Syntaxer04/RC1Computer/Version 0.2/Bridge V2/Bridge V2.kicad_pcb

## KiCad design Version 0.2/Bridge V2/Bridge V2.kicad_pcb (2026-01-20)

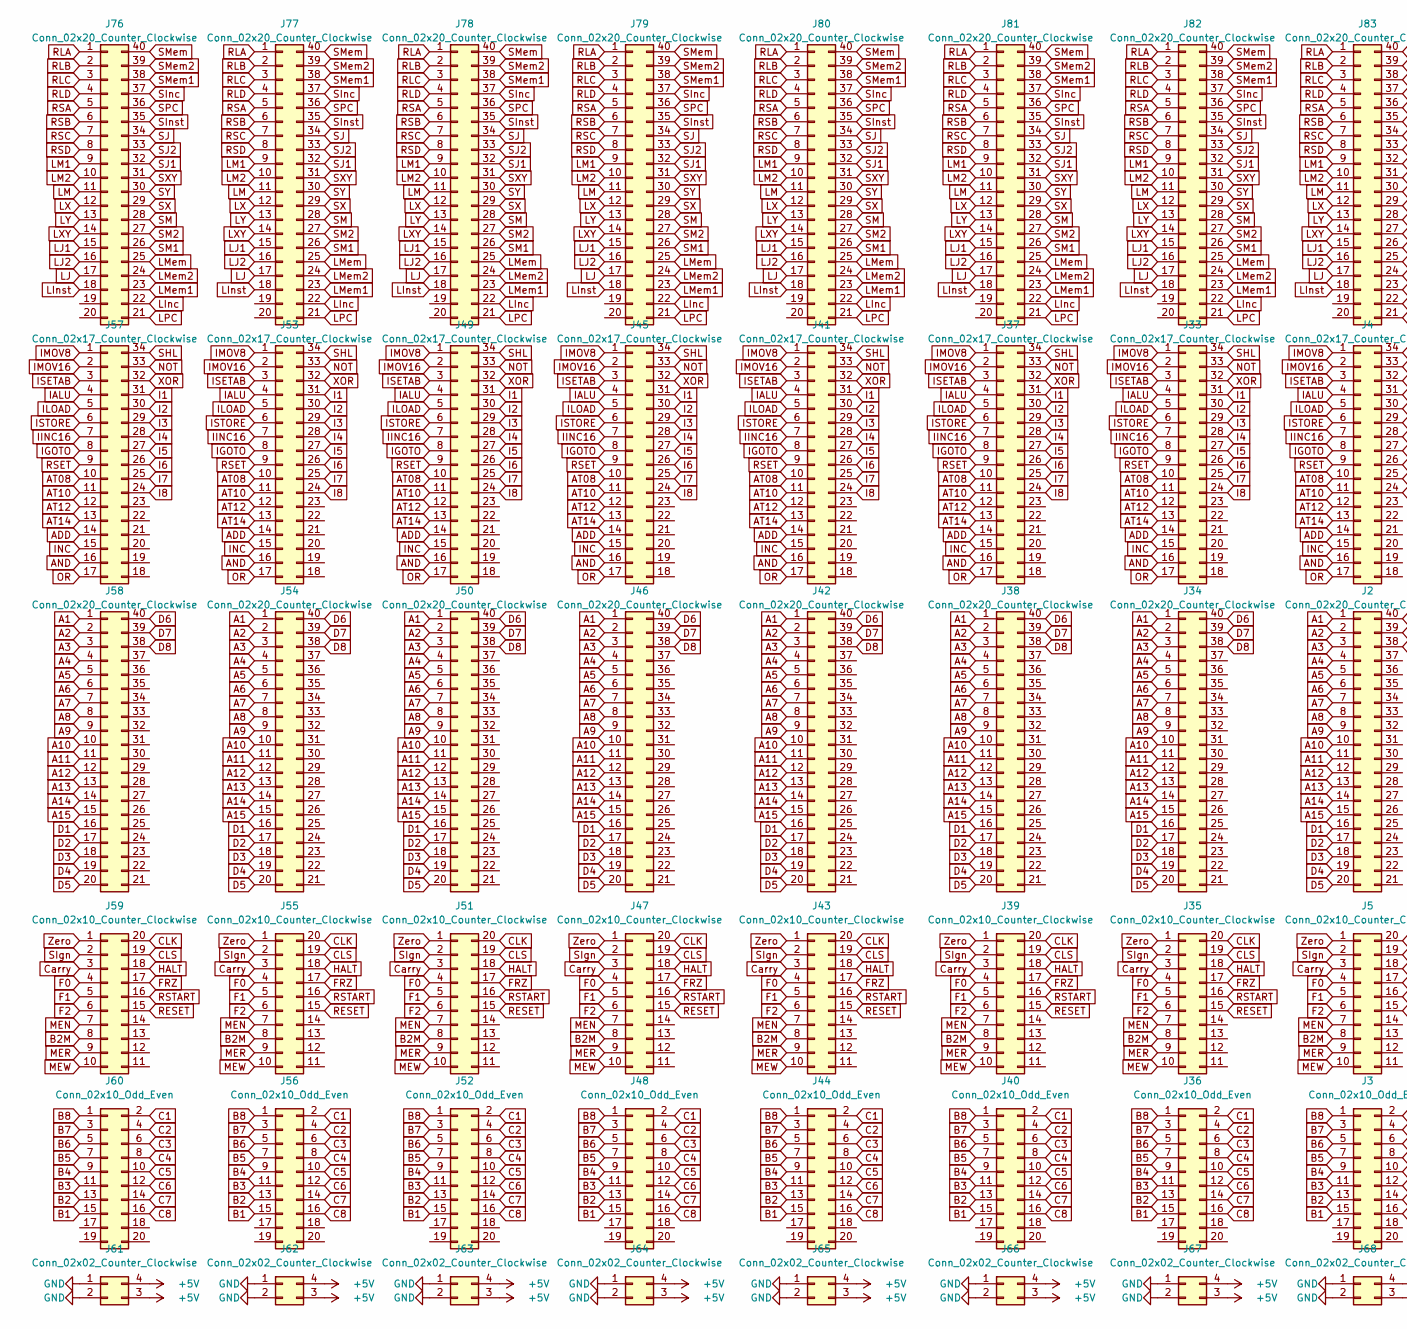
[picture p41: schematic Bridge V2.kicad_sch, part in row 1, column 1]

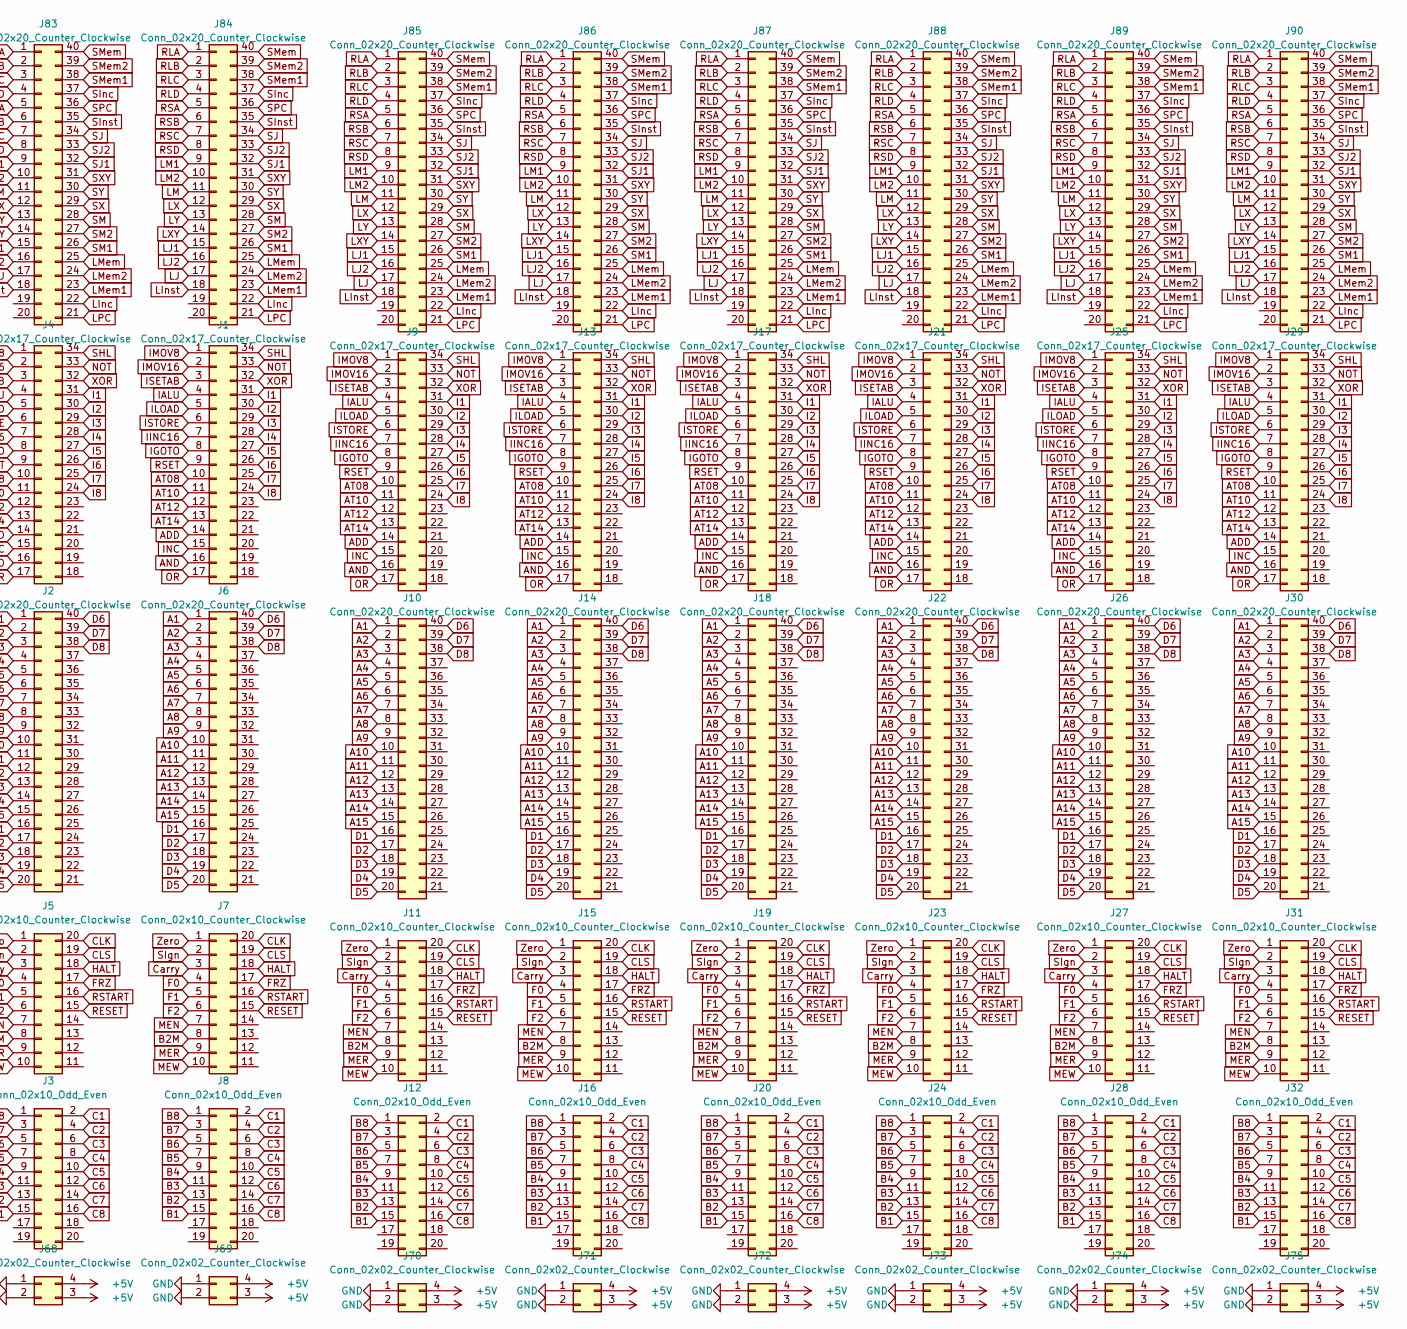
[picture p42: schematic Bridge V2.kicad_sch, part in row 1, column 2]

Parts:
J1, J4, J9, J13, J17, J21, J25, J29, J33, J37, J41, J45, J49, J53, J57: Conn_02x17_Counter_Clockwise; PinSocket_2x17_P2.54mm_Vertical
J2, J6, J10, J14, J18, J22, J26, J30, J34, J38, J42, J46, J50, J54, J58, J76, J77, J78, J79, J80, J81, J82, J83, J84, J85, J86, J87, J88, J89, J90: Conn_02x20_Counter_Clockwise; PinSocket_2x20_P2.54mm_Vertical
J3, J8, J12, J16, J20, J24, J28, J32, J36, J40, J44, J48, J52, J56, J60: Conn_02x10_Odd_Even; PinSocket_2x10_P2.54mm_Vertical
J5, J7, J11, J15, J19, J23, J27, J31, J35, J39, J43, J47, J51, J55, J59: Conn_02x10_Counter_Clockwise; PinSocket_2x10_P2.54mm_Vertical
J61, J62, J63, J64, J65, J66, J67, J68, J69, J70, J71, J72, J73, J74, J75: Conn_02x02_Counter_Clockwise; PinSocket_2x02_P2.54mm_Vertical

Connections:
+5V: J61.3, J61.4, J62.3, J62.4, J63.3, J63.4, J64.3, J64.4, J65.3, J65.4, J66.3, J66.4, J67.3, J67.4, J68.3, J68.4, J69.3, J69.4, J70.3, J70.4, J71.3, J71.4, J72.3, J72.4, J73.3, J73.4, J74.3, J74.4, J75.3, J75.4
A1: J2.1, J6.1, J10.1, J14.1, J18.1, J22.1, J26.1, J30.1, J34.1, J38.1, J42.1, J46.1, J50.1, J54.1, J58.1
A2: J2.2, J6.2, J10.2, J14.2, J18.2, J22.2, J26.2, J30.2, J34.2, J38.2, J42.2, J46.2, J50.2, J54.2, J58.2
A3: J2.3, J6.3, J10.3, J14.3, J18.3, J22.3, J26.3, J30.3, J34.3, J38.3, J42.3, J46.3, J50.3, J54.3, J58.3
A4: J2.4, J6.4, J10.4, J14.4, J18.4, J22.4, J26.4, J30.4, J34.4, J38.4, J42.4, J46.4, J50.4, J54.4, J58.4
A5: J2.5, J6.5, J10.5, J14.5, J18.5, J22.5, J26.5, J30.5, J34.5, J38.5, J42.5, J46.5, J50.5, J54.5, J58.5
A6: J2.6, J6.6, J10.6, J14.6, J18.6, J22.6, J26.6, J30.6, J34.6, J38.6, J42.6, J46.6, J50.6, J54.6, J58.6
A7: J2.7, J6.7, J10.7, J14.7, J18.7, J22.7, J26.7, J30.7, J34.7, J38.7, J42.7, J46.7, J50.7, J54.7, J58.7
A8: J2.8, J6.8, J10.8, J14.8, J18.8, J22.8, J26.8, J30.8, J34.8, J38.8, J42.8, J46.8, J50.8, J54.8, J58.8
A9: J2.9, J6.9, J10.9, J14.9, J18.9, J22.9, J26.9, J30.9, J34.9, J38.9, J42.9, J46.9, J50.9, J54.9, J58.9
A10: J2.10, J6.10, J10.10, J14.10, J18.10, J22.10, J26.10, J30.10, J34.10, J38.10, J42.10, J46.10, J50.10, J54.10, J58.10
A11: J2.11, J6.11, J10.11, J14.11, J18.11, J22.11, J26.11, J30.11, J34.11, J38.11, J42.11, J46.11, J50.11, J54.11, J58.11
A12: J2.12, J6.12, J10.12, J14.12, J18.12, J22.12, J26.12, J30.12, J34.12, J38.12, J42.12, J46.12, J50.12, J54.12, J58.12
A13: J2.13, J6.13, J10.13, J14.13, J18.13, J22.13, J26.13, J30.13, J34.13, J38.13, J42.13, J46.13, J50.13, J54.13, J58.13
A14: J2.14, J6.14, J10.14, J14.14, J18.14, J22.14, J26.14, J30.14, J34.14, J38.14, J42.14, J46.14, J50.14, J54.14, J58.14
A15: J2.15, J6.15, J10.15, J14.15, J18.15, J22.15, J26.15, J30.15, J34.15, J38.15, J42.15, J46.15, J50.15, J54.15, J58.15
ADD: J1.14, J4.14, J9.14, J13.14, J17.14, J21.14, J25.14, J29.14, J33.14, J37.14, J41.14, J45.14, J49.14, J53.14, J57.14
AND: J1.16, J4.16, J9.16, J13.16, J17.16, J21.16, J25.16, J29.16, J33.16, J37.16, J41.16, J45.16, J49.16, J53.16, J57.16
AT08: J1.10, J4.10, J9.10, J13.10, J17.10, J21.10, J25.10, J29.10, J33.10, J37.10, J41.10, J45.10, J49.10, J53.10, J57.10
AT10: J1.11, J4.11, J9.11, J13.11, J17.11, J21.11, J25.11, J29.11, J33.11, J37.11, J41.11, J45.11, J49.11, J53.11, J57.11
AT12: J1.12, J4.12, J9.12, J13.12, J17.12, J21.12, J25.12, J29.12, J33.12, J37.12, J41.12, J45.12, J49.12, J53.12, J57.12
AT14: J1.13, J4.13, J9.13, J13.13, J17.13, J21.13, J25.13, J29.13, J33.13, J37.13, J41.13, J45.13, J49.13, J53.13, J57.13
B1: J3.15, J8.15, J12.15, J16.15, J20.15, J24.15, J28.15, J32.15, J36.15, J40.15, J44.15, J48.15, J52.15, J56.15, J60.15
B2: J3.13, J8.13, J12.13, J16.13, J20.13, J24.13, J28.13, J32.13, J36.13, J40.13, J44.13, J48.13, J52.13, J56.13, J60.13
B2M: J5.8, J7.8, J11.8, J15.8, J19.8, J23.8, J27.8, J31.8, J35.8, J39.8, J43.8, J47.8, J51.8, J55.8, J59.8
B3: J3.11, J8.11, J12.11, J16.11, J20.11, J24.11, J28.11, J32.11, J36.11, J40.11, J44.11, J48.11, J52.11, J56.11, J60.11
B4: J3.9, J8.9, J12.9, J16.9, J20.9, J24.9, J28.9, J32.9, J36.9, J40.9, J44.9, J48.9, J52.9, J56.9, J60.9
B5: J3.7, J8.7, J12.7, J16.7, J20.7, J24.7, J28.7, J32.7, J36.7, J40.7, J44.7, J48.7, J52.7, J56.7, J60.7
B6: J3.5, J8.5, J12.5, J16.5, J20.5, J24.5, J28.5, J32.5, J36.5, J40.5, J44.5, J48.5, J52.5, J56.5, J60.5
B7: J3.3, J8.3, J12.3, J16.3, J20.3, J24.3, J28.3, J32.3, J36.3, J40.3, J44.3, J48.3, J52.3, J56.3, J60.3
B8: J3.1, J8.1, J12.1, J16.1, J20.1, J24.1, J28.1, J32.1, J36.1, J40.1, J44.1, J48.1, J52.1, J56.1, J60.1
C1: J3.2, J8.2, J12.2, J16.2, J20.2, J24.2, J28.2, J32.2, J36.2, J40.2, J44.2, J48.2, J52.2, J56.2, J60.2
C2: J3.4, J8.4, J12.4, J16.4, J20.4, J24.4, J28.4, J32.4, J36.4, J40.4, J44.4, J48.4, J52.4, J56.4, J60.4
C3: J3.6, J8.6, J12.6, J16.6, J20.6, J24.6, J28.6, J32.6, J36.6, J40.6, J44.6, J48.6, J52.6, J56.6, J60.6
C4: J3.8, J8.8, J12.8, J16.8, J20.8, J24.8, J28.8, J32.8, J36.8, J40.8, J44.8, J48.8, J52.8, J56.8, J60.8
C5: J3.10, J8.10, J12.10, J16.10, J20.10, J24.10, J28.10, J32.10, J36.10, J40.10, J44.10, J48.10, J52.10, J56.10, J60.10
C6: J3.12, J8.12, J12.12, J16.12, J20.12, J24.12, J28.12, J32.12, J36.12, J40.12, J44.12, J48.12, J52.12, J56.12, J60.12
C7: J3.14, J8.14, J12.14, J16.14, J20.14, J24.14, J28.14, J32.14, J36.14, J40.14, J44.14, J48.14, J52.14, J56.14, J60.14
C8: J3.16, J8.16, J12.16, J16.16, J20.16, J24.16, J28.16, J32.16, J36.16, J40.16, J44.16, J48.16, J52.16, J56.16, J60.16
CLK: J5.20, J7.20, J11.20, J15.20, J19.20, J23.20, J27.20, J31.20, J35.20, J39.20, J43.20, J47.20, J51.20, J55.20, J59.20
CLS: J5.19, J7.19, J11.19, J15.19, J19.19, J23.19, J27.19, J31.19, J35.19, J39.19, J43.19, J47.19, J51.19, J55.19, J59.19
Carry: J5.3, J7.3, J11.3, J15.3, J19.3, J23.3, J27.3, J31.3, J35.3, J39.3, J43.3, J47.3, J51.3, J55.3, J59.3
D1: J2.16, J6.16, J10.16, J14.16, J18.16, J22.16, J26.16, J30.16, J34.16, J38.16, J42.16, J46.16, J50.16, J54.16, J58.16
D2: J2.17, J6.17, J10.17, J14.17, J18.17, J22.17, J26.17, J30.17, J34.17, J38.17, J42.17, J46.17, J50.17, J54.17, J58.17
D3: J2.18, J6.18, J10.18, J14.18, J18.18, J22.18, J26.18, J30.18, J34.18, J38.18, J42.18, J46.18, J50.18, J54.18, J58.18
D4: J2.19, J6.19, J10.19, J14.19, J18.19, J22.19, J26.19, J30.19, J34.19, J38.19, J42.19, J46.19, J50.19, J54.19, J58.19
D5: J2.20, J6.20, J10.20, J14.20, J18.20, J22.20, J26.20, J30.20, J34.20, J38.20, J42.20, J46.20, J50.20, J54.20, J58.20
D6: J2.40, J6.40, J10.40, J14.40, J18.40, J22.40, J26.40, J30.40, J34.40, J38.40, J42.40, J46.40, J50.40, J54.40, J58.40
D7: J2.39, J6.39, J10.39, J14.39, J18.39, J22.39, J26.39, J30.39, J34.39, J38.39, J42.39, J46.39, J50.39, J54.39, J58.39
D8: J2.38, J6.38, J10.38, J14.38, J18.38, J22.38, J26.38, J30.38, J34.38, J38.38, J42.38, J46.38, J50.38, J54.38, J58.38
F0: J5.4, J7.4, J11.4, J15.4, J19.4, J23.4, J27.4, J31.4, J35.4, J39.4, J43.4, J47.4, J51.4, J55.4, J59.4
F1: J5.5, J7.5, J11.5, J15.5, J19.5, J23.5, J27.5, J31.5, J35.5, J39.5, J43.5, J47.5, J51.5, J55.5, J59.5
F2: J5.6, J7.6, J11.6, J15.6, J19.6, J23.6, J27.6, J31.6, J35.6, J39.6, J43.6, J47.6, J51.6, J55.6, J59.6
FRZ: J5.17, J7.17, J11.17, J15.17, J19.17, J23.17, J27.17, J31.17, J35.17, J39.17, J43.17, J47.17, J51.17, J55.17, J59.17
GND: J61.1, J61.2, J62.1, J62.2, J63.1, J63.2, J64.1, J64.2, J65.1, J65.2, J66.1, J66.2, J67.1, J67.2, J68.1, J68.2, J69.1, J69.2, J70.1, J70.2, J71.1, J71.2, J72.1, J72.2, J73.1, J73.2, J74.1, J74.2, J75.1, J75.2
HALT: J5.18, J7.18, J11.18, J15.18, J19.18, J23.18, J27.18, J31.18, J35.18, J39.18, J43.18, J47.18, J51.18, J55.18, J59.18
I1: J1.31, J4.31, J9.31, J13.31, J17.31, J21.31, J25.31, J29.31, J33.31, J37.31, J41.31, J45.31, J49.31, J53.31, J57.31
I2: J1.30, J4.30, J9.30, J13.30, J17.30, J21.30, J25.30, J29.30, J33.30, J37.30, J41.30, J45.30, J49.30, J53.30, J57.30
I3: J1.29, J4.29, J9.29, J13.29, J17.29, J21.29, J25.29, J29.29, J33.29, J37.29, J41.29, J45.29, J49.29, J53.29, J57.29
I4: J1.28, J4.28, J9.28, J13.28, J17.28, J21.28, J25.28, J29.28, J33.28, J37.28, J41.28, J45.28, J49.28, J53.28, J57.28
I5: J1.27, J4.27, J9.27, J13.27, J17.27, J21.27, J25.27, J29.27, J33.27, J37.27, J41.27, J45.27, J49.27, J53.27, J57.27
I6: J1.26, J4.26, J9.26, J13.26, J17.26, J21.26, J25.26, J29.26, J33.26, J37.26, J41.26, J45.26, J49.26, J53.26, J57.26
I7: J1.25, J4.25, J9.25, J13.25, J17.25, J21.25, J25.25, J29.25, J33.25, J37.25, J41.25, J45.25, J49.25, J53.25, J57.25
I8: J1.24, J4.24, J9.24, J13.24, J17.24, J21.24, J25.24, J29.24, J33.24, J37.24, J41.24, J45.24, J49.24, J53.24, J57.24
IALU: J1.4, J4.4, J9.4, J13.4, J17.4, J21.4, J25.4, J29.4, J33.4, J37.4, J41.4, J45.4, J49.4, J53.4, J57.4
IGOTO: J1.8, J4.8, J9.8, J13.8, J17.8, J21.8, J25.8, J29.8, J33.8, J37.8, J41.8, J45.8, J49.8, J53.8, J57.8
IINC16: J1.7, J4.7, J9.7, J13.7, J17.7, J21.7, J25.7, J29.7, J33.7, J37.7, J41.7, J45.7, J49.7, J53.7, J57.7
ILOAD: J1.5, J4.5, J9.5, J13.5, J17.5, J21.5, J25.5, J29.5, J33.5, J37.5, J41.5, J45.5, J49.5, J53.5, J57.5
IMOV8: J1.1, J4.1, J9.1, J13.1, J17.1, J21.1, J25.1, J29.1, J33.1, J37.1, J41.1, J45.1, J49.1, J53.1, J57.1
IMOV16: J1.2, J4.2, J9.2, J13.2, J17.2, J21.2, J25.2, J29.2, J33.2, J37.2, J41.2, J45.2, J49.2, J53.2, J57.2
INC: J1.15, J4.15, J9.15, J13.15, J17.15, J21.15, J25.15, J29.15, J33.15, J37.15, J41.15, J45.15, J49.15, J53.15, J57.15
ISETAB: J1.3, J4.3, J9.3, J13.3, J17.3, J21.3, J25.3, J29.3, J33.3, J37.3, J41.3, J45.3, J49.3, J53.3, J57.3
ISTORE: J1.6, J4.6, J9.6, J13.6, J17.6, J21.6, J25.6, J29.6, J33.6, J37.6, J41.6, J45.6, J49.6, J53.6, J57.6
LInc: J76.22, J77.22, J78.22, J79.22, J80.22, J81.22, J82.22, J83.22, J84.22, J85.22, J86.22, J87.22, J88.22, J89.22, J90.22
LInst: J76.18, J77.18, J78.18, J79.18, J80.18, J81.18, J82.18, J83.18, J84.18, J85.18, J86.18, J87.18, J88.18, J89.18, J90.18
LJ1: J76.15, J77.15, J78.15, J79.15, J80.15, J81.15, J82.15, J83.15, J84.15, J85.15, J86.15, J87.15, J88.15, J89.15, J90.15
LJ2: J76.16, J77.16, J78.16, J79.16, J80.16, J81.16, J82.16, J83.16, J84.16, J85.16, J86.16, J87.16, J88.16, J89.16, J90.16
LJ: J76.17, J77.17, J78.17, J79.17, J80.17, J81.17, J82.17, J83.17, J84.17, J85.17, J86.17, J87.17, J88.17, J89.17, J90.17
LM: J76.11, J77.11, J78.11, J79.11, J80.11, J81.11, J82.11, J83.11, J84.11, J85.11, J86.11, J87.11, J88.11, J89.11, J90.11
LM1: J76.9, J77.9, J78.9, J79.9, J80.9, J81.9, J82.9, J83.9, J84.9, J85.9, J86.9, J87.9, J88.9, J89.9, J90.9
LM2: J76.10, J77.10, J78.10, J79.10, J80.10, J81.10, J82.10, J83.10, J84.10, J85.10, J86.10, J87.10, J88.10, J89.10, J90.10
LMem: J76.25, J77.25, J78.25, J79.25, J80.25, J81.25, J82.25, J83.25, J84.25, J85.25, J86.25, J87.25, J88.25, J89.25, J90.25
LMem1: J76.23, J77.23, J78.23, J79.23, J80.23, J81.23, J82.23, J83.23, J84.23, J85.23, J86.23, J87.23, J88.23, J89.23, J90.23
LMem2: J76.24, J77.24, J78.24, J79.24, J80.24, J81.24, J82.24, J83.24, J84.24, J85.24, J86.24, J87.24, J88.24, J89.24, J90.24
LPC: J76.21, J77.21, J78.21, J79.21, J80.21, J81.21, J82.21, J83.21, J84.21, J85.21, J86.21, J87.21, J88.21, J89.21, J90.21
LX: J76.12, J77.12, J78.12, J79.12, J80.12, J81.12, J82.12, J83.12, J84.12, J85.12, J86.12, J87.12, J88.12, J89.12, J90.12
LXY: J76.14, J77.14, J78.14, J79.14, J80.14, J81.14, J82.14, J83.14, J84.14, J85.14, J86.14, J87.14, J88.14, J89.14, J90.14
LY: J76.13, J77.13, J78.13, J79.13, J80.13, J81.13, J82.13, J83.13, J84.13, J85.13, J86.13, J87.13, J88.13, J89.13, J90.13
MEN: J5.7, J7.7, J11.7, J15.7, J19.7, J23.7, J27.7, J31.7, J35.7, J39.7, J43.7, J47.7, J51.7, J55.7, J59.7
MER: J5.9, J7.9, J11.9, J15.9, J19.9, J23.9, J27.9, J31.9, J35.9, J39.9, J43.9, J47.9, J51.9, J55.9, J59.9
MEW: J5.10, J7.10, J11.10, J15.10, J19.10, J23.10, J27.10, J31.10, J35.10, J39.10, J43.10, J47.10, J51.10, J55.10, J59.10
NOT: J1.33, J4.33, J9.33, J13.33, J17.33, J21.33, J25.33, J29.33, J33.33, J37.33, J41.33, J45.33, J49.33, J53.33, J57.33
OR: J1.17, J4.17, J9.17, J13.17, J17.17, J21.17, J25.17, J29.17, J33.17, J37.17, J41.17, J45.17, J49.17, J53.17, J57.17
RESET: J5.15, J7.15, J11.15, J15.15, J19.15, J23.15, J27.15, J31.15, J35.15, J39.15, J43.15, J47.15, J51.15, J55.15, J59.15
RLA: J76.1, J77.1, J78.1, J79.1, J80.1, J81.1, J82.1, J83.1, J84.1, J85.1, J86.1, J87.1, J88.1, J89.1, J90.1
RLB: J76.2, J77.2, J78.2, J79.2, J80.2, J81.2, J82.2, J83.2, J84.2, J85.2, J86.2, J87.2, J88.2, J89.2, J90.2
RLC: J76.3, J77.3, J78.3, J79.3, J80.3, J81.3, J82.3, J83.3, J84.3, J85.3, J86.3, J87.3, J88.3, J89.3, J90.3
RLD: J76.4, J77.4, J78.4, J79.4, J80.4, J81.4, J82.4, J83.4, J84.4, J85.4, J86.4, J87.4, J88.4, J89.4, J90.4
RSA: J76.5, J77.5, J78.5, J79.5, J80.5, J81.5, J82.5, J83.5, J84.5, J85.5, J86.5, J87.5, J88.5, J89.5, J90.5
RSB: J76.6, J77.6, J78.6, J79.6, J80.6, J81.6, J82.6, J83.6, J84.6, J85.6, J86.6, J87.6, J88.6, J89.6, J90.6
RSC: J76.7, J77.7, J78.7, J79.7, J80.7, J81.7, J82.7, J83.7, J84.7, J85.7, J86.7, J87.7, J88.7, J89.7, J90.7
RSD: J76.8, J77.8, J78.8, J79.8, J80.8, J81.8, J82.8, J83.8, J84.8, J85.8, J86.8, J87.8, J88.8, J89.8, J90.8
RSET: J1.9, J4.9, J9.9, J13.9, J17.9, J21.9, J25.9, J29.9, J33.9, J37.9, J41.9, J45.9, J49.9, J53.9, J57.9
RSTART: J5.16, J7.16, J11.16, J15.16, J19.16, J23.16, J27.16, J31.16, J35.16, J39.16, J43.16, J47.16, J51.16, J55.16, J59.16
SHL: J1.34, J4.34, J9.34, J13.34, J17.34, J21.34, J25.34, J29.34, J33.34, J37.34, J41.34, J45.34, J49.34, J53.34, J57.34
SIgn: J5.2, J7.2, J11.2, J15.2, J19.2, J23.2, J27.2, J31.2, J35.2, J39.2, J43.2, J47.2, J51.2, J55.2, J59.2
SInc: J76.37, J77.37, J78.37, J79.37, J80.37, J81.37, J82.37, J83.37, J84.37, J85.37, J86.37, J87.37, J88.37, J89.37, J90.37
SInst: J76.35, J77.35, J78.35, J79.35, J80.35, J81.35, J82.35, J83.35, J84.35, J85.35, J86.35, J87.35, J88.35, J89.35, J90.35
SJ1: J76.32, J77.32, J78.32, J79.32, J80.32, J81.32, J82.32, J83.32, J84.32, J85.32, J86.32, J87.32, J88.32, J89.32, J90.32
SJ2: J76.33, J77.33, J78.33, J79.33, J80.33, J81.33, J82.33, J83.33, J84.33, J85.33, J86.33, J87.33, J88.33, J89.33, J90.33
SJ: J76.34, J77.34, J78.34, J79.34, J80.34, J81.34, J82.34, J83.34, J84.34, J85.34, J86.34, J87.34, J88.34, J89.34, J90.34
SM: J76.28, J77.28, J78.28, J79.28, J80.28, J81.28, J82.28, J83.28, J84.28, J85.28, J86.28, J87.28, J88.28, J89.28, J90.28
SM1: J76.26, J77.26, J78.26, J79.26, J80.26, J81.26, J82.26, J83.26, J84.26, J85.26, J86.26, J87.26, J88.26, J89.26, J90.26
SM2: J76.27, J77.27, J78.27, J79.27, J80.27, J81.27, J82.27, J83.27, J84.27, J85.27, J86.27, J87.27, J88.27, J89.27, J90.27
SMem: J76.40, J77.40, J78.40, J79.40, J80.40, J81.40, J82.40, J83.40, J84.40, J85.40, J86.40, J87.40, J88.40, J89.40, J90.40
SMem1: J76.38, J77.38, J78.38, J79.38, J80.38, J81.38, J82.38, J83.38, J84.38, J85.38, J86.38, J87.38, J88.38, J89.38, J90.38
SMem2: J76.39, J77.39, J78.39, J79.39, J80.39, J81.39, J82.39, J83.39, J84.39, J85.39, J86.39, J87.39, J88.39, J89.39, J90.39
SPC: J76.36, J77.36, J78.36, J79.36, J80.36, J81.36, J82.36, J83.36, J84.36, J85.36, J86.36, J87.36, J88.36, J89.36, J90.36
SX: J76.29, J77.29, J78.29, J79.29, J80.29, J81.29, J82.29, J83.29, J84.29, J85.29, J86.29, J87.29, J88.29, J89.29, J90.29
SXY: J76.31, J77.31, J78.31, J79.31, J80.31, J81.31, J82.31, J83.31, J84.31, J85.31, J86.31, J87.31, J88.31, J89.31, J90.31
SY: J76.30, J77.30, J78.30, J79.30, J80.30, J81.30, J82.30, J83.30, J84.30, J85.30, J86.30, J87.30, J88.30, J89.30, J90.30
XOR: J1.32, J4.32, J9.32, J13.32, J17.32, J21.32, J25.32, J29.32, J33.32, J37.32, J41.32, J45.32, J49.32, J53.32, J57.32
Zero: J5.1, J7.1, J11.1, J15.1, J19.1, J23.1, J27.1, J31.1, J35.1, J39.1, J43.1, J47.1, J51.1, J55.1, J59.1

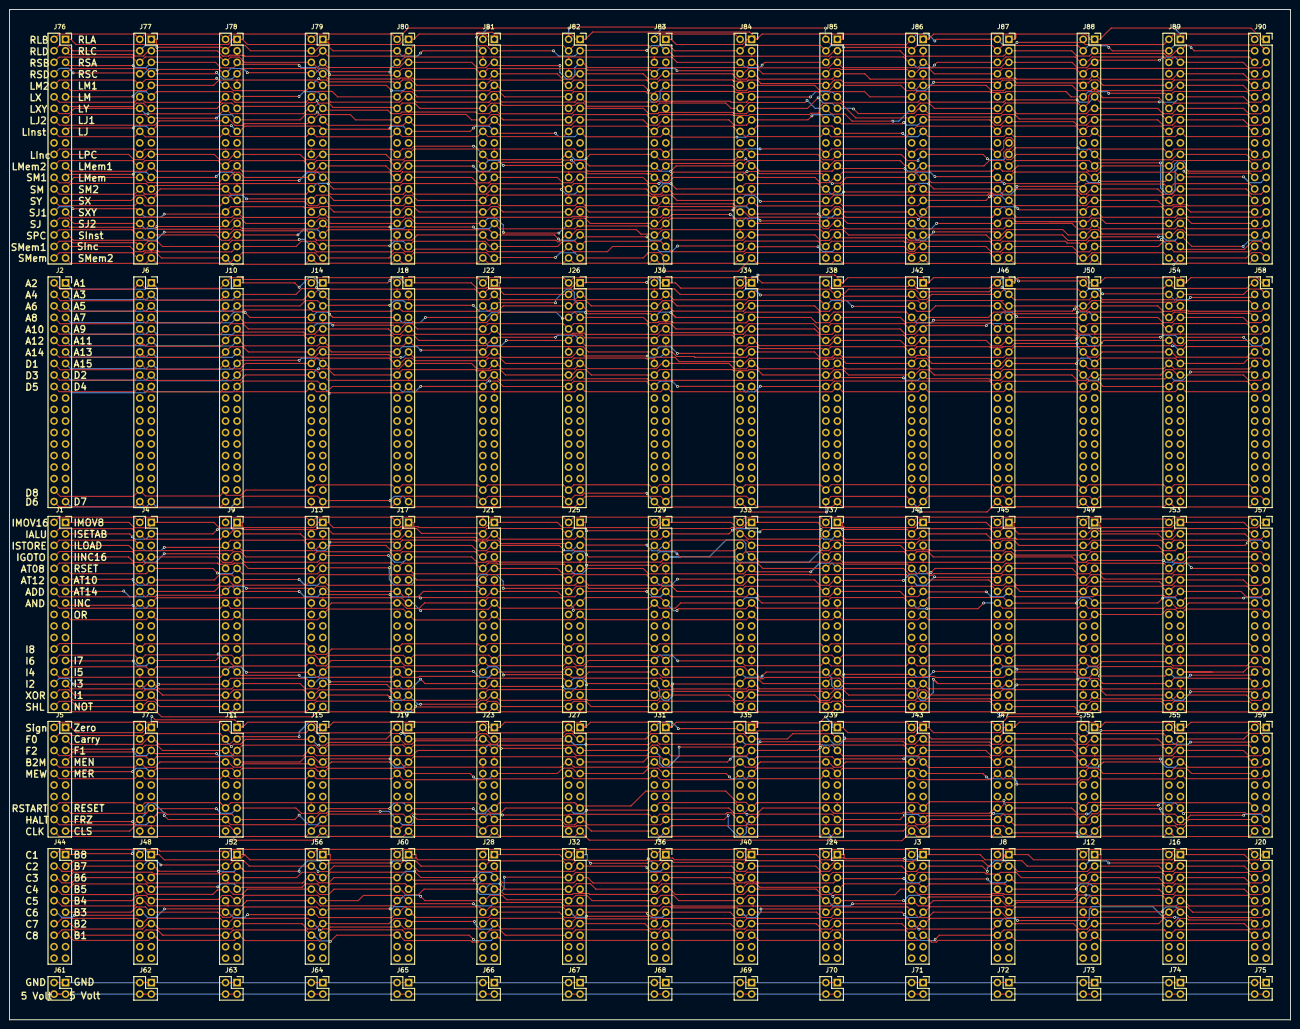
[picture p43: board Bridge V2.kicad_pcb from above]

Board: 2 copper layers, 282.7 x 222.9 mm, 90 parts (0 on the bottom side), 123 nets.
