Syntaxer04/RC1Computer/Version 0.1/Memory/Memory.kicad_pcb

## KiCad design Version 0.1/Memory/Memory.kicad_pcb (2025-06-25, an earlier design)

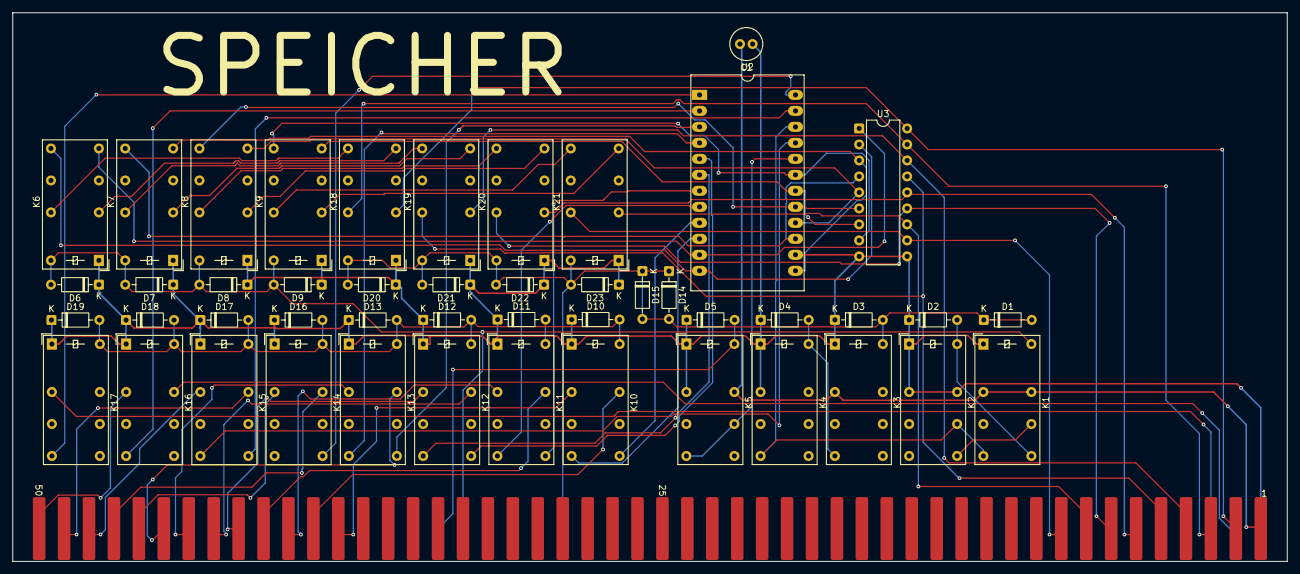
[picture p44: board Memory.kicad_pcb from above]

Board: 2 copper layers, 202.4 x 87.1 mm, 48 parts (0 on the bottom side), 63 nets.

Parts:
C1: C; C_Radial_D5.0mm_H11.0mm_P2.00mm
D1, D2, D3, D4, D5, D6, D7, D8, D9, D10, D11, D12, D13, D14, D15, D16, D17, D18, D19, D20, D21, D22, D23: 1N914; D_DO-35_SOD27_P7.62mm_Horizontal
K1, K2, K3, K4, K5, K6, K7, K8, K9, K10, K11, K12, K13, K14, K15, K16, K17, K18, K19, K20, K21: HK19F-DCxxV-SHC; Relay_DPDT_Finder_30.22
U1: Conn_RC_Male_100
U2: CY62256-70PC; DIP-24_18.0mmx34.29mm_W15.24mm_LongPads
U3: ULN2803A; DIP-18_W7.62mm

Connections:
+5V: C1.2, K1.11, K1.21, K3.11, K5.21, U1.1 (5_Volt)
A0: K10.11, U1.38 (A0)
A1: K10.21, U1.39 (A1)
A2: K11.11, U1.40 (A2)
A3: K11.21, U1.41 (A3)
A4: K12.11, U1.42 (A4)
A5: K12.21, U1.43 (A5)
A6: K13.11, U1.44 (A6)
A7: K13.21, U1.45 (A7)
A8: K14.11, U1.46 (A8)
A9: K14.21, U1.47 (A9)
A10: K15.11, U1.48 (A10)
A11: K15.21, U1.49 (A11)
A12: K16.11, U1.50 (A12)
A13: K16.21, U1.52 (A13)
A14: K17.11, U1.53 (A14)
AI0: K10.14, U2.10 (A0)
AI1: K10.24, U2.9 (A1)
AI2: K11.14, U2.8 (A2)
AI3: K11.24, U2.7 (A3)
AI4: K12.14, U2.6 (A4)
AI5: K12.24, U2.5 (A5)
AI6: K13.14, U2.4 (A6)
AI7: K13.24, U2.3 (A7)
AI9: K14.24, U2.24 (A9)
AI10: K15.14, U2.21 (A10)
AI11: K15.24, U2.23 (A11)
AI12: K16.14, U2.2 (A12)
AI14: K17.14, U2.1 (A14)
CS: K5.14, K5.22, U2.20 (~CS)
D0: K6.11, K18.14
D1: K6.21, K18.24
D2: K7.11, K19.14
D3: K7.21, K19.24
D4: K8.11, K20.14
D5: K8.21, K20.24
D6: K9.11, K21.14
D7: K9.21, K21.24
DO0: K18.11, U1.2 (D0), U3.18 (O1)
DO1: K18.21, U1.3 (D1), U3.17 (O2)
DO2: K19.11, U1.4 (D2), U3.16 (O3)
DO3: K19.21, U1.5 (D3), U3.15 (O4)
DO4: K20.11, U1.6 (D4), U3.14 (O5)
DO5: K20.21, U1.7 (D5), U3.13 (O6)
DO6: K21.11, U1.8 (D6), U3.12 (O7)
DO7: K21.21, U1.9 (D7), U3.11 (O8)
GND: C1.1, D2.1 (K), D3.1 (K), D4.1 (K), D5.1 (K), D6.1 (K), D7.1 (K), D8.1 (K), D9.1 (K), D10.1 (K), D11.1 (K), D12.1 (K), D13.1 (K), D16.1 (K), D17.1 (K), D18.1 (K), D19.1 (K), D20.1 (K), D21.1 (K), D22.1 (K), D23.1 (K), K1.A1, K2.11, K2.21, K2.A1, K3.A1, K4.11, K4.A1, K5.11, K5.A1, K6.A1, K7.A1, K8.A1, K9.A1, K10.A1, K11.A1, K12.A1, K13.A1, K14.A1, K15.A1, K16.A1, K17.A1, K18.A1, K19.A1, K20.A1, K21.A1, U1.51 (GND), U2.14 (GND), U3.9 (GND), U3.10 (COM)
MEMREAD: D1.1 (K), D1.2 (A), D3.2 (A), D14.1 (K), D14.2 (A), D15.1 (K), D15.2 (A), D20.2 (A), D21.2 (A), D22.2 (A), D23.2 (A), K3.A2, K18.A2, K19.A2, K20.A2, K21.A2, U1.79 (MEMREAD)
MEMSel: D5.2 (A), K5.A2, U1.84 (MEMSL)
MEMWRITE: D6.2 (A), D7.2 (A), D8.2 (A), D9.2 (A), K1.A2, K6.A2, K7.A2, K8.A2, K9.A2, U1.83 (MEMWRITE)
unnamed: D2.2 (A), K1.24, K2.A2
unnamed: D4.2 (A), K3.14, K4.A2
unnamed: D10.2 (A), D11.2 (A), D12.2 (A), D13.2 (A), D16.2 (A), D17.2 (A), D18.2 (A), D19.2 (A), K10.A2, K11.A2, K12.A2, K13.A2, K14.A2, K15.A2, K16.A2, K17.A2
unnamed: K6.14, U2.11 (Q0), U3.1 (I1)
unnamed: K6.24, U2.12 (Q1), U3.2 (I2)
unnamed: K7.14, U2.13 (Q2), U3.3 (I3)
unnamed: K7.24, U2.15 (Q3), U3.4 (I4)
unnamed: K8.14, U2.16 (Q4), U3.5 (I5)
unnamed: K8.24, U2.17 (Q5), U3.6 (I6)
unnamed: K9.14, U2.18 (Q6), U3.7 (I7)
unnamed: K9.24, U2.19 (Q7), U3.8 (I8)
OE: K1.14, K2.22, K4.14, U2.22 (~OE)
WE: K1.22, K2.24
