Syntaxer04/RC1Computer/Version 0.1/Decoder/Decoder.kicad_pcb

## KiCad design Version 0.1/Decoder/Decoder.kicad_pcb (2025-06-25, an earlier design)

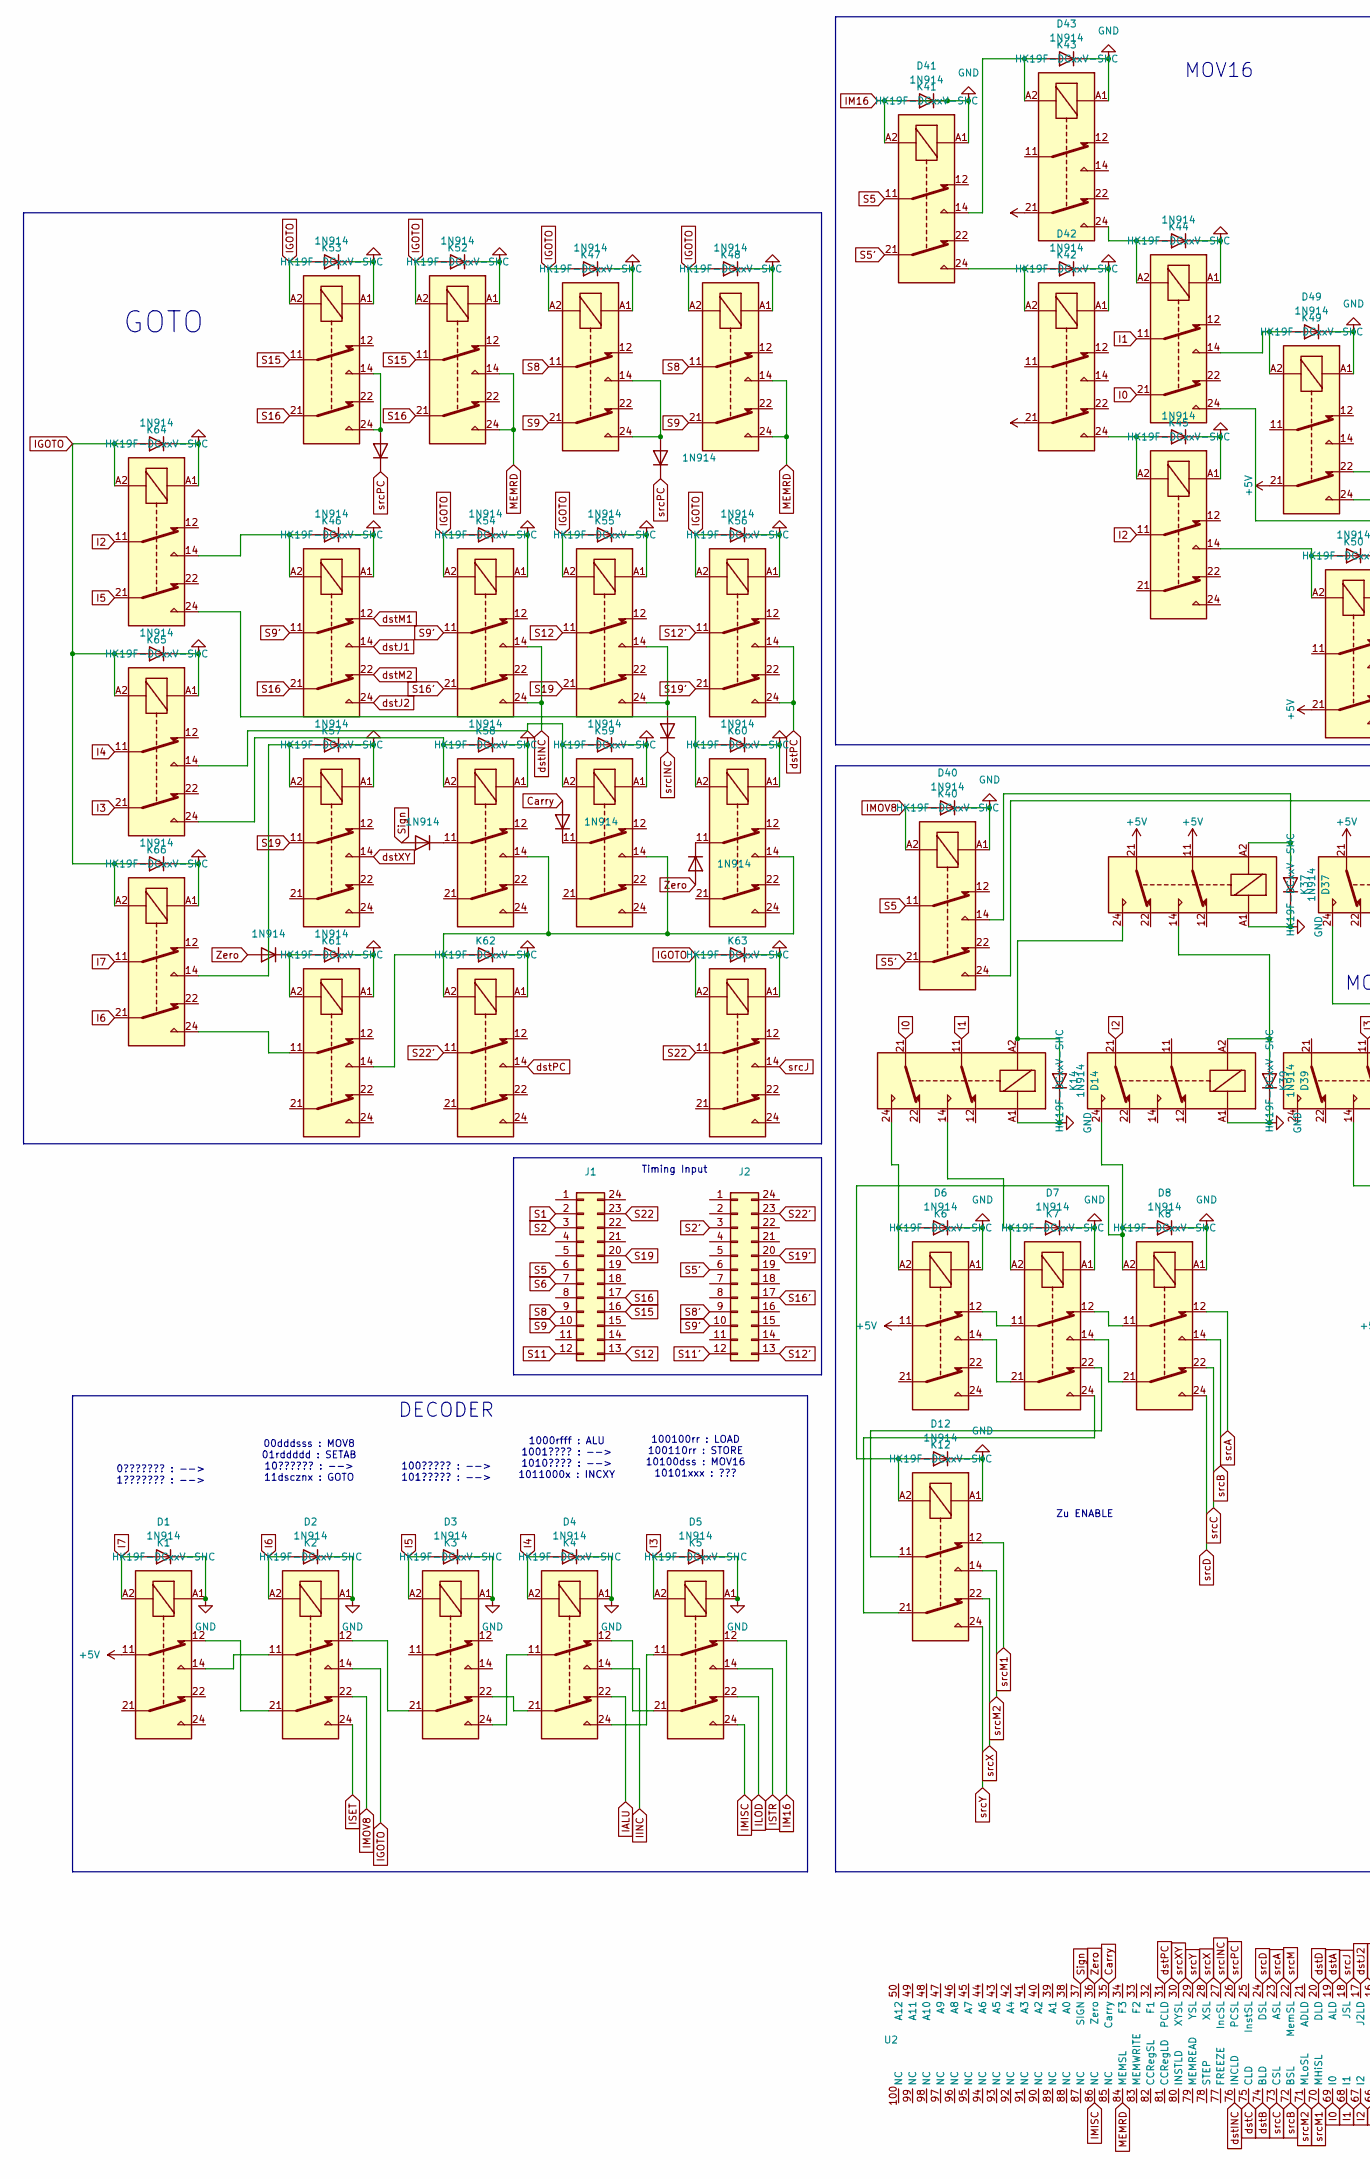
[picture p45: schematic Decoder.kicad_sch, part in row 1, column 1]

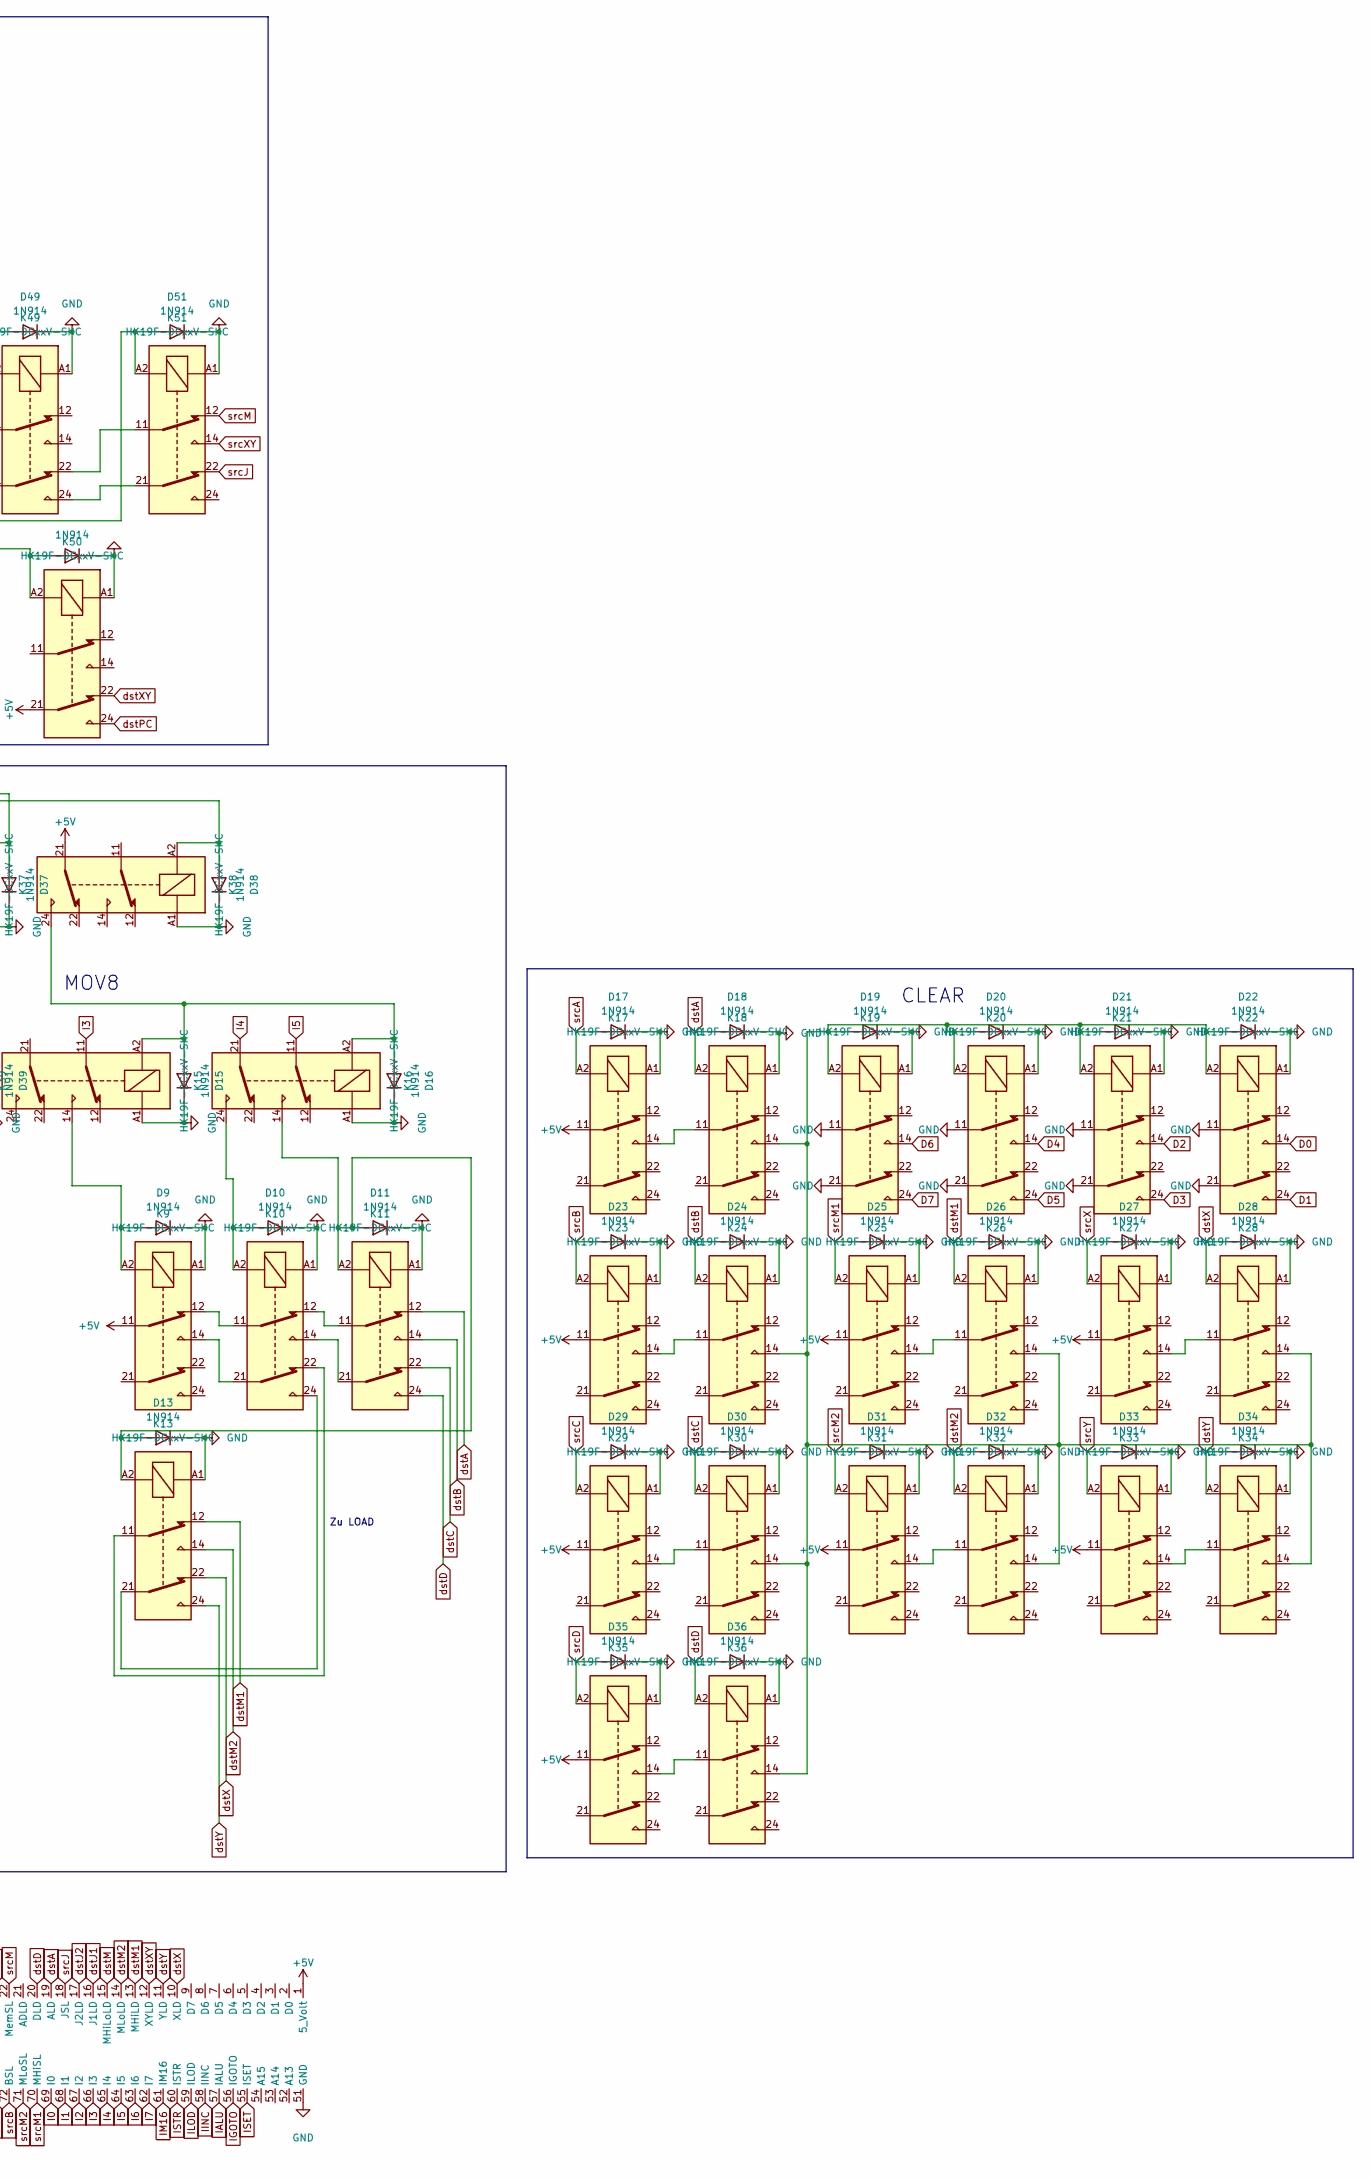
[picture p46: schematic Decoder.kicad_sch, part in row 1, column 2]

Parts:
D1, D2, D3, D4, D5, D6, D7, D8, D9, D10, D11, D12, D13, D14, D15, D16, D17, D18, D19, D20, D21, D22, D23, D24, D25, D26, D27, D28, D29, D30, D31, D32, D33, D34, D35, D36, D37, D38, D39, D40, D41, D42, D43, D44, D45, D46, D47, D48, D49, D50, D51, D52, D53, D54, D55, D56, D57, D58, D59, D60, D61, D62, D63, D64, D65, D66, D67, D68, D69, D70, D71, D72, D73: 1N914; D_DO-35_SOD27_P7.62mm_Horizontal
J1, J2: Conn_02x12_Counter_Clockwise; PinHeader_2x12_P2.00mm_Vertical
K1, K2, K3, K4, K5, K6, K7, K8, K9, K10, K11, K12, K13, K14, K15, K16, K17, K18, K19, K20, K21, K22, K23, K24, K25, K26, K27, K28, K29, K30, K31, K32, K33, K34, K35, K36, K37, K38, K39, K40, K41, K42, K43, K44, K45, K46, K47, K48, K49, K50, K51, K52, K53, K54, K55, K56, K57, K58, K59, K60, K61, K62, K63, K64, K65, K66: HK19F-DCxxV-SHC; Relay_DPDT_Finder_30.22
U2: Conn_RC_Male_100

Connections:
+5V: K1.11, K6.11, K9.11, K17.11, K23.11, K25.11, K27.11, K29.11, K31.11, K33.11, K35.11, K37.11, K37.21, K38.21, K42.21, K43.21, K49.21, K50.21, U2.1 (5_Volt)
Carry: D68.2 (A), U2.35 (Carry)
D0: K22.14
D1: K22.24
D2: K21.14
D3: K21.24
D4: K20.14
D5: K20.24
D6: K19.14
D7: K19.24
GND: D1.1 (K), D2.1 (K), D3.1 (K), D4.1 (K), D5.1 (K), D6.1 (K), D7.1 (K), D8.1 (K), D9.1 (K), D10.1 (K), D11.1 (K), D12.1 (K), D13.1 (K), D14.1 (K), D15.1 (K), D16.1 (K), D17.1 (K), D18.1 (K), D19.1 (K), D20.1 (K), D21.1 (K), D22.1 (K), D23.1 (K), D24.1 (K), D25.1 (K), D26.1 (K), D27.1 (K), D28.1 (K), D29.1 (K), D30.1 (K), D31.1 (K), D32.1 (K), D33.1 (K), D34.1 (K), D35.1 (K), D36.1 (K), D37.1 (K), D38.1 (K), D39.1 (K), D40.1 (K), D41.1 (K), D42.1 (K), D43.1 (K), D44.1 (K), D45.1 (K), D46.1 (K), D47.1 (K), D48.1 (K), D49.1 (K), D50.1 (K), D51.1 (K), D53.1 (K), D54.1 (K), D56.1 (K), D57.1 (K), D58.1 (K), D60.1 (K), D61.1 (K), D62.1 (K), D63.1 (K), D64.1 (K), D65.1 (K), D70.1 (K), D71.1 (K), D72.1 (K), D73.1 (K), K1.A1, K2.A1, K3.A1, K4.A1, K5.A1, K6.A1, K7.A1, K8.A1, K9.A1, K10.A1, K11.A1, K12.A1, K13.A1, K14.A1, K15.A1, K16.A1, K17.A1, K18.A1, K19.11, K19.21, K19.A1, K20.11, K20.21, K20.A1, K21.11, K21.21, K21.A1, K22.11, K22.21, K22.A1, K23.A1, K24.A1, K25.A1, K26.A1, K27.A1, K28.A1, K29.A1, K30.A1, K31.A1, K32.A1, K33.A1, K34.A1, K35.A1, K36.A1, K37.A1, K38.A1, K39.A1, K40.A1, K41.A1, K42.A1, K43.A1, K44.A1, K45.A1, K46.A1, K47.A1, K48.A1, K49.A1, K50.A1, K51.A1, K52.A1, K53.A1, K54.A1, K55.A1, K56.A1, K57.A1, K58.A1, K59.A1, K60.A1, K61.A1, K62.A1, K63.A1, K64.A1, K65.A1, K66.A1, U2.51 (GND)
I0: K14.21, K44.21, U2.69 (I0)
I1: K14.11, K44.11, U2.68 (I1)
I2: K39.21, K45.11, K64.11, U2.67 (I2)
I3: D5.2 (A), K5.A2, K15.11, K65.21, U2.66 (I3)
I4: D4.2 (A), K4.A2, K16.21, K65.11, U2.65 (I4)
I5: D3.2 (A), K3.A2, K16.11, K64.21, U2.64 (I5)
I6: D2.2 (A), K2.A2, K66.21, U2.63 (I6)
I7: D1.2 (A), K1.A2, K66.11, U2.62 (I7)
IALU: K4.22, U2.57 (IALU)
IGOTO: D47.2 (A), D48.2 (A), D53.2 (A), D54.2 (A), D56.2 (A), D57.2 (A), D58.2 (A), D70.2 (A), D71.2 (A), D72.2 (A), D73.2 (A), K2.14, K47.A2, K48.A2, K52.A2, K53.A2, K54.A2, K55.A2, K56.A2, K63.A2, K64.A2, K65.A2, K66.A2, U2.56 (IGOTO)
IINC: K4.14, U2.58 (IINC)
ILOD: K5.22, U2.59 (ILOD)
IM16: D41.2 (A), K5.12, K41.A2, U2.61 (IM16)
IMISC: K5.24, U2.86 (NC)
IMOV8: D40.2 (A), K2.22, K40.A2
ISET: K2.24, U2.55 (ISET)
ISTR: K5.14, U2.60 (ISTR)
MEMRD: K48.14, K48.24, K52.14, K52.24, U2.84 (MEMSL)
unnamed: D6.2 (A), K6.A2, K14.24
unnamed: D7.2 (A), K7.A2, K14.14
unnamed: D9.2 (A), K9.A2, K15.14
unnamed: D10.2 (A), K10.A2, K16.24
unnamed: D11.2 (A), D13.2 (A), K11.A2, K13.A2, K16.14
unnamed: D8.2 (A), D12.2 (A), K8.A2, K12.A2, K39.24
unnamed: D14.2 (A), K14.A2, K37.24
unnamed: D15.2 (A), D16.2 (A), K15.A2, K16.A2, K38.24
unnamed: D19.2 (A), D20.2 (A), D21.2 (A), D22.2 (A), K18.14, K19.A2, K20.A2, K21.A2, K22.A2, K24.14, K26.14, K28.14, K30.14, K32.14, K34.14, K36.14
unnamed: D37.2 (A), K37.A2, K40.14
unnamed: D38.2 (A), K38.A2, K40.24
unnamed: D39.2 (A), K37.14, K39.A2
unnamed: D42.2 (A), K41.24, K42.A2
unnamed: D43.2 (A), K41.14, K43.A2
unnamed: D44.2 (A), K43.24, K44.A2
unnamed: D45.2 (A), K42.24, K45.A2
unnamed: D46.2 (A), K46.A2, K64.14
unnamed: D49.2 (A), K44.14, K49.A2
unnamed: D50.2 (A), K45.14, K50.A2
unnamed: D51.2 (A), K44.24, K51.A2
unnamed: D52.2 (A), K47.14, K47.24
unnamed: D55.2 (A), K53.14, K53.24
unnamed: D59.2 (A), K55.14, K55.24
unnamed: D60.2 (A), K57.A2, K66.14
unnamed: D61.2 (A), K58.A2, K65.24
unnamed: D62.2 (A), K59.A2, K65.14
unnamed: D63.2 (A), K60.A2, K64.24
unnamed: D64.2 (A), D66.1 (K), K61.A2
unnamed: D65.2 (A), K58.14, K59.14, K60.14, K61.14, K62.A2
unnamed: D67.1 (K), K58.11
unnamed: D68.1 (K), K59.11
unnamed: D69.1 (K), K60.11
unnamed: K1.12, K2.21
unnamed: K1.14, K2.11
unnamed: K2.12, K3.21
unnamed: K3.22, K4.21
unnamed: K3.24, K4.11
unnamed: K4.12, K5.21
unnamed: K4.24, K5.11
unnamed: K6.12, K7.11
unnamed: K6.14, K7.21
unnamed: K7.12, K8.11
unnamed: K7.14, K8.21
unnamed: K9.12, K10.11
unnamed: K10.12, K11.11
unnamed: K10.14, K11.21
unnamed: K9.14, K10.21
unnamed: K10.22, K13.11
unnamed: K10.24, K13.21
unnamed: K7.22, K12.11
unnamed: K7.24, K12.21
unnamed: K17.14, K18.11
unnamed: K23.14, K24.11
unnamed: K25.14, K26.11
unnamed: K27.14, K28.11
unnamed: K29.14, K30.11
unnamed: K31.14, K32.11
unnamed: K33.14, K34.11
unnamed: K35.14, K36.11
unnamed: K49.22, K51.11
unnamed: K49.24, K51.21
unnamed: K61.11, K66.24
S1: J1.2
S2: J1.3
S2': J2.3
S5: J1.6, K40.11, K41.11
S5': J2.6, K40.21, K41.21
S6: J1.7
S8: J1.9, K47.11, K48.11
S8': J2.9
S9: J1.10, K47.21, K48.21
S9': J2.10, K46.11, K54.11
S11: J1.12
S11': J2.12
S12: J1.13, K55.11
S12': J2.13, K56.11
S15: J1.16, K52.11, K53.11
S16: J1.17, K46.21, K52.21, K53.21
S16': J2.17, K54.21
S19: J1.20, K55.21, K57.11
S19': J2.20, K56.21
S22: J1.23, K63.11
S22': J2.23, K62.11
Sign: D67.2 (A), U2.37 (SIGN)
Zero: D66.2 (A), D69.2 (A), U2.36 (Zero)
dstA: D18.2 (A), K11.12, K18.A2, U2.19 (ALD)
dstB: D24.2 (A), K11.14, K24.A2, U2.74 (BLD)
dstC: D30.2 (A), K11.22, K30.A2, U2.75 (CLD)
dstD: D36.2 (A), K11.24, K36.A2, U2.20 (DLD)
dstINC: K54.14, K54.24, U2.76 (INCLD)
dstJ1: K46.14, U2.16 (J1LD)
dstJ2: K46.24, U2.17 (J2LD)
dstM: U2.15 (MHiLoLD)
dstM1: D26.2 (A), K13.12, K26.A2, K46.12, U2.13 (MHiLD)
dstM2: D32.2 (A), K13.14, K32.A2, K46.22, U2.14 (MLoLD)
dstPC: K50.24, K56.14, K56.24, K62.14, U2.31 (PCLD)
dstX: D28.2 (A), K13.22, K28.A2, U2.10 (XLD)
dstXY: K50.22, K57.14, U2.12 (XYLD)
dstY: D34.2 (A), K13.24, K34.A2, U2.11 (YLD)
srcA: D17.2 (A), K8.12, K17.A2, U2.23 (ASL)
srcB: D23.2 (A), K8.14, K23.A2, U2.72 (BSL)
srcC: D29.2 (A), K8.22, K29.A2, U2.73 (CSL)
srcD: D35.2 (A), K8.24, K35.A2, U2.24 (DSL)
srcINC: D59.1 (K), U2.27 (IncSL)
srcJ: K51.22, K63.14, U2.18 (JSL)
srcM: K51.12, U2.22 (MemSL)
srcM1: D25.2 (A), K12.12, K25.A2, U2.70 (MHiSL)
srcM2: D31.2 (A), K12.14, K31.A2, U2.71 (MLoSL)
srcPC: D52.1 (K), D55.1 (K), U2.26 (PCSL)
srcX: D27.2 (A), K12.22, K27.A2, U2.28 (XSL)
srcXY: K51.14, U2.30 (XYSL)
srcY: D33.2 (A), K12.24, K33.A2, U2.29 (YSL)

Notes on the sheet:
100????? : --> 101????? : -->
0??????? : --> 1??????? : -->
100100rr : LOAD 100110rr : STORE 10100dss : MOV16 10101xxx : ???
Zu ENABLE
00dddsss : MOV8 01rddddd : SETAB 10?????? : --> 11dscznx : GOTO
CLEAR
MOV8
Zu LOAD
MOV16
1000rfff : ALU 1001???? : --> 1010???? : --> 1011000x : INCXY
GOTO
DECODER
Timing Input

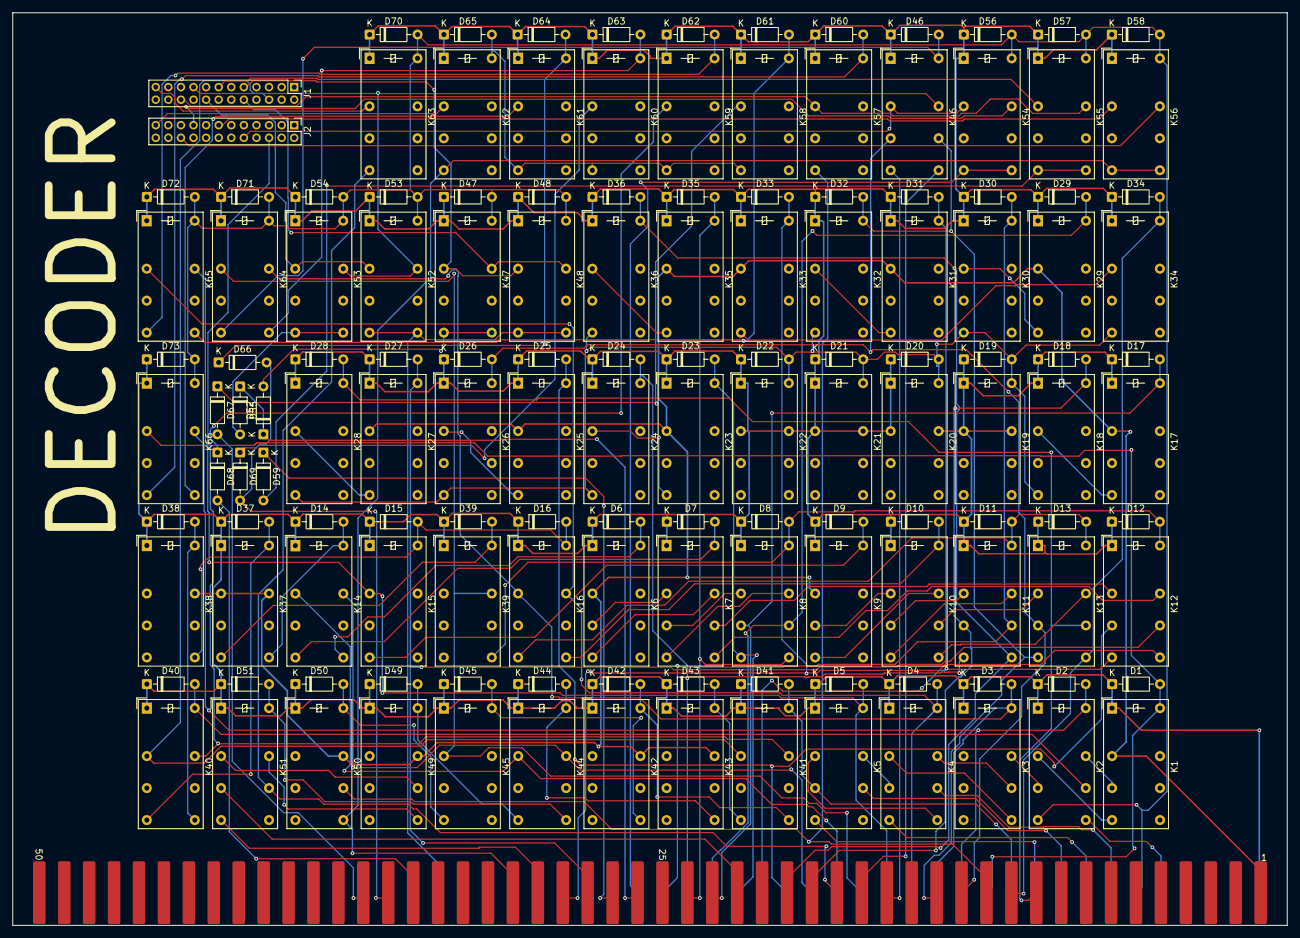
[picture p47: board Decoder.kicad_pcb from above]

Board: 2 copper layers, 202.5 x 145.0 mm, 142 parts (0 on the bottom side), 124 nets.
