Syntaxer04/RC1Computer/Version 0.1/Fulladder/Fulladder.kicad_pcb

## KiCad design Version 0.1/Fulladder/Fulladder.kicad_pcb (2025-06-25, an earlier design)

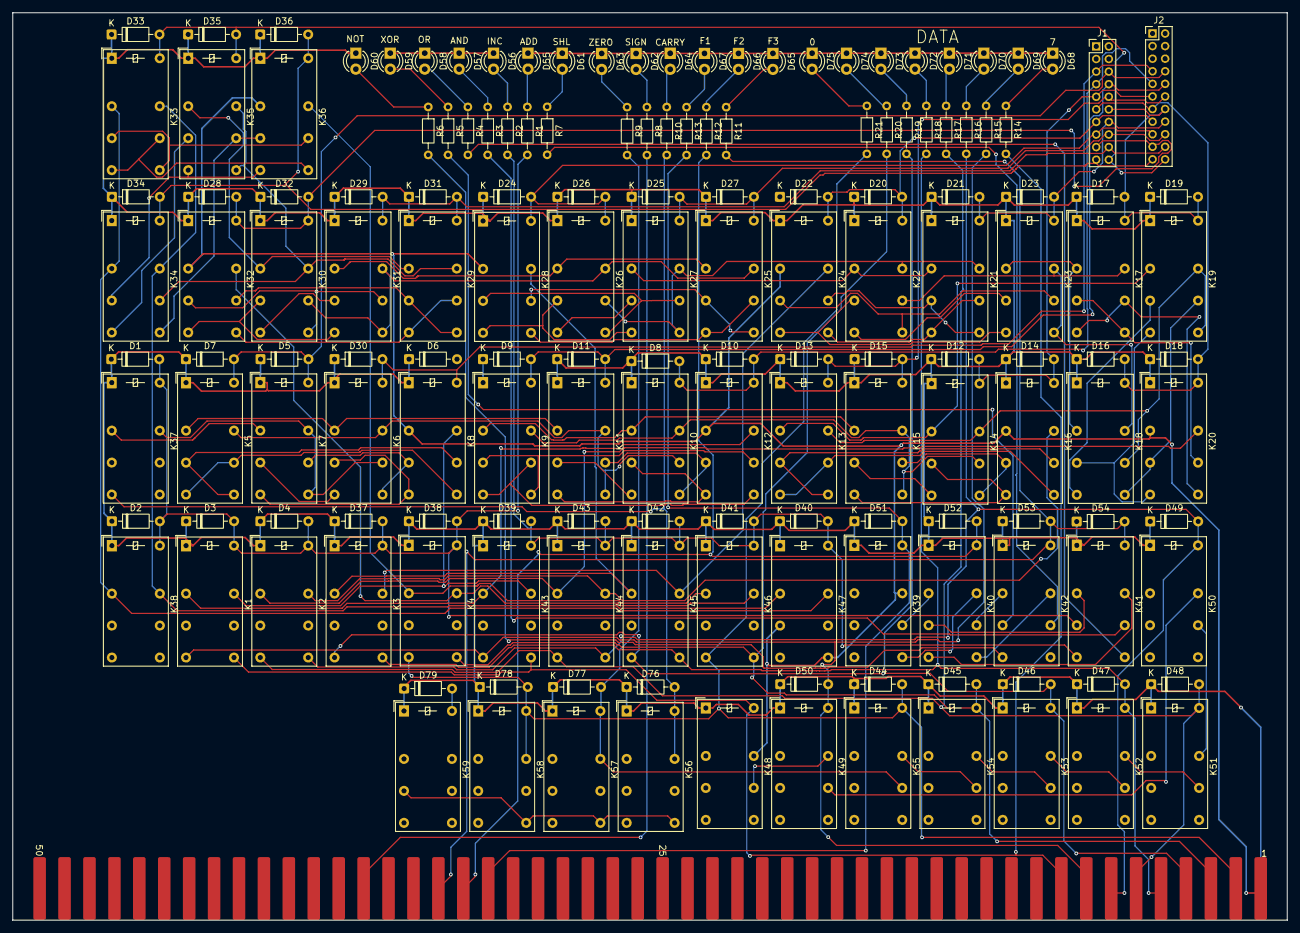
[picture p48: board Fulladder.kicad_pcb from above]

Board: 2 copper layers, 202.5 x 144.2 mm, 162 parts (0 on the bottom side), 142 nets.

Parts:
D1, D2, D3, D4, D5, D6, D7, D8, D9, D10, D11, D12, D13, D14, D15, D16, D17, D18, D19, D20, D21, D22, D23, D24, D25, D26, D27, D28, D29, D30, D31, D32, D33, D34, D35, D36, D37, D38, D39, D40, D41, D42, D43, D44, D45, D46, D47, D48, D49, D50, D51, D52, D53, D54, D76, D77, D78, D79: 1N914; D_DO-35_SOD27_P7.62mm_Horizontal
D55, D56, D57, D58, D59, D60, D61, D62, D63, D64, D65, D66, D67, D68, D69, D70, D71, D72, D73, D74, D75: LED; LED_D3.0mm
J1: Conn_02x10_Odd_Even; PinHeader_2x10_P2.00mm_Vertical
J2: Conn_02x11_Odd_Even; PinHeader_2x11_P2.00mm_Vertical
K1, K2, K3, K4, K5, K6, K7, K8, K9, K10, K11, K12, K13, K14, K15, K16, K17, K18, K19, K20, K21, K22, K23, K24, K25, K26, K27, K28, K29, K30, K31, K32, K33, K34, K35, K36, K37, K38, K39, K40, K41, K42, K43, K44, K45, K46, K47, K48, K49, K50, K51, K52, K53, K54, K55, K56, K57, K58, K59: HK19F-DCxxV-SHC; Relay_DPDT_Finder_30.22
R1, R2, R3, R4, R5, R6, R7, R8, R9, R10, R11, R12, R13, R14, R15, R16, R17, R18, R19, R20, R21: R; R_Axial_DIN0204_L3.6mm_D1.6mm_P7.62mm_Horizontal
U1: Conn_RC_Male_100

Connections:
CCLD: D79.2 (A), K59.A2
Carry: D76.2 (A), K37.14, K56.21, K56.A2, R10.2
GND: D1.1 (K), D2.1 (K), D3.1 (K), D4.1 (K), D5.1 (K), D6.1 (K), D7.1 (K), D8.1 (K), D10.1 (K), D11.1 (K), D12.1 (K), D13.1 (K), D14.1 (K), D15.1 (K), D16.1 (K), D17.1 (K), D18.1 (K), D19.1 (K), D20.1 (K), D21.1 (K), D23.1 (K), D24.1 (K), D25.1 (K), D26.1 (K), D27.1 (K), D28.1 (K), D29.1 (K), D30.1 (K), D31.1 (K), D32.1 (K), D33.1 (K), D34.1 (K), D35.1 (K), D36.1 (K), D37.1 (K), D38.1 (K), D39.1 (K), D40.1 (K), D41.1 (K), D42.1 (K), D43.1 (K), D44.1 (K), D45.1 (K), D46.1 (K), D47.1 (K), D48.1 (K), D49.1 (K), D50.1 (K), D51.1 (K), D52.1 (K), D53.1 (K), D54.1 (K), D55.1 (K), D56.1 (K), D57.1 (K), D58.1 (K), D59.1 (K), D60.1 (K), D61.1 (K), D62.1 (K), D63.1 (K), D64.1 (K), D65.1 (K), D66.1 (K), D67.1 (K), D68.1 (K), D69.1 (K), D70.1 (K), D71.1 (K), D72.1 (K), D73.1 (K), D74.1 (K), D75.1 (K), D76.1 (K), D77.1 (K), D78.1 (K), D79.1 (K), K1.A1, K2.A1, K3.A1, K4.A1, K5.A1, K6.A1, K7.A1, K8.A1, K10.A1, K11.A1, K12.A1, K13.A1, K14.A1, K15.A1, K16.A1, K17.A1, K18.A1, K19.A1, K20.A1, K21.A1, K22.A1, K23.A1, K24.A1, K25.A1, K26.A1, K27.A1, K28.A1, K29.A1, K30.A1, K31.A1, K32.A1, K33.A1, K34.A1, K35.A1, K36.A1, K37.A1, K38.A1, K39.A1, K40.A1, K41.A1, K42.A1, K43.A1, K44.A1, K45.A1, K46.A1, K47.A1, K48.A1, K49.A1, K50.A1, K51.A1, K52.A1, K53.A1, K54.A1, K55.A1, K56.A1, K57.A1, K58.A1, K59.A1, U1.51 (GND)
unnamed: D1.2 (A), D2.2 (A), D3.2 (A), D4.2 (A), D37.2 (A), D38.2 (A), K1.A2, K2.A2, K3.A2, K4.A2, K37.A2, K38.A2, K41.12, R1.2
unnamed: D5.2 (A), D7.2 (A), J1.6, J2.8, K5.A2, K7.A2
unnamed: D9.1 (K), K9.A1
unnamed: D8.2 (A), D10.2 (A), J1.7, J2.9, K10.A2, K12.A2
unnamed: D9.2 (A), D11.2 (A), J1.8, J2.10, K9.A2, K11.A2
unnamed: D12.2 (A), D14.2 (A), J1.9, J2.11, K14.A2, K16.A2
unnamed: D13.2 (A), D15.2 (A), J1.10, J2.12, K13.A2, K15.A2
unnamed: D16.2 (A), D18.2 (A), J1.11, J2.13, K18.A2, K20.A2
unnamed: D17.2 (A), D19.2 (A), J1.12, J2.14, K17.A2, K19.A2
unnamed: D20.2 (A), D22.2 (A), J1.13, J2.15, K22.A2, K24.A2
unnamed: D21.2 (A), D23.2 (A), J1.14, J2.16, K21.A2, K23.A2
unnamed: D24.2 (A), D26.2 (A), J1.15, J2.17, K26.A2, K28.A2
unnamed: D25.2 (A), D27.2 (A), J1.16, J2.18, K25.A2, K27.A2
unnamed: D28.2 (A), D32.2 (A), J1.17, J2.19, K30.A2, K32.A2
unnamed: D29.2 (A), D31.2 (A), J1.18, J2.20, K29.A2, K31.A2
unnamed: D30.2 (A), J1.5, J2.7, K6.A2, K8.A2
unnamed: D33.2 (A), D35.2 (A), J1.20, J2.22, K33.A2, K35.A2
unnamed: D34.2 (A), D36.2 (A), J1.19, J2.21, K34.A2, K36.A2
unnamed: D39.2 (A), D40.2 (A), D41.2 (A), D42.2 (A), D43.2 (A), K41.14, K43.A2, K44.A2, K45.A2, K46.A2, K47.A2, R2.2
unnamed: D45.2 (A), K4.24, K46.24, K54.A2, R20.2, U1.3 (D1)
unnamed: D46.2 (A), K3.14, K45.14, K53.A2, R19.2, U1.4 (D2)
unnamed: D47.2 (A), K3.24, K45.24, K52.A2, R18.2, U1.5 (D3)
unnamed: D48.2 (A), K2.14, K44.14, K51.A2, R17.2, U1.6 (D4)
unnamed: D49.2 (A), K2.24, K44.24, K50.A2, R16.2, U1.7 (D5)
unnamed: D50.2 (A), K1.14, K43.14, K49.A2, R15.2, U1.8 (D6)
unnamed: D51.2 (A), K39.A2, R13.2, U1.32 (F1)
unnamed: D52.2 (A), K40.A2, R12.2, U1.33 (F2)
unnamed: D53.2 (A), D54.2 (A), K41.A2, K42.A2, R11.2, U1.34 (F3)
unnamed: D55.2 (A), R1.1
unnamed: D56.2 (A), R2.1
unnamed: D57.2 (A), R3.1
unnamed: D58.2 (A), R4.1
unnamed: D59.2 (A), R5.1
unnamed: D60.2 (A), R6.1
unnamed: D61.2 (A), R7.1
unnamed: D62.2 (A), R8.1
unnamed: D63.2 (A), R9.1
unnamed: D64.2 (A), R10.1
unnamed: D65.2 (A), R11.1
unnamed: D66.2 (A), R12.1
unnamed: D67.2 (A), R13.1
unnamed: D68.2 (A), R14.1
unnamed: D69.2 (A), R15.1
unnamed: D70.2 (A), R16.1
unnamed: D71.2 (A), R17.1
unnamed: D72.2 (A), R18.1
unnamed: D73.2 (A), R19.1
unnamed: D74.2 (A), R20.1
unnamed: D75.2 (A), R21.1
unnamed: K42.14, R6.2
unnamed: K42.12, R5.2
unnamed: K42.22, R7.2
unnamed: K41.24, R4.2
unnamed: K41.22, R3.2
unnamed: K1.11, K12.21, K43.11
unnamed: K1.21, K8.21, K43.21
unnamed: K2.11, K20.21, K44.11
unnamed: K5.12, K5.24, K8.22
unnamed: K5.14, K5.22, K8.24
unnamed: K6.12, K7.14, K8.14
unnamed: K6.14, K7.12
unnamed: K6.24, K7.22, K8.12
unnamed: K9.11, K10.11, K15.11
unnamed: K10.12, K11.14, K12.14
unnamed: K10.14, K11.12
unnamed: K9.21, K10.21, K14.22, K15.21, K15.24
unnamed: K5.21, K6.21, K10.22, K11.21, K11.24
unnamed: K10.24, K11.22, K12.12
unnamed: K5.11, K6.11, K11.11
unnamed: K9.12, K9.24, K12.22
unnamed: K9.14, K9.22, K12.24
unnamed: K13.11, K14.11, K19.11
unnamed: K13.12, K13.24, K16.22
unnamed: K13.14, K13.22, K16.24
unnamed: K13.21, K14.21, K18.22, K19.21, K19.24
unnamed: K14.12, K15.14, K16.14
unnamed: K14.14, K15.12
unnamed: K14.24, K15.22, K16.12
unnamed: K2.21, K16.21, K44.21
unnamed: K17.11, K18.11, K23.11
unnamed: K17.12, K17.24, K20.22
unnamed: K17.14, K17.22, K20.24
unnamed: K17.21, K18.21, K22.22, K23.21, K23.24
unnamed: K18.12, K19.14, K20.14
unnamed: K18.14, K19.12
unnamed: K18.24, K19.22, K20.12
unnamed: K21.11, K22.11, K27.11
unnamed: K21.12, K21.24, K24.22
unnamed: K21.14, K21.22, K24.24
unnamed: K21.21, K22.21, K26.22, K27.21, K27.24
unnamed: K22.12, K23.14, K24.14
unnamed: K22.14, K23.12
unnamed: K22.24, K23.22, K24.12
unnamed: K3.21, K24.21, K45.21
unnamed: K25.11, K26.11, K31.11
unnamed: K25.12, K25.24, K28.22
unnamed: K25.14, K25.22, K28.24
unnamed: K25.21, K26.21, K30.22, K31.21, K31.24
unnamed: K26.12, K27.14, K28.14
unnamed: K26.14, K27.12
unnamed: K26.24, K27.22, K28.12
unnamed: K3.11, K28.21, K45.11
unnamed: K29.11, K30.11, K35.11
unnamed: K29.12, K29.24, K32.22
unnamed: K29.14, K29.22, K32.24
unnamed: K29.21, K30.21, K34.22, K35.21, K35.24
unnamed: K30.12, K31.14, K32.14
unnamed: K30.14, K31.12
unnamed: K30.24, K31.22, K32.12
unnamed: K4.21, K32.21, K46.21
unnamed: K33.11, K34.11, K38.11, K47.21
unnamed: K33.12, K33.24, K36.22
unnamed: K33.14, K33.22, K36.24
unnamed: K33.21, K34.21, K38.21, K47.11
unnamed: K34.12, K35.14, K36.14
unnamed: K34.14, K35.12
unnamed: K34.24, K35.22, K36.12
unnamed: K4.11, K36.21, K46.11
unnamed: K7.11, K37.11
unnamed: K6.22, K7.21, K7.24, K37.21
unnamed: K39.22, K40.11
unnamed: K39.24, K40.21
unnamed: K40.12, K41.11
unnamed: K40.14, K41.21
unnamed: K40.22, K42.11
unnamed: K40.24, K42.21
unnamed: K48.22, K49.21
unnamed: K49.22, K50.21
unnamed: K50.22, K51.21
unnamed: K51.22, K52.21
unnamed: K52.22, K53.21
unnamed: K53.22, K54.21
unnamed: K54.22, K55.21
unnamed: K56.24, K57.24, K58.24, K59.12
unnamed: K8.11, K12.11, K16.11, K20.11, K24.11, K28.11, K32.11, K36.11, K39.21, K47.12, K47.24, K48.21, U1.1 (5_Volt)
unnamed: K1.24, K43.24, K48.A2, R14.2, U1.9 (D7)
unnamed: R8.2, U1.37 (SIGN)
Sign: D44.2 (A), D78.2 (A), K4.14, K46.14, K55.A2, K58.21, K58.A2, R21.2, U1.2 (D0)
Zero: D77.2 (A), K55.22, K57.21, K57.A2, R9.2
