Syntaxer04/RC1Computer/Version 0.1/Front Panel/Front Panel.kicad_pcb

## KiCad design Version 0.1/Front Panel/Front Panel.kicad_pcb (2025-06-25, an earlier design)

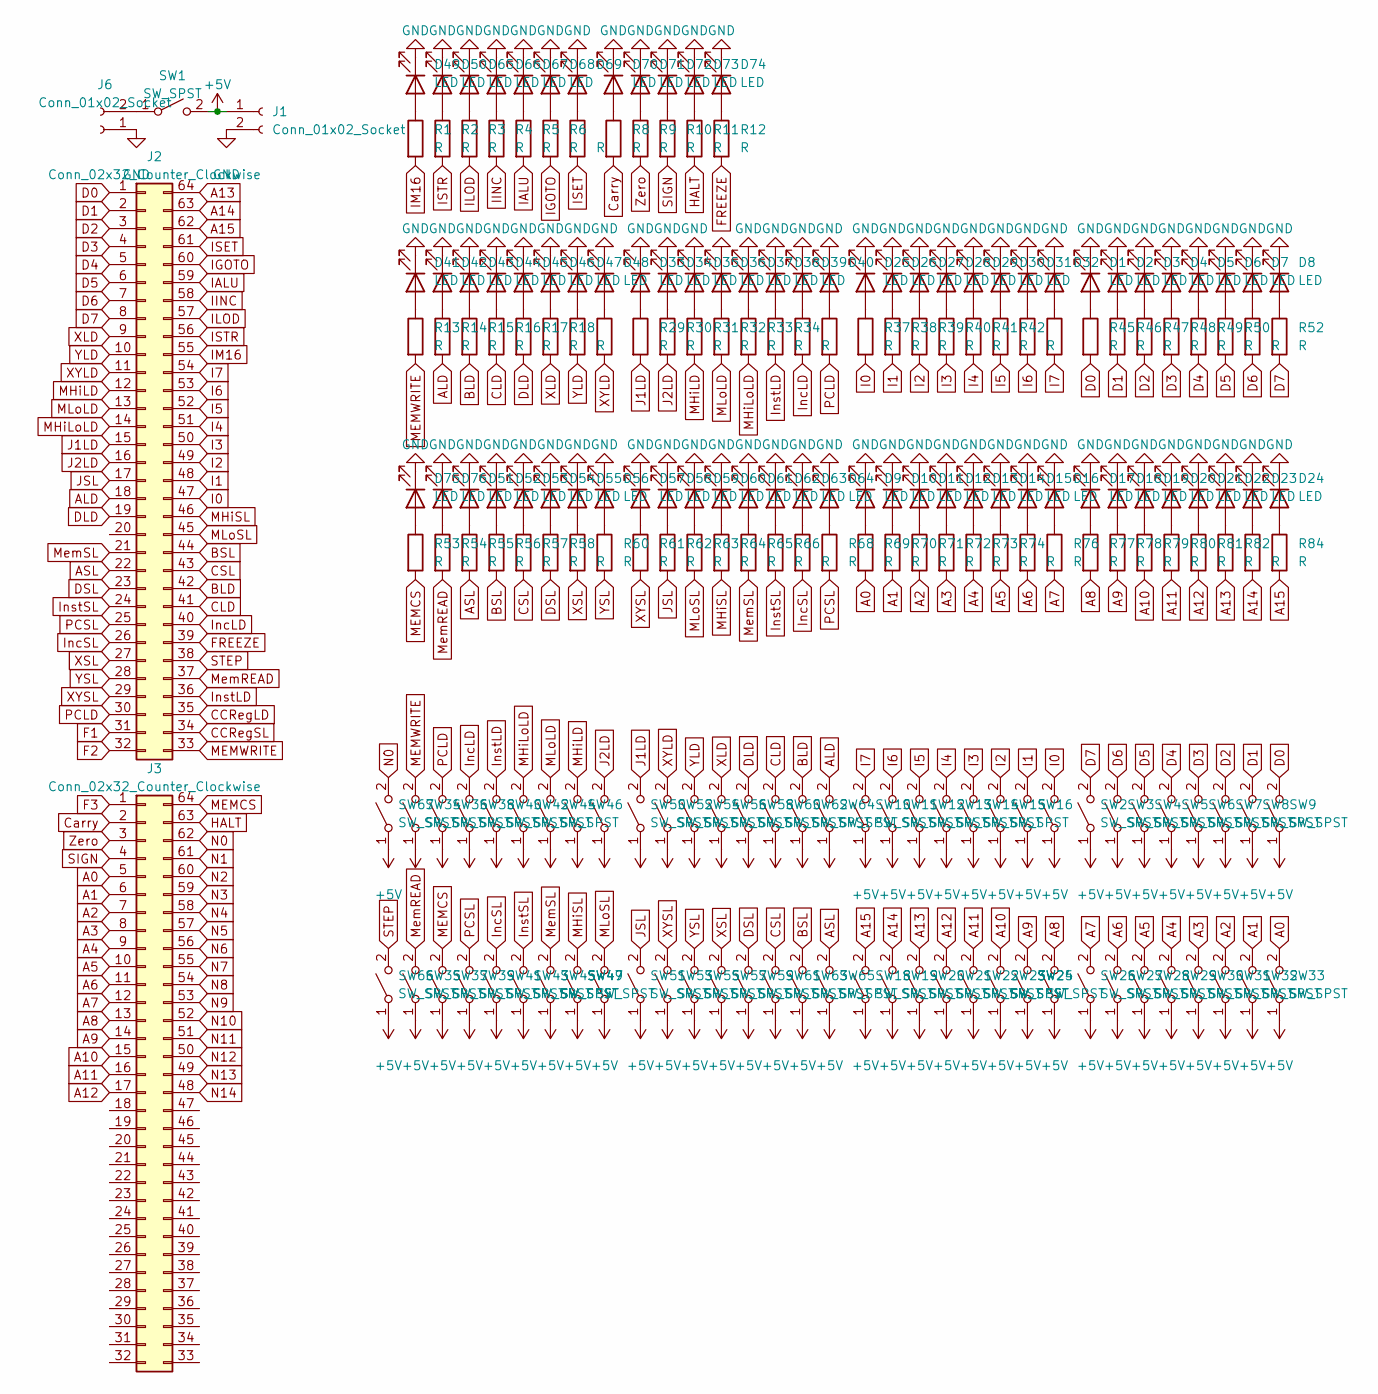
[picture p49: schematic Front Panel.kicad_sch]

Parts:
D1, D2, D3, D4, D5, D6, D7, D8, D9, D10, D11, D12, D13, D14, D15, D16, D17, D18, D19, D20, D21, D22, D23, D24, D25, D26, D27, D28, D29, D30, D31, D32, D33, D34, D35, D36, D37, D38, D39, D40, D41, D42, D43, D44, D45, D46, D47, D48, D49, D50, D51, D52, D53, D54, D55, D56, D57, D58, D59, D60, D61, D62, D63, D64, D65, D66, D67, D68, D69, D70, D71, D72, D73, D74, D75, D76: LED; LED_D8.0mm
J1, J6: Conn_01x02_Socket; JWT_A3963_1x02_P3.96mm_Vertical
J2, J3: Conn_02x32_Counter_Clockwise; IDC-Header_2x32_P2.54mm_Vertical
R1, R2, R3, R4, R5, R6, R7, R8, R9, R10, R11, R12, R13, R14, R15, R16, R17, R18, R19, R20, R29, R30, R31, R32, R33, R34, R35, R36, R37, R38, R39, R40, R41, R42, R43, R44, R45, R46, R47, R48, R49, R50, R51, R52, R53, R54, R55, R56, R57, R58, R59, R60, R61, R62, R63, R64, R65, R66, R67, R68, R69, R70, R71, R72, R73, R74, R75, R76, R77, R78, R79, R80, R81, R82, R83, R84: R; R_Axial_DIN0204_L3.6mm_D1.6mm_P2.54mm_Vertical
SW1, SW2, SW3, SW4, SW5, SW6, SW7, SW8, SW9, SW10, SW11, SW12, SW13, SW14, SW15, SW16, SW17, SW18, SW19, SW20, SW21, SW22, SW23, SW24, SW25, SW26, SW27, SW28, SW29, SW30, SW31, SW32, SW33, SW34, SW35, SW36, SW37, SW38, SW39, SW40, SW41, SW42, SW43, SW44, SW45, SW46, SW47, SW48, SW49, SW50, SW51, SW52, SW53, SW54, SW55, SW56, SW57, SW58, SW59, SW60, SW61, SW62, SW63, SW64, SW65, SW66, SW67: SW_SPST; Switches

Connections:
+5V: J1.1, SW1.2 (B), SW2.1 (A), SW3.1 (A), SW4.1 (A), SW5.1 (A), SW6.1 (A), SW7.1 (A), SW8.1 (A), SW9.1 (A), SW10.1 (A), SW11.1 (A), SW12.1 (A), SW13.1 (A), SW14.1 (A), SW15.1 (A), SW16.1 (A), SW17.1 (A), SW18.1 (A), SW19.1 (A), SW20.1 (A), SW21.1 (A), SW22.1 (A), SW23.1 (A), SW24.1 (A), SW25.1 (A), SW26.1 (A), SW27.1 (A), SW28.1 (A), SW29.1 (A), SW30.1 (A), SW31.1 (A), SW32.1 (A), SW33.1 (A), SW34.1 (A), SW35.1 (A), SW36.1 (A), SW37.1 (A), SW38.1 (A), SW39.1 (A), SW40.1 (A), SW41.1 (A), SW42.1 (A), SW43.1 (A), SW44.1 (A), SW45.1 (A), SW46.1 (A), SW47.1 (A), SW48.1 (A), SW49.1 (A), SW50.1 (A), SW51.1 (A), SW52.1 (A), SW53.1 (A), SW54.1 (A), SW55.1 (A), SW56.1 (A), SW57.1 (A), SW58.1 (A), SW59.1 (A), SW60.1 (A), SW61.1 (A), SW62.1 (A), SW63.1 (A), SW64.1 (A), SW65.1 (A), SW66.1 (A), SW67.1 (A)
A0: J3.5, R69.2, SW33.2 (B)
A1: J3.6, R70.2, SW32.2 (B)
A2: J3.7, R71.2, SW31.2 (B)
A3: J3.8, R72.2, SW30.2 (B)
A4: J3.9, R73.2, SW29.2 (B)
A5: J3.10, R74.2, SW28.2 (B)
A6: J3.11, R75.2, SW27.2 (B)
A7: J3.12, R76.2, SW26.2 (B)
A8: J3.13, R77.2, SW25.2 (B)
A9: J3.14, R78.2, SW24.2 (B)
A10: J3.15, R79.2, SW23.2 (B)
A11: J3.16, R80.2, SW22.2 (B)
A12: J3.17, R81.2, SW21.2 (B)
A13: J2.64, R82.2, SW20.2 (B)
A14: J2.63, R83.2, SW19.2 (B)
A15: J2.62, R84.2, SW18.2 (B)
ALD: J2.18, R14.2, SW64.2 (B)
ASL: J2.22, R55.2, SW65.2 (B)
BLD: J2.42, R15.2, SW62.2 (B)
BSL: J2.44, R56.2, SW63.2 (B)
CCRegLD: J2.35
CCRegSL: J2.34
CLD: J2.41, R16.2, SW60.2 (B)
CSL: J2.43, R57.2, SW61.2 (B)
Carry: J3.2, R8.2
D0: J2.1, R45.2, SW9.2 (B)
D1: J2.2, R46.2, SW8.2 (B)
D2: J2.3, R47.2, SW7.2 (B)
D3: J2.4, R48.2, SW6.2 (B)
D4: J2.5, R49.2, SW5.2 (B)
D5: J2.6, R50.2, SW4.2 (B)
D6: J2.7, R51.2, SW3.2 (B)
D7: J2.8, R52.2, SW2.2 (B)
DLD: J2.19, R17.2, SW58.2 (B)
DSL: J2.23, R58.2, SW59.2 (B)
F1: J2.31
F2: J2.32
F3: J3.1
FREEZE: J2.39, R12.2
GND: D1.1 (K), D2.1 (K), D3.1 (K), D4.1 (K), D5.1 (K), D6.1 (K), D7.1 (K), D8.1 (K), D9.1 (K), D10.1 (K), D11.1 (K), D12.1 (K), D13.1 (K), D14.1 (K), D15.1 (K), D16.1 (K), D17.1 (K), D18.1 (K), D19.1 (K), D20.1 (K), D21.1 (K), D22.1 (K), D23.1 (K), D24.1 (K), D25.1 (K), D26.1 (K), D27.1 (K), D28.1 (K), D29.1 (K), D30.1 (K), D31.1 (K), D32.1 (K), D33.1 (K), D34.1 (K), D35.1 (K), D36.1 (K), D37.1 (K), D38.1 (K), D39.1 (K), D40.1 (K), D41.1 (K), D42.1 (K), D43.1 (K), D44.1 (K), D45.1 (K), D46.1 (K), D47.1 (K), D48.1 (K), D49.1 (K), D50.1 (K), D51.1 (K), D52.1 (K), D53.1 (K), D54.1 (K), D55.1 (K), D56.1 (K), D57.1 (K), D58.1 (K), D59.1 (K), D60.1 (K), D61.1 (K), D62.1 (K), D63.1 (K), D64.1 (K), D65.1 (K), D66.1 (K), D67.1 (K), D68.1 (K), D69.1 (K), D70.1 (K), D71.1 (K), D72.1 (K), D73.1 (K), D74.1 (K), D75.1 (K), D76.1 (K), J1.2, J6.1
HALT: J3.63, R11.2
I0: J2.47, R37.2, SW17.2 (B)
I1: J2.48, R38.2, SW16.2 (B)
I2: J2.49, R39.2, SW15.2 (B)
I3: J2.50, R40.2, SW14.2 (B)
I4: J2.51, R41.2, SW13.2 (B)
I5: J2.52, R42.2, SW12.2 (B)
I6: J2.53, R43.2, SW11.2 (B)
I7: J2.54, R44.2, SW10.2 (B)
IALU: J2.59, R5.2
IGOTO: J2.60, R6.2
IINC: J2.58, R4.2
ILOD: J2.57, R3.2
IM16: J2.55, R1.2
ISET: J2.61, R7.2
ISTR: J2.56, R2.2
IncLD: J2.40, R35.2, SW38.2 (B)
IncSL: J2.26, R67.2, SW41.2 (B)
InstLD: J2.36, R34.2, SW40.2 (B)
InstSL: J2.24, R66.2, SW43.2 (B)
J1LD: J2.15, R29.2, SW50.2 (B)
J2LD: J2.16, R30.2, SW48.2 (B)
JSL: J2.17, R62.2, SW51.2 (B)
MEMCS: J3.64, R53.2, SW37.2 (B)
MEMWRITE: J2.33, R13.2, SW34.2 (B)
MHiLD: J2.12, R31.2, SW46.2 (B)
MHiLoLD: J2.14, R33.2, SW42.2 (B)
MHiSL: J2.46, R64.2, SW47.2 (B)
MLoLD: J2.13, R32.2, SW44.2 (B)
MLoSL: J2.45, R63.2, SW49.2 (B)
MemREAD: J2.37, R54.2, SW35.2 (B)
MemSL: J2.21, R65.2, SW45.2 (B)
N0: J3.62, SW67.2 (B)
N1: J3.61
N2: J3.60
N3: J3.59
N4: J3.58
N5: J3.57
N6: J3.56
N7: J3.55
N8: J3.54
N9: J3.53
N10: J3.52
N11: J3.51
N12: J3.50
N13: J3.49
N14: J3.48
unnamed: D1.2 (A), R45.1
unnamed: D2.2 (A), R46.1
unnamed: D3.2 (A), R47.1
unnamed: D4.2 (A), R48.1
unnamed: D5.2 (A), R49.1
unnamed: D6.2 (A), R50.1
unnamed: D7.2 (A), R51.1
unnamed: D8.2 (A), R52.1
unnamed: D9.2 (A), R69.1
unnamed: D10.2 (A), R70.1
unnamed: D11.2 (A), R71.1
unnamed: D12.2 (A), R72.1
unnamed: D13.2 (A), R73.1
unnamed: D14.2 (A), R74.1
unnamed: D15.2 (A), R75.1
unnamed: D16.2 (A), R76.1
unnamed: D17.2 (A), R77.1
unnamed: D18.2 (A), R78.1
unnamed: D19.2 (A), R79.1
unnamed: D20.2 (A), R80.1
unnamed: D21.2 (A), R81.1
unnamed: D22.2 (A), R82.1
unnamed: D23.2 (A), R83.1
unnamed: D24.2 (A), R84.1
unnamed: D25.2 (A), R37.1
unnamed: D26.2 (A), R38.1
unnamed: D27.2 (A), R39.1
unnamed: D28.2 (A), R40.1
unnamed: D29.2 (A), R41.1
unnamed: D30.2 (A), R42.1
unnamed: D31.2 (A), R43.1
unnamed: D32.2 (A), R44.1
unnamed: D33.2 (A), R29.1
unnamed: D34.2 (A), R30.1
unnamed: D35.2 (A), R31.1
unnamed: D36.2 (A), R32.1
unnamed: D37.2 (A), R33.1
unnamed: D38.2 (A), R34.1
unnamed: D39.2 (A), R35.1
unnamed: D40.2 (A), R36.1
unnamed: D41.2 (A), R13.1
unnamed: D42.2 (A), R14.1
unnamed: D43.2 (A), R15.1
unnamed: D44.2 (A), R16.1
unnamed: D45.2 (A), R17.1
unnamed: D46.2 (A), R18.1
unnamed: D47.2 (A), R19.1
unnamed: D48.2 (A), R20.1
unnamed: D49.2 (A), R1.1
unnamed: D50.2 (A), R2.1
unnamed: D51.2 (A), R55.1
unnamed: D52.2 (A), R56.1
unnamed: D53.2 (A), R57.1
unnamed: D54.2 (A), R58.1
unnamed: D55.2 (A), R59.1
unnamed: D56.2 (A), R60.1
unnamed: D57.2 (A), R61.1
unnamed: D58.2 (A), R62.1
unnamed: D59.2 (A), R63.1
unnamed: D60.2 (A), R64.1
unnamed: D61.2 (A), R65.1
unnamed: D62.2 (A), R66.1
unnamed: D63.2 (A), R67.1
unnamed: D64.2 (A), R68.1
unnamed: D65.2 (A), R3.1
unnamed: D66.2 (A), R4.1
unnamed: D67.2 (A), R5.1
unnamed: D68.2 (A), R6.1
unnamed: D69.2 (A), R7.1
unnamed: D70.2 (A), R8.1
unnamed: D71.2 (A), R9.1
unnamed: D72.2 (A), R10.1
unnamed: D73.2 (A), R11.1
unnamed: D74.2 (A), R12.1
unnamed: D75.2 (A), R53.1
unnamed: D76.2 (A), R54.1
unnamed: J6.2, SW1.1 (A)
PCLD: J2.30, R36.2, SW36.2 (B)
PCSL: J2.25, R68.2, SW39.2 (B)
SIGN: J3.4, R10.2
STEP: J2.38, SW66.2 (B)
XLD: J2.9, R18.2, SW56.2 (B)
XSL: J2.27, R59.2, SW57.2 (B)
XYLD: J2.11, R20.2, SW52.2 (B)
XYSL: J2.29, R61.2, SW53.2 (B)
YLD: J2.10, R19.2, SW54.2 (B)
YSL: J2.28, R60.2, SW55.2 (B)
Zero: J3.3, R9.2

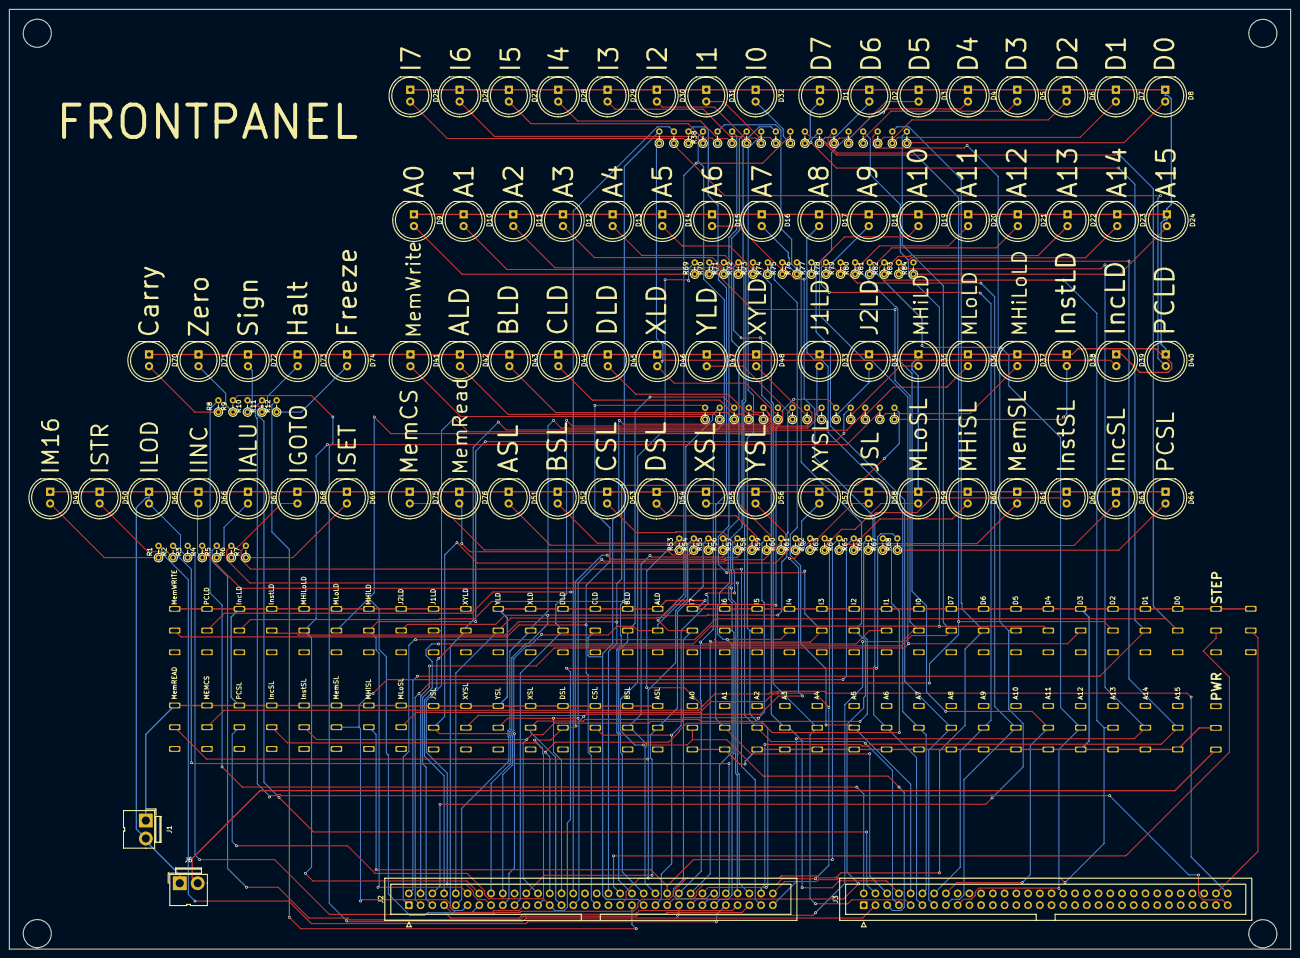
[picture p50: board Front Panel.kicad_pcb from above]

Board: 2 copper layers, 277.2 x 203.3 mm, 223 parts (0 on the bottom side), 157 nets.
