Syntaxer04/RC1Computer/Version 0.1/Incrementer/Incrementer.kicad_pcb

## KiCad design Version 0.1/Incrementer/Incrementer.kicad_pcb (2025-06-25, an earlier design)

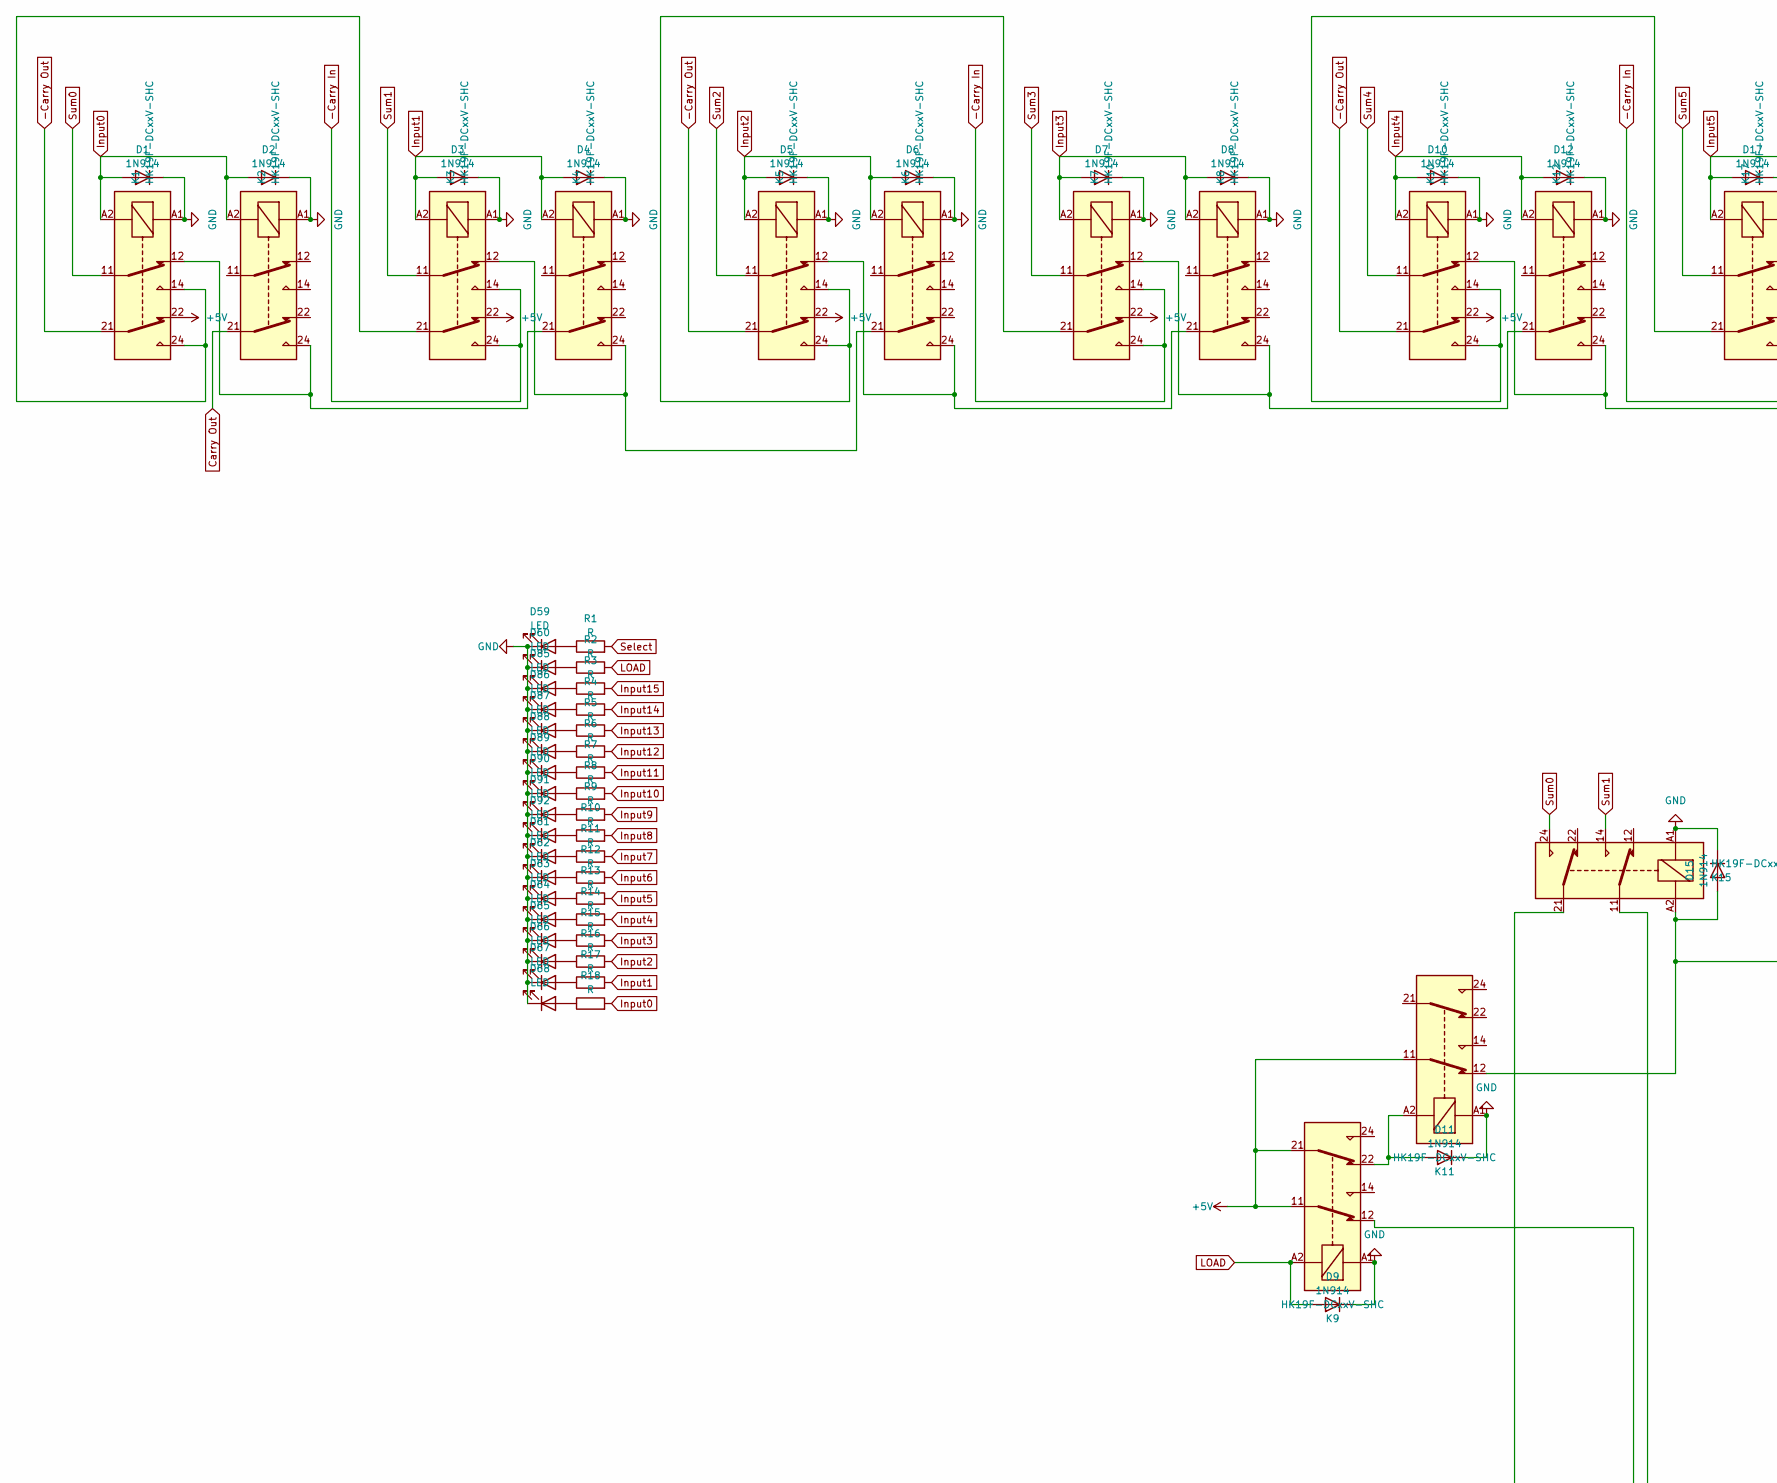
[picture p51: schematic Incrementer.kicad_sch, part in row 1, column 1]

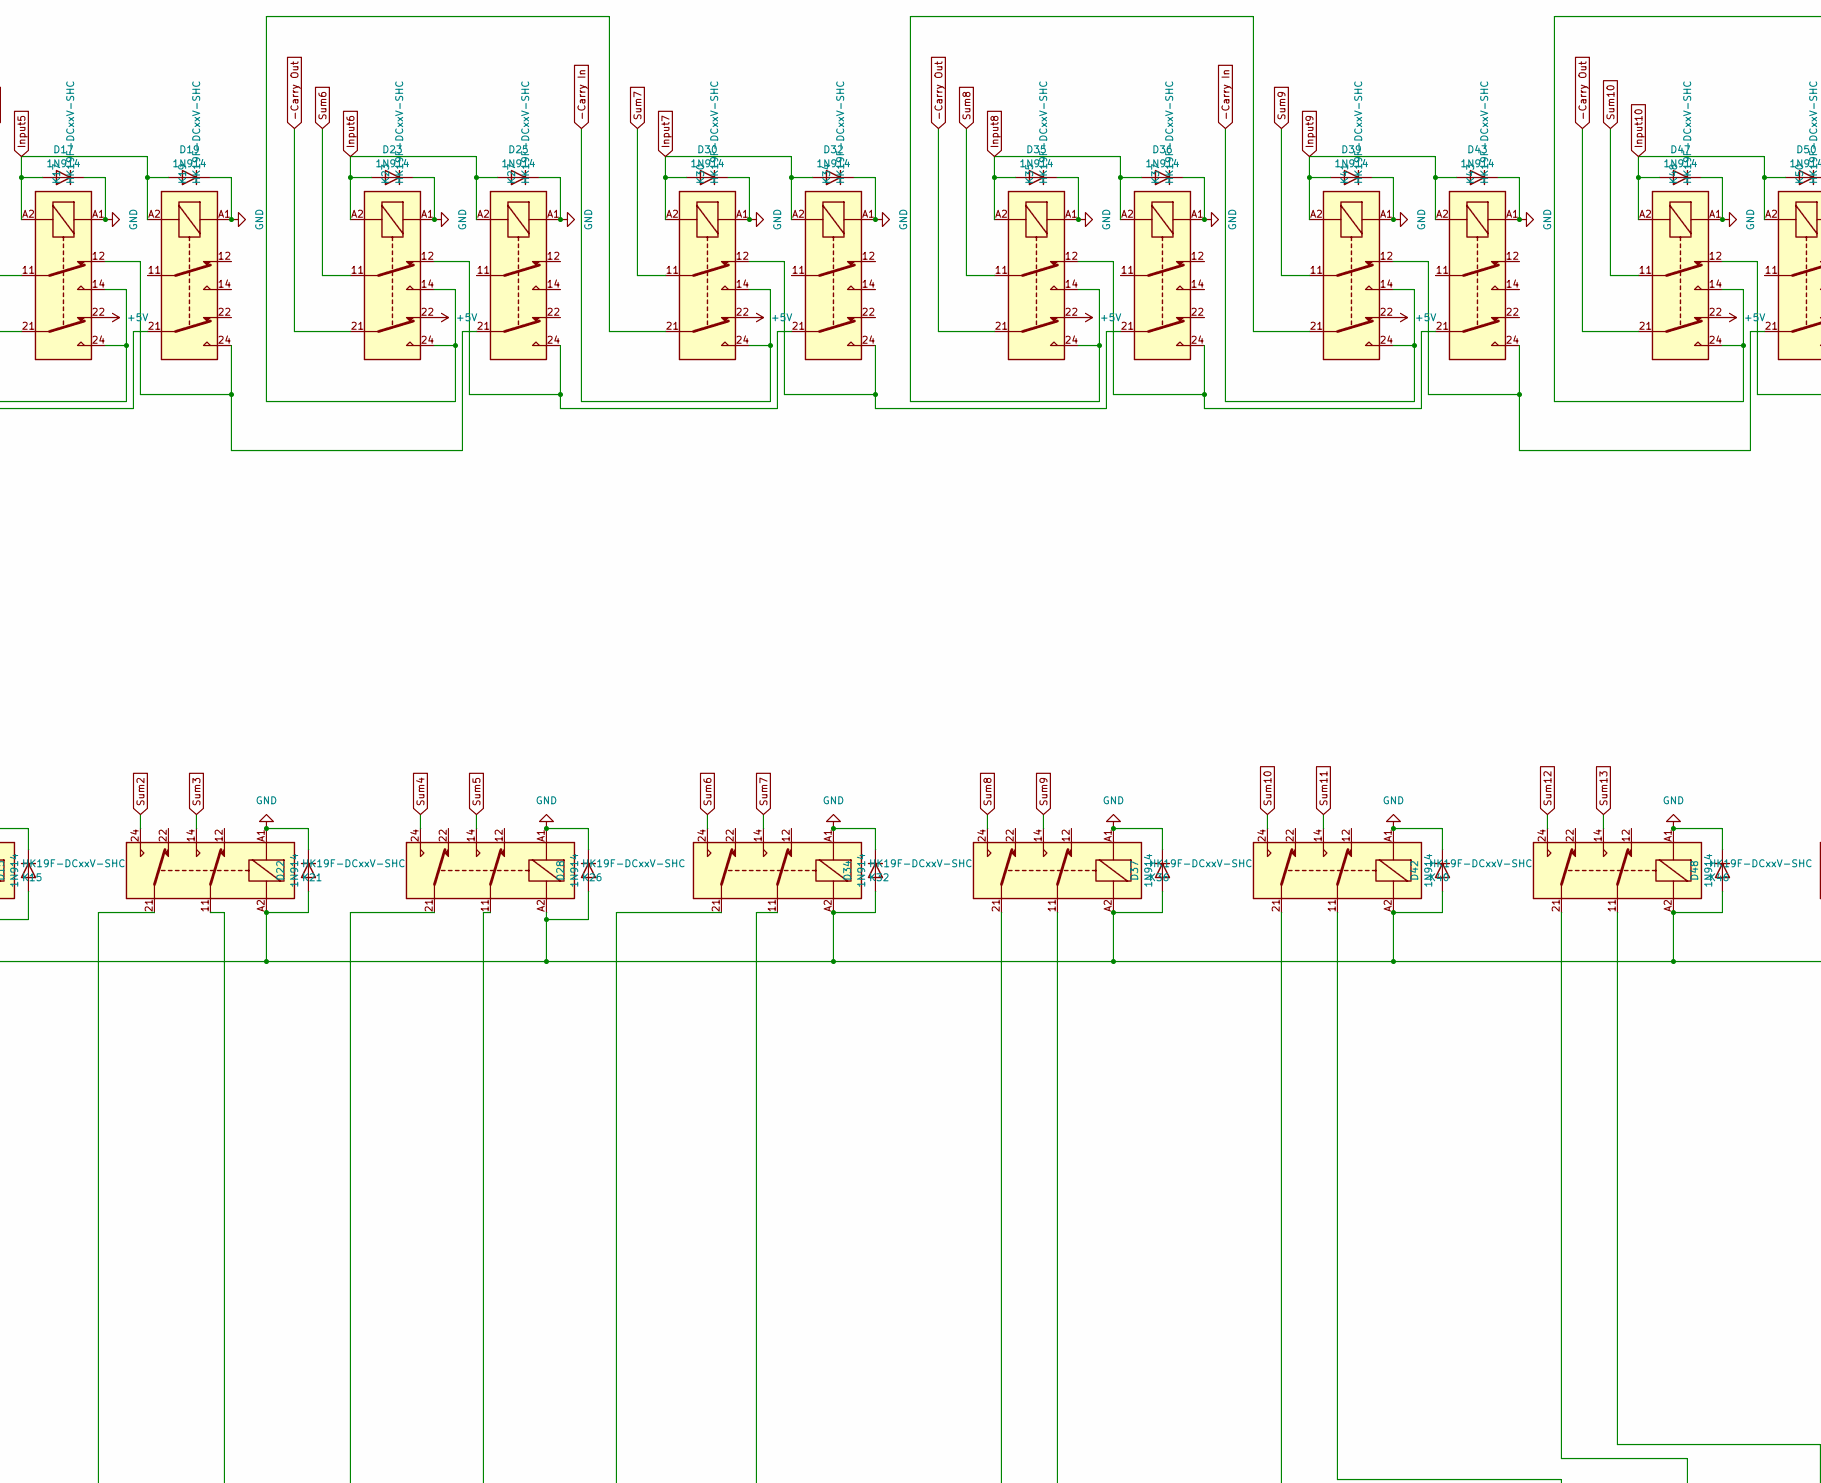
[picture p52: schematic Incrementer.kicad_sch, part in row 1, column 2]

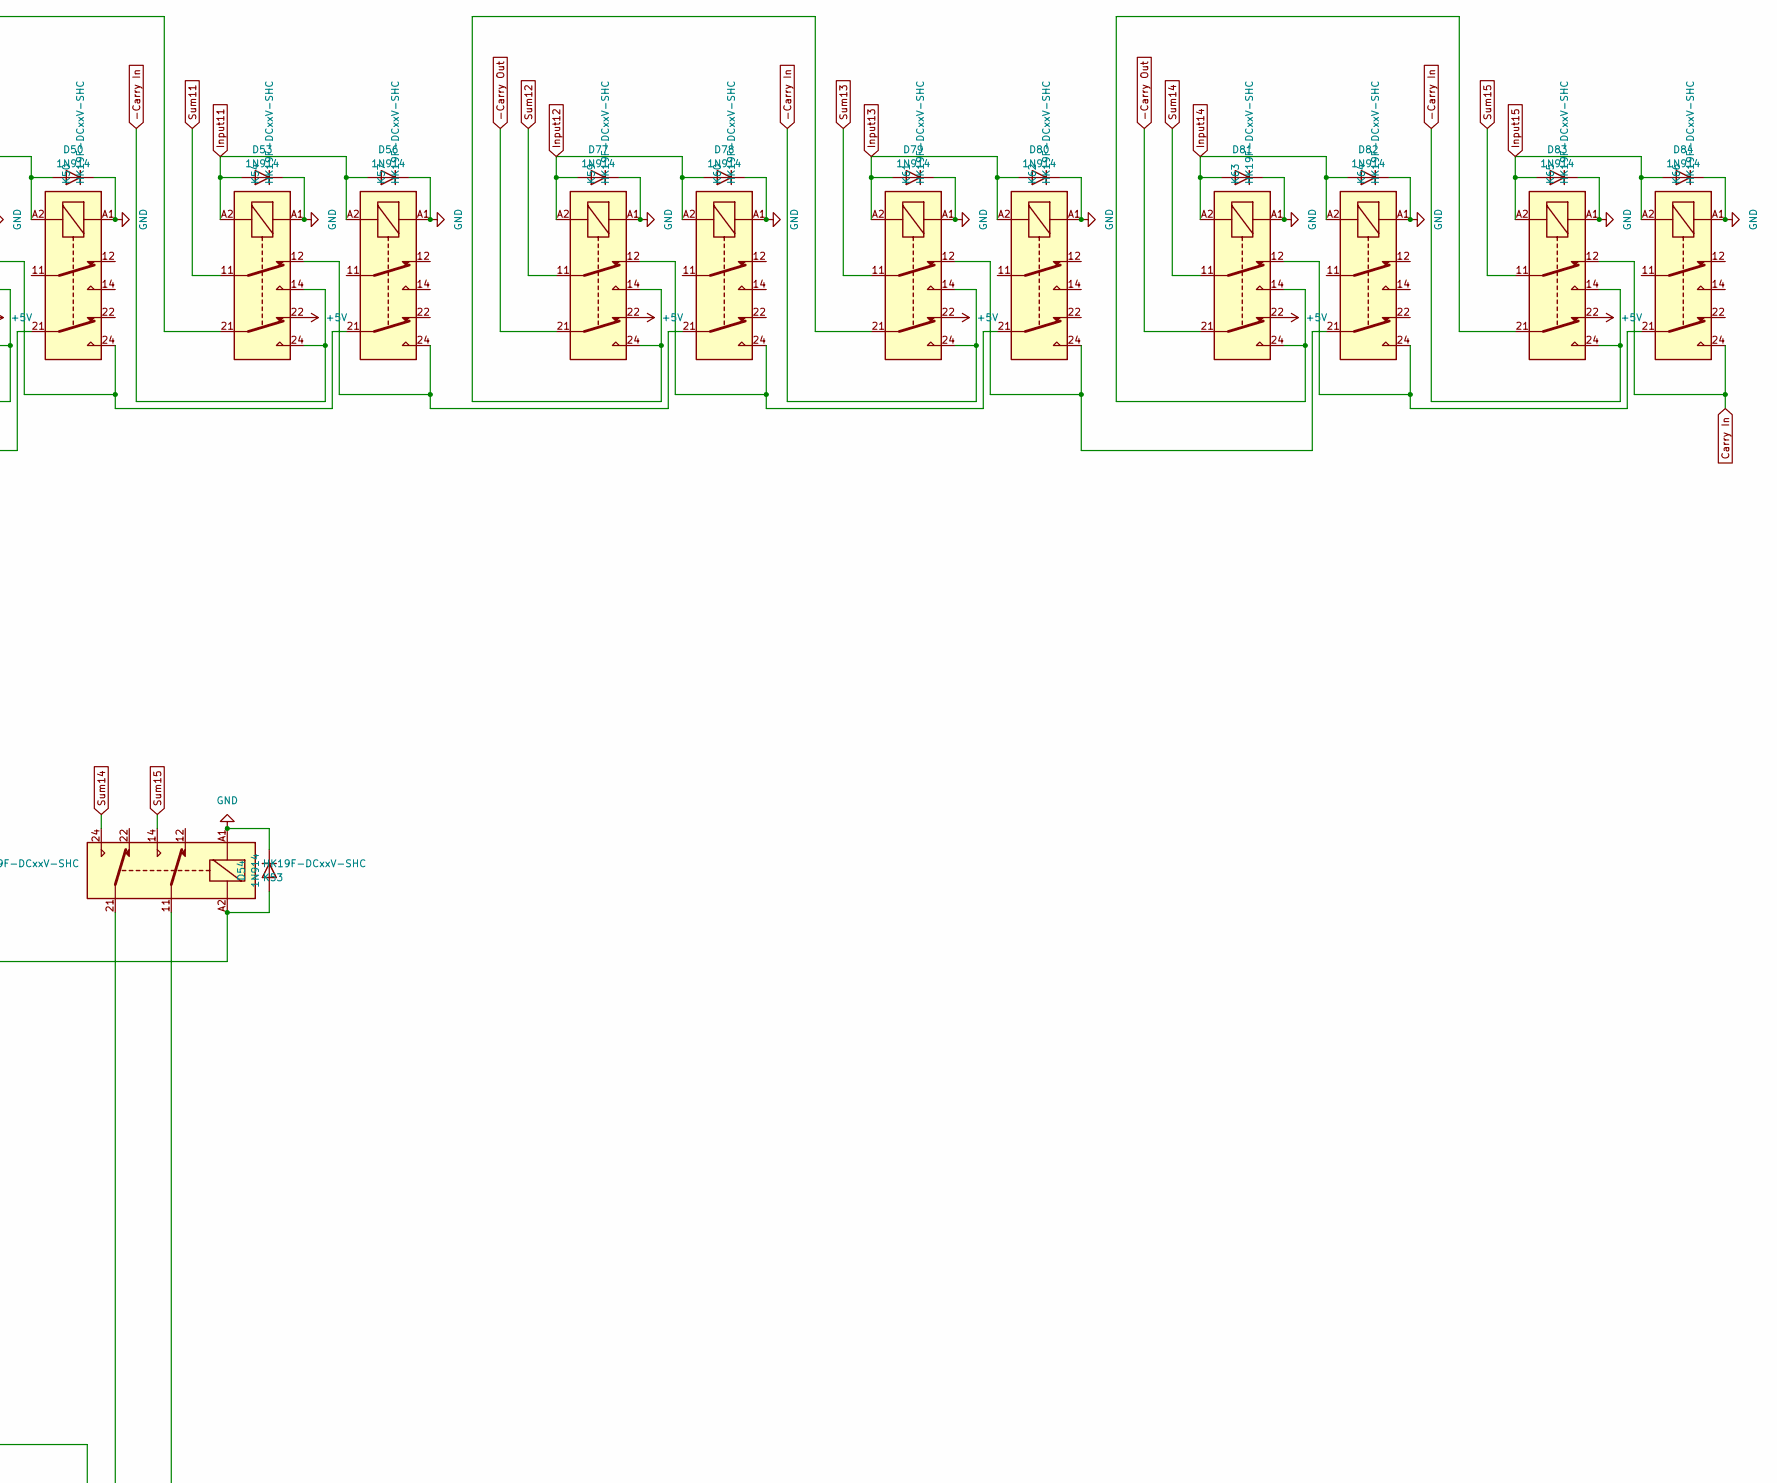
[picture p53: schematic Incrementer.kicad_sch, part in row 1, column 3]

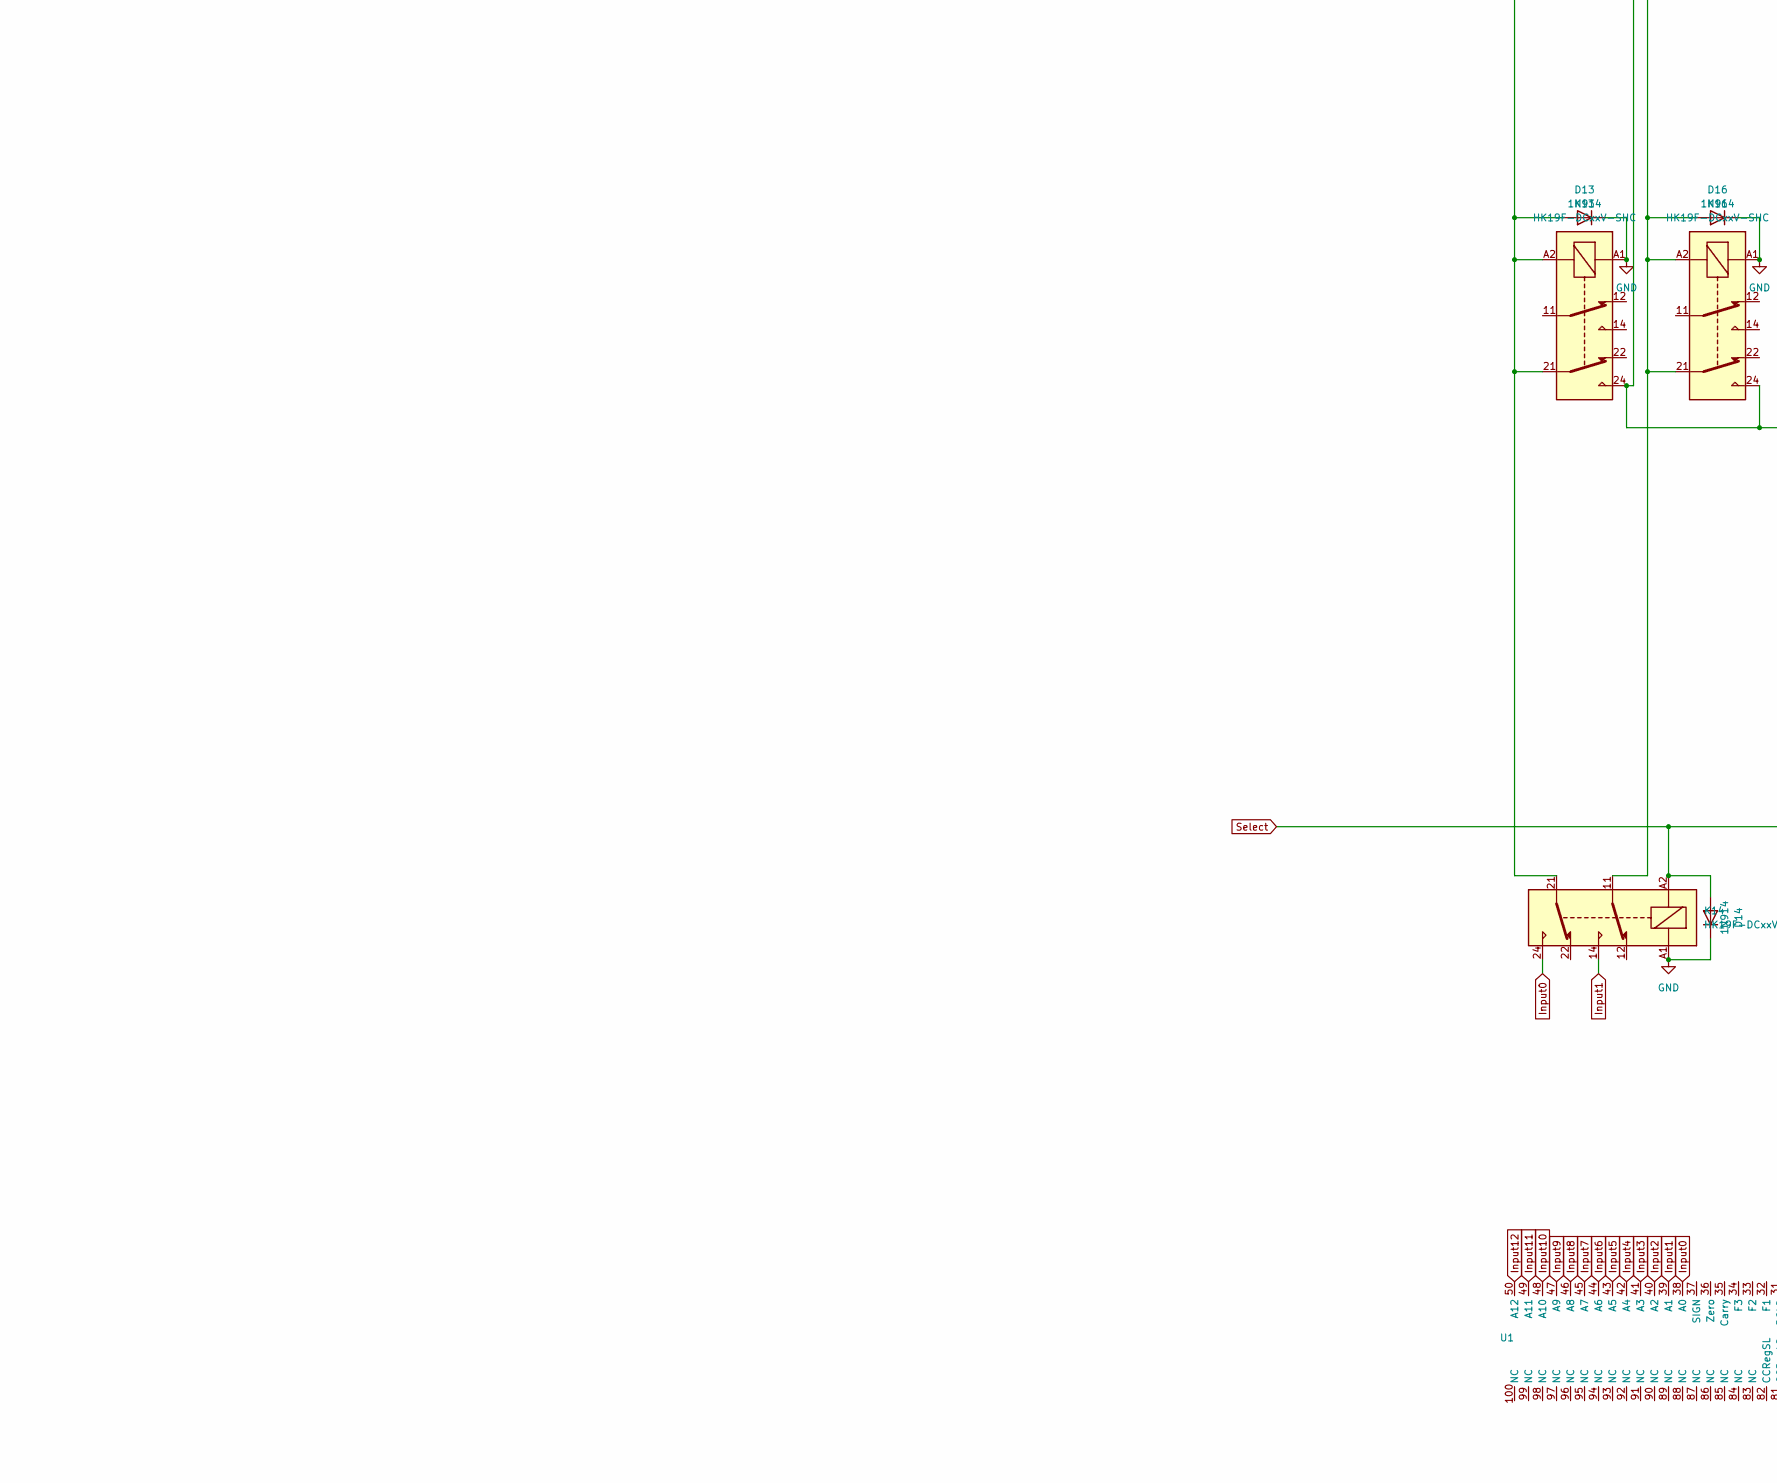
[picture p54: schematic Incrementer.kicad_sch, part in row 2, column 1]

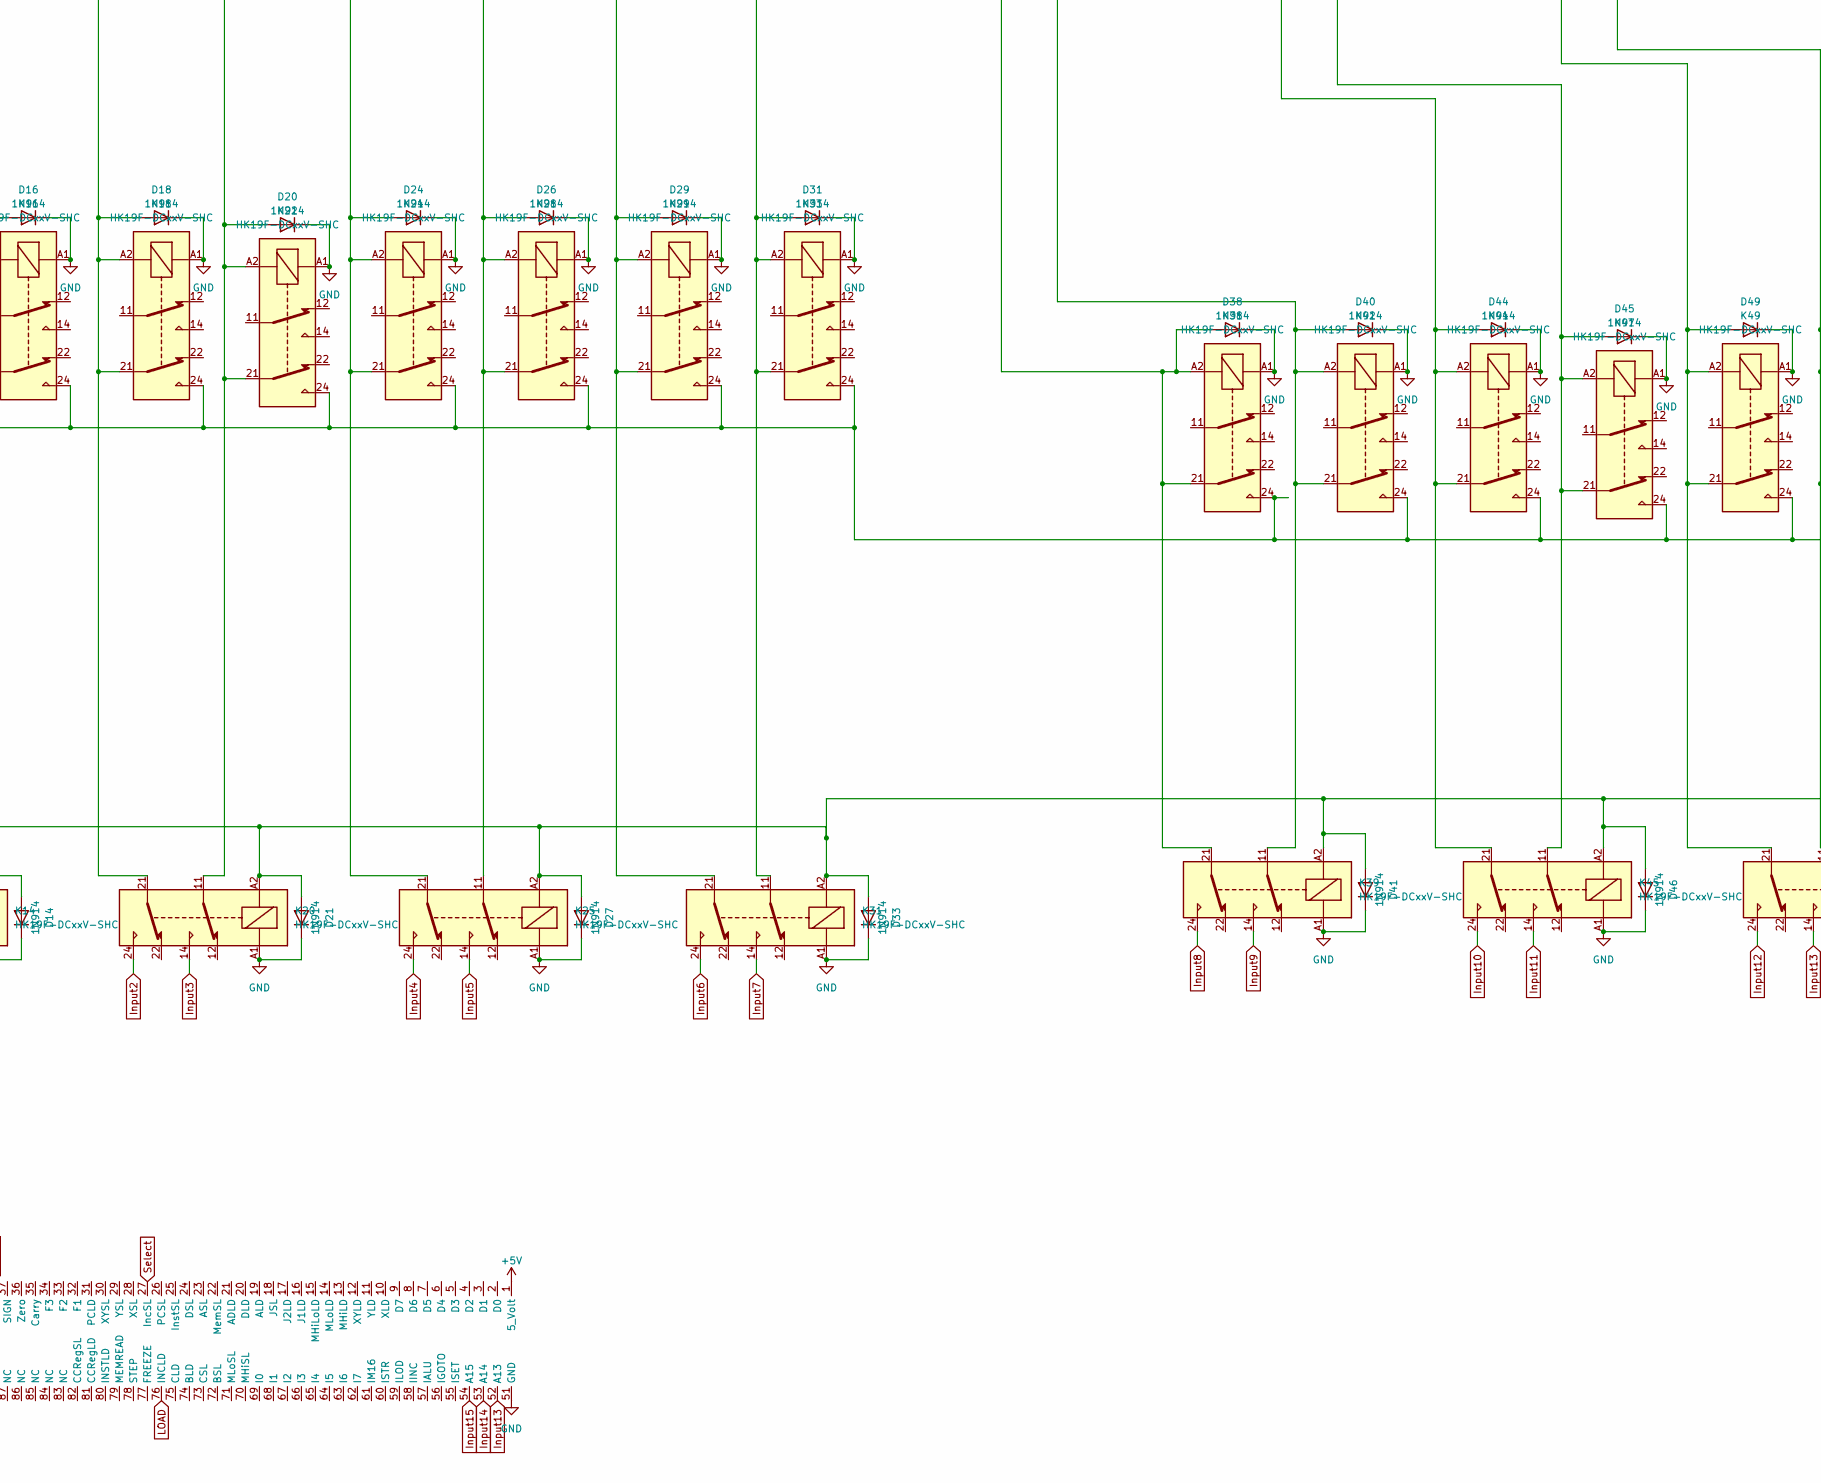
[picture p55: schematic Incrementer.kicad_sch, part in row 2, column 2]

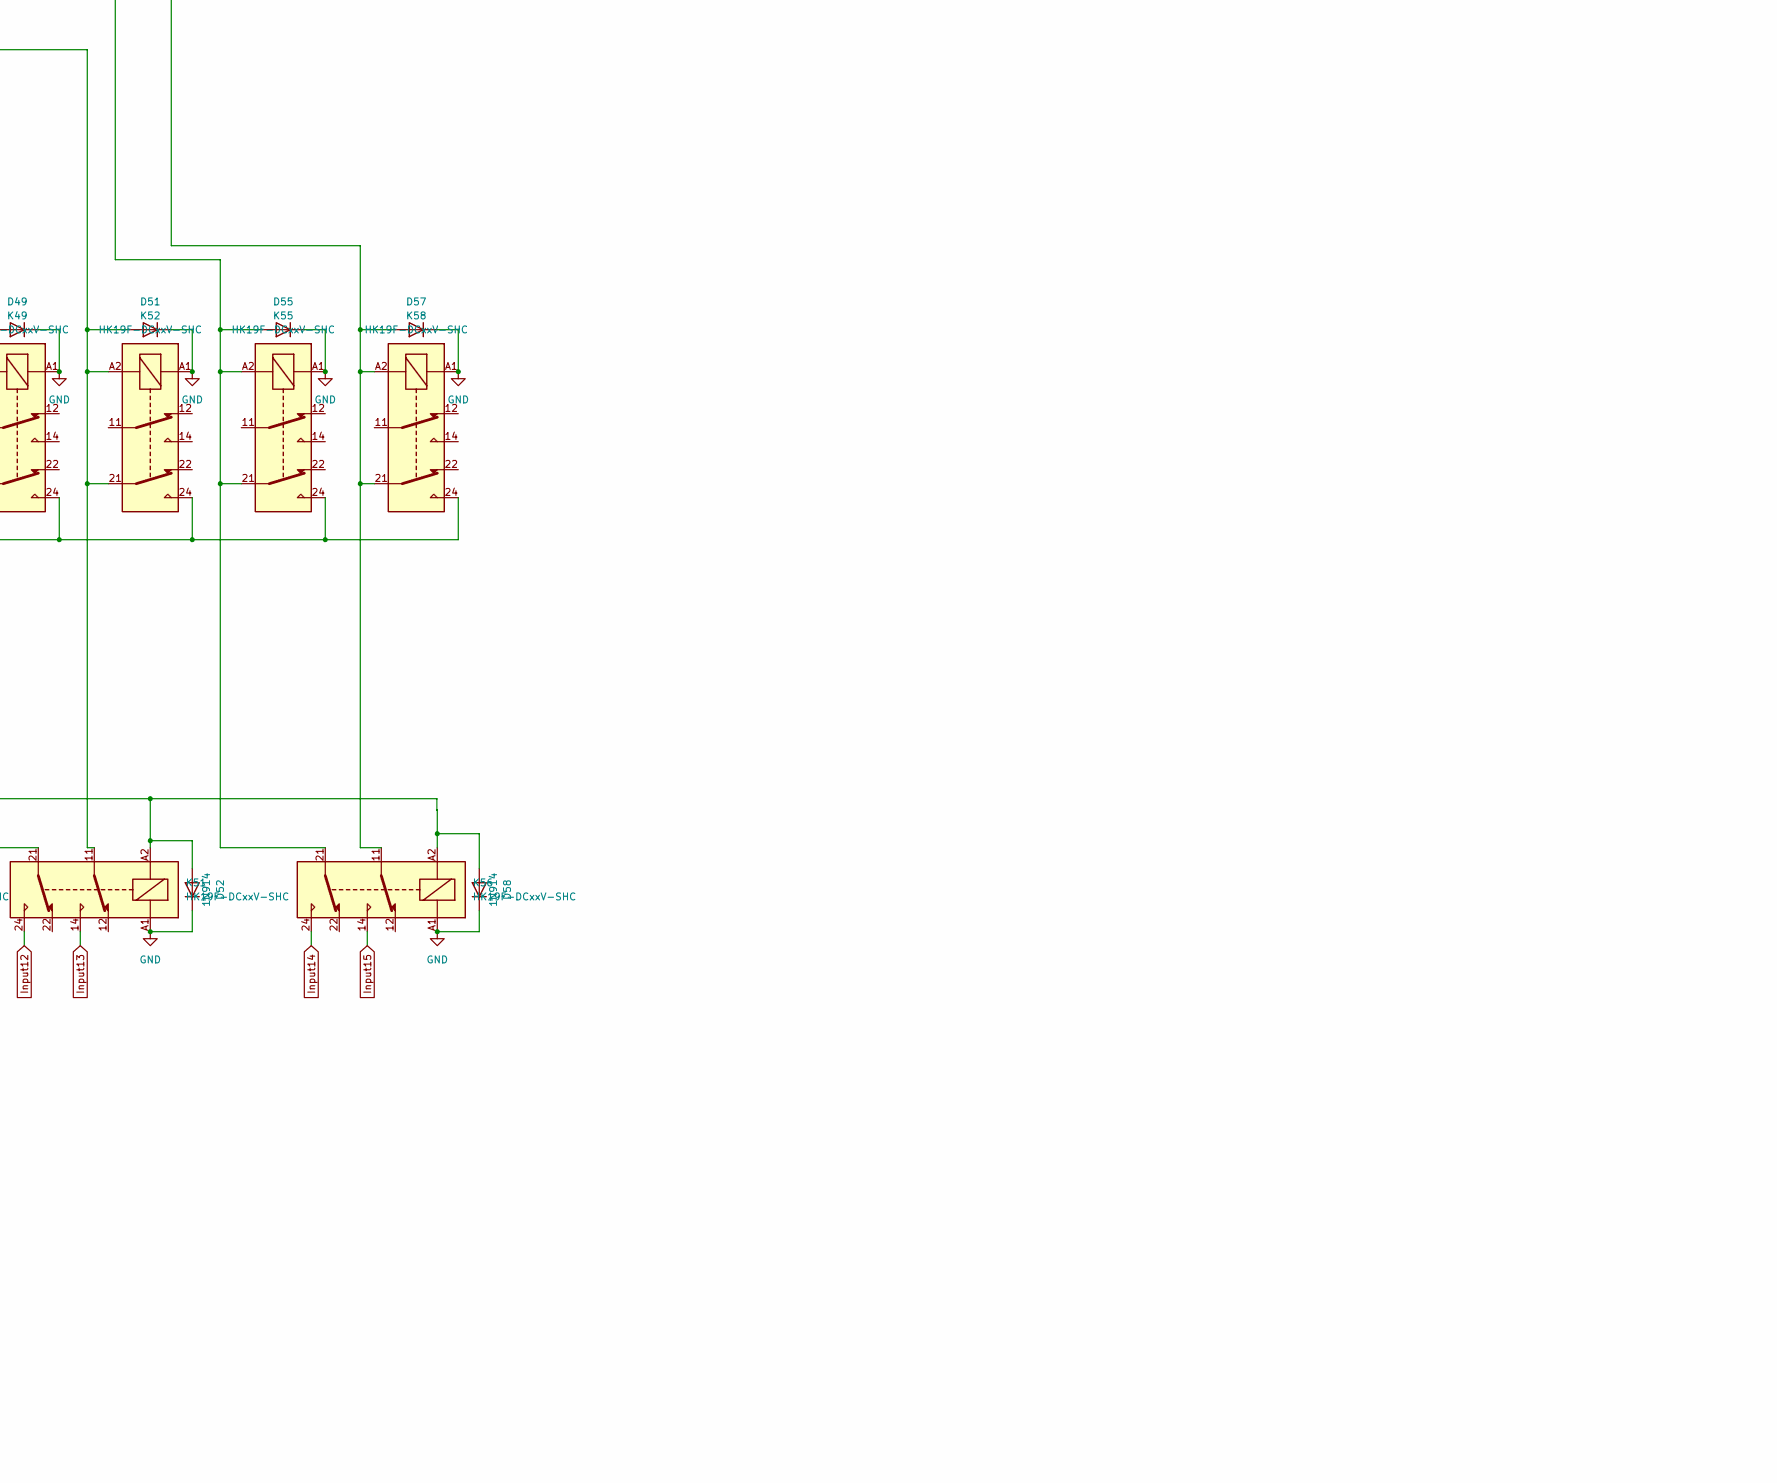
[picture p56: schematic Incrementer.kicad_sch, part in row 2, column 3]

Parts:
D1, D2, D3, D4, D5, D6, D7, D8, D9, D10, D11, D12, D13, D14, D15, D16, D17, D18, D19, D20, D21, D22, D23, D24, D25, D26, D27, D28, D29, D30, D31, D32, D33, D34, D35, D36, D37, D38, D39, D40, D41, D42, D43, D44, D45, D46, D47, D48, D49, D50, D51, D52, D53, D54, D55, D56, D57, D58, D77, D78, D79, D80, D81, D82, D83, D84: 1N914; D_DO-35_SOD27_P7.62mm_Horizontal
D59, D60, D61, D62, D63, D64, D65, D66, D67, D68, D85, D86, D87, D88, D89, D90, D91, D92: LED; LED_D3.0mm
K1, K2, K3, K4, K5, K6, K7, K8, K9, K10, K11, K12, K13, K14, K15, K16, K17, K18, K19, K20, K21, K22, K23, K24, K25, K26, K27, K28, K29, K30, K31, K32, K33, K34, K35, K36, K37, K38, K39, K40, K41, K42, K43, K44, K45, K46, K47, K48, K49, K50, K51, K52, K53, K54, K55, K56, K57, K58, K59, K60, K61, K62, K63, K64, K65, K66: HK19F-DCxxV-SHC; Relay_DPDT_Finder_30.22
R1, R2, R3, R4, R5, R6, R7, R8, R9, R10, R11, R12, R13, R14, R15, R16, R17, R18: R; R_Axial_DIN0207_L6.3mm_D2.5mm_P7.62mm_Horizontal
U1: Conn_RC_Male_100

Connections:
+5V: K1.22, K3.22, K5.22, K7.22, K9.11, K9.21, K10.22, K11.11, K17.22, K23.22, K30.22, K35.22, K41.22, K48.22, K54.22, K59.22, K61.22, K63.22, K65.22, U1.1 (5_Volt)
-Carry In: K3.14, K3.24, K7.14, K7.24, K17.14, K17.24, K30.14, K30.24, K41.14, K41.24, K54.14, K54.24, K61.14, K61.24, K65.14, K65.24
-Carry Out: K1.21, K5.21, K10.21, K23.21, K35.21, K48.21, K59.21, K63.21
Carry In: K65.12, K66.24
Carry Out: K2.21
GND: D1.1 (K), D2.1 (K), D3.1 (K), D4.1 (K), D5.1 (K), D6.1 (K), D7.1 (K), D8.1 (K), D9.1 (K), D10.1 (K), D11.1 (K), D12.1 (K), D13.1 (K), D14.1 (K), D15.1 (K), D16.1 (K), D17.1 (K), D18.1 (K), D19.1 (K), D20.1 (K), D21.1 (K), D22.1 (K), D23.1 (K), D24.1 (K), D25.1 (K), D26.1 (K), D27.1 (K), D28.1 (K), D29.1 (K), D30.1 (K), D31.1 (K), D32.1 (K), D33.1 (K), D34.1 (K), D35.1 (K), D36.1 (K), D37.1 (K), D38.1 (K), D39.1 (K), D40.1 (K), D41.1 (K), D42.1 (K), D43.1 (K), D44.1 (K), D45.1 (K), D46.1 (K), D47.1 (K), D48.1 (K), D49.1 (K), D50.1 (K), D51.1 (K), D52.1 (K), D53.1 (K), D54.1 (K), D55.1 (K), D56.1 (K), D57.1 (K), D58.1 (K), D59.1 (K), D60.1 (K), D61.1 (K), D62.1 (K), D63.1 (K), D64.1 (K), D65.1 (K), D66.1 (K), D67.1 (K), D68.1 (K), D77.1 (K), D78.1 (K), D79.1 (K), D80.1 (K), D81.1 (K), D82.1 (K), D83.1 (K), D84.1 (K), D85.1 (K), D86.1 (K), D87.1 (K), D88.1 (K), D89.1 (K), D90.1 (K), D91.1 (K), D92.1 (K), K1.A1, K2.A1, K3.A1, K4.A1, K5.A1, K6.A1, K7.A1, K8.A1, K9.A1, K10.A1, K11.A1, K12.A1, K13.A1, K14.A1, K15.A1, K16.A1, K17.A1, K18.A1, K19.A1, K20.A1, K21.A1, K22.A1, K23.A1, K24.A1, K25.A1, K26.A1, K27.A1, K28.A1, K29.A1, K30.A1, K31.A1, K32.A1, K33.A1, K34.A1, K35.A1, K36.A1, K37.A1, K38.A1, K39.A1, K40.A1, K41.A1, K42.A1, K43.A1, K44.A1, K45.A1, K46.A1, K47.A1, K48.A1, K49.A1, K50.A1, K51.A1, K52.A1, K53.A1, K54.A1, K55.A1, K56.A1, K57.A1, K58.A1, K59.A1, K60.A1, K61.A1, K62.A1, K63.A1, K64.A1, K65.A1, K66.A1, U1.51 (GND)
Input0: D1.2 (A), D2.2 (A), K1.A2, K2.A2, K14.24, R18.2, U1.38 (A0)
Input1: D3.2 (A), D4.2 (A), K3.A2, K4.A2, K14.14, R17.2, U1.39 (A1)
Input2: D5.2 (A), D6.2 (A), K5.A2, K6.A2, K20.24, R16.2, U1.40 (A2)
Input3: D7.2 (A), D8.2 (A), K7.A2, K8.A2, K20.14, R15.2, U1.41 (A3)
Input4: D10.2 (A), D12.2 (A), K10.A2, K12.A2, K25.24, R14.2, U1.42 (A4)
Input5: D17.2 (A), D19.2 (A), K17.A2, K19.A2, K25.14, R13.2, U1.43 (A5)
Input6: D23.2 (A), D25.2 (A), K23.A2, K27.A2, K31.24, R12.2, U1.44 (A6)
Input7: D30.2 (A), D32.2 (A), K30.A2, K31.14, K34.A2, R11.2, U1.45 (A7)
Input8: D35.2 (A), D36.2 (A), K35.A2, K37.A2, K39.24, R10.2, U1.46 (A8)
Input9: D39.2 (A), D43.2 (A), K39.14, K41.A2, K43.A2, R9.2, U1.47 (A9)
Input10: D47.2 (A), D50.2 (A), K45.24, K48.A2, K50.A2, R8.2, U1.48 (A10)
Input11: D53.2 (A), D56.2 (A), K45.14, K54.A2, K57.A2, R7.2, U1.49 (A11)
Input12: D77.2 (A), D78.2 (A), K51.24, K59.A2, K60.A2, R6.2, U1.50 (A12)
Input13: D79.2 (A), D80.2 (A), K51.14, K61.A2, K62.A2, R5.2, U1.52 (A13)
Input14: D81.2 (A), D82.2 (A), K56.24, K63.A2, K64.A2, R4.2, U1.53 (A14)
Input15: D83.2 (A), D84.2 (A), K56.14, K65.A2, K66.A2, R3.2, U1.54 (A15)
LOAD: D9.2 (A), K9.A2, R2.2, U1.76 (INCLD)
unnamed: D11.2 (A), K9.22, K11.A2
unnamed: D13.2 (A), K13.21, K13.A2, K14.21, K15.21
unnamed: D15.2 (A), D22.2 (A), D28.2 (A), D34.2 (A), D37.2 (A), D42.2 (A), D48.2 (A), D54.2 (A), K11.12, K15.A2, K21.A2, K26.A2, K32.A2, K36.A2, K40.A2, K46.A2, K53.A2
unnamed: D16.2 (A), K14.11, K15.11, K16.21, K16.A2
unnamed: D18.2 (A), K18.21, K18.A2, K20.21, K21.21
unnamed: D20.2 (A), K20.11, K21.11, K22.21, K22.A2
unnamed: D24.2 (A), K24.21, K24.A2, K25.21, K26.21
unnamed: D26.2 (A), K25.11, K26.11, K28.21, K28.A2
unnamed: D29.2 (A), K29.21, K29.A2, K31.21, K32.21
unnamed: D31.2 (A), K31.11, K32.11, K33.21, K33.A2
unnamed: D38.2 (A), K36.21, K38.21, K38.A2, K39.21
unnamed: D40.2 (A), K36.11, K39.11, K42.21, K42.A2
unnamed: D44.2 (A), K40.21, K44.21, K44.A2, K45.21
unnamed: D45.2 (A), K40.11, K45.11, K47.21, K47.A2
unnamed: D49.2 (A), K46.21, K49.21, K49.A2, K51.21
unnamed: D51.2 (A), K46.11, K51.11, K52.21, K52.A2
unnamed: D55.2 (A), K53.21, K55.21, K55.A2, K56.21
unnamed: D57.2 (A), K53.11, K56.11, K58.21, K58.A2
unnamed: D59.2 (A), R1.1
unnamed: D60.2 (A), R2.1
unnamed: D61.2 (A), R11.1
unnamed: D62.2 (A), R12.1
unnamed: D63.2 (A), R13.1
unnamed: D64.2 (A), R14.1
unnamed: D65.2 (A), R15.1
unnamed: D66.2 (A), R16.1
unnamed: D67.2 (A), R17.1
unnamed: D68.2 (A), R18.1
unnamed: D85.2 (A), R3.1
unnamed: D86.2 (A), R4.1
unnamed: D87.2 (A), R5.1
unnamed: D88.2 (A), R6.1
unnamed: D89.2 (A), R7.1
unnamed: D90.2 (A), R8.1
unnamed: D91.2 (A), R9.1
unnamed: D92.2 (A), R10.1
unnamed: K1.12, K2.24, K4.21
unnamed: K1.14, K1.24, K3.21
unnamed: K3.12, K4.24, K6.21
unnamed: K5.12, K6.24, K8.21
unnamed: K5.14, K5.24, K7.21
unnamed: K10.12, K12.24, K19.21
unnamed: K10.14, K10.24, K17.21
unnamed: K7.12, K8.24, K12.21
unnamed: K9.12, K13.24, K16.24, K18.24, K22.24, K24.24, K28.24, K29.24, K33.24, K38.24, K42.24, K44.24, K47.24, K49.24, K52.24, K55.24, K58.24
unnamed: K17.12, K19.24, K27.21
unnamed: K23.12, K27.24, K34.21
unnamed: K23.14, K23.24, K30.21
unnamed: K30.12, K34.24, K37.21
unnamed: K35.12, K37.24, K43.21
unnamed: K35.14, K35.24, K41.21
unnamed: K41.12, K43.24, K50.21
unnamed: K48.12, K50.24, K57.21
unnamed: K48.14, K48.24, K54.21
unnamed: K54.12, K57.24, K60.21
unnamed: K59.12, K60.24, K62.21
unnamed: K59.14, K59.24, K61.21
unnamed: K61.12, K62.24, K64.21
unnamed: K63.12, K64.24, K66.21
unnamed: K63.14, K63.24, K65.21
Select: D14.2 (A), D21.2 (A), D27.2 (A), D33.2 (A), D41.2 (A), D46.2 (A), D52.2 (A), D58.2 (A), K14.A2, K20.A2, K25.A2, K31.A2, K39.A2, K45.A2, K51.A2, K56.A2, R1.2, U1.27 (IncSL)
Sum0: K1.11, K15.24
Sum1: K3.11, K15.14
Sum2: K5.11, K21.24
Sum3: K7.11, K21.14
Sum4: K10.11, K26.24
Sum5: K17.11, K26.14
Sum6: K23.11, K32.24
Sum7: K30.11, K32.14
Sum8: K35.11, K36.24
Sum9: K36.14, K41.11
Sum10: K40.24, K48.11
Sum11: K40.14, K54.11
Sum12: K46.24, K59.11
Sum13: K46.14, K61.11
Sum14: K53.24, K63.11
Sum15: K53.14, K65.11

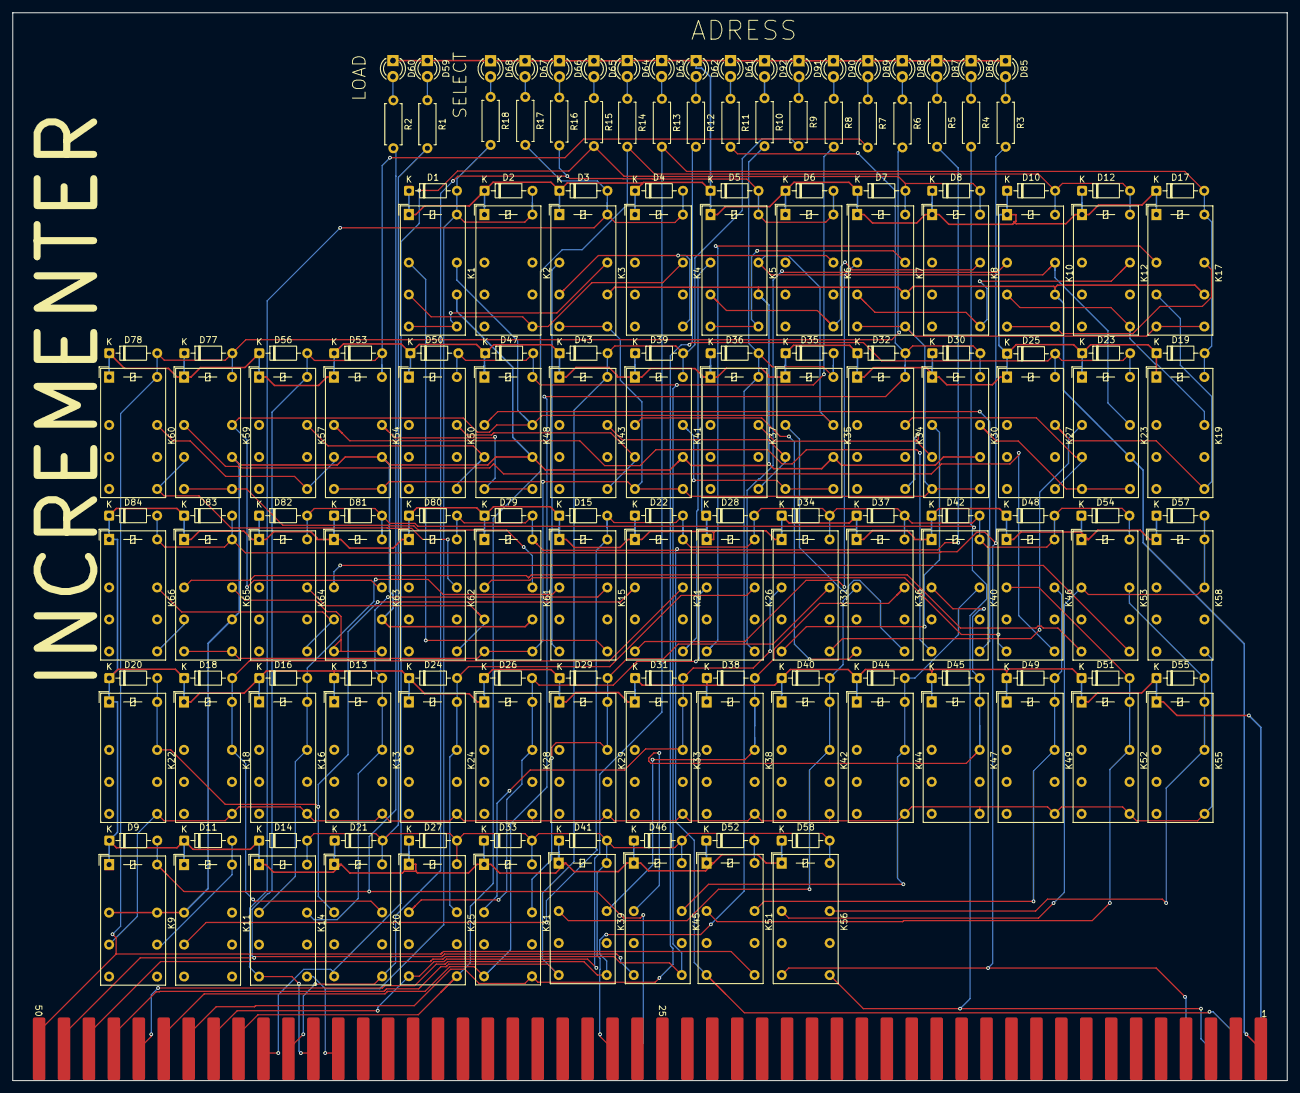
[picture p57: board Incrementer.kicad_pcb from above]

Board: 2 copper layers, 202.4 x 169.6 mm, 169 parts (0 on the bottom side), 99 nets.
