Syntaxer04/RC1Computer/Version 0.1/Bridge/Bridge.kicad_pcb

## KiCad design Version 0.1/Bridge/Bridge.kicad_pcb (2025-06-25, an earlier design)

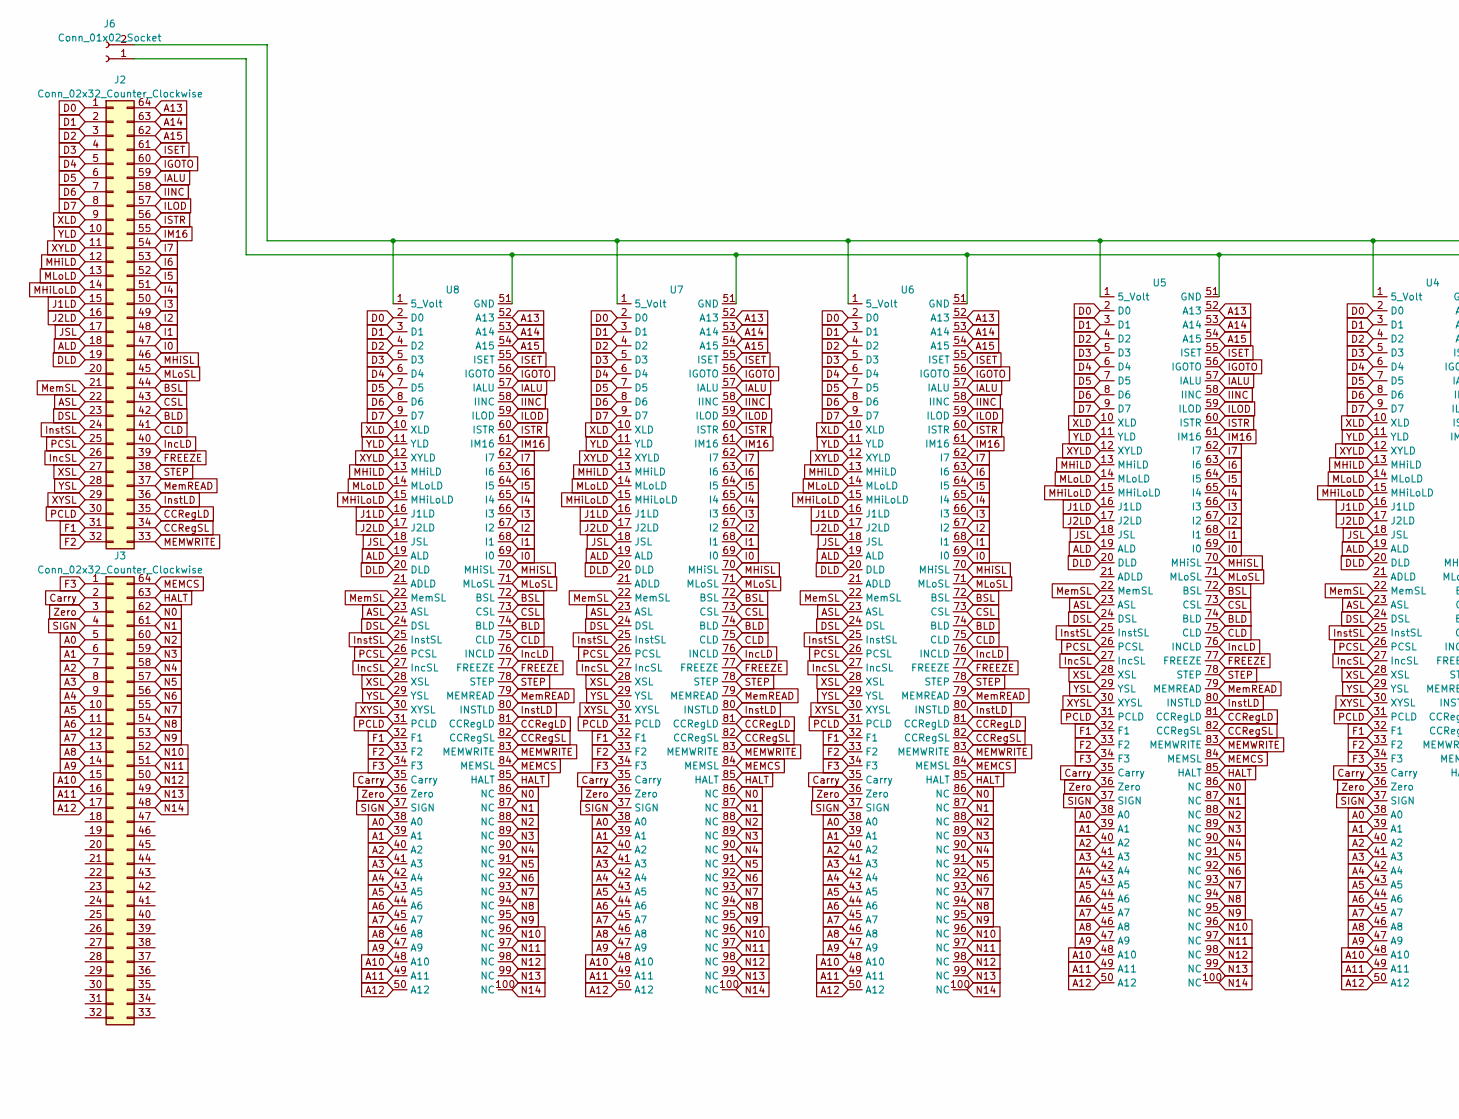
[picture p58: schematic Bridge.kicad_sch, part in row 1, column 1]

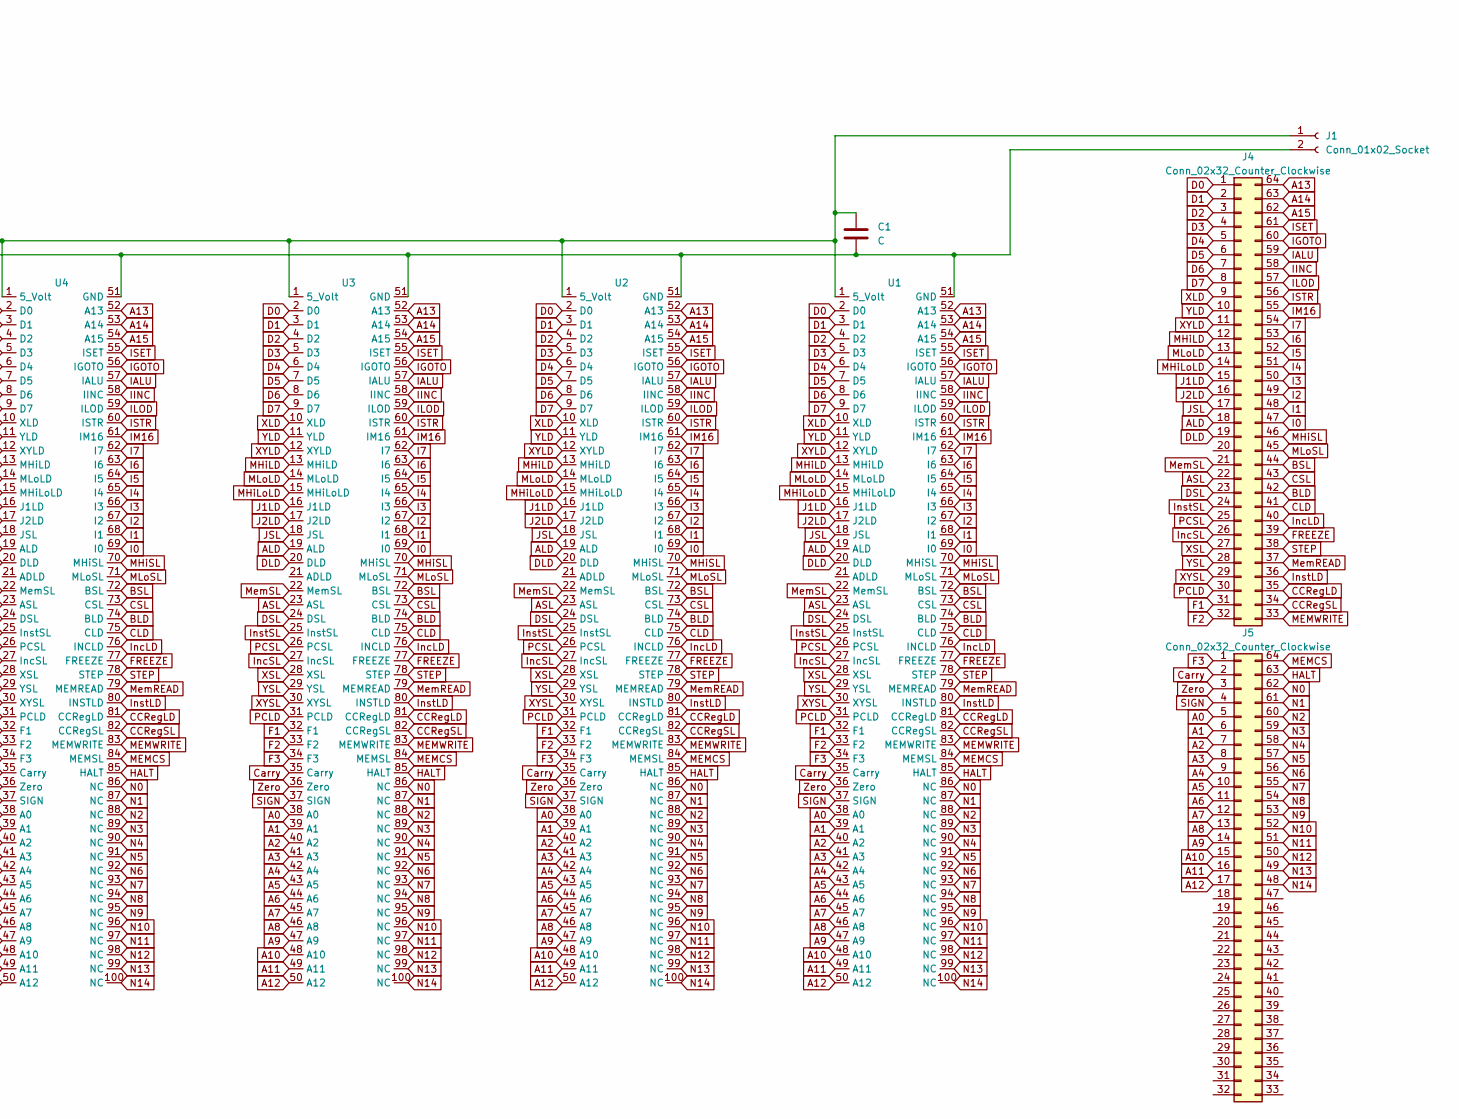
[picture p59: schematic Bridge.kicad_sch, part in row 1, column 2]

Parts:
C1: C; C_Radial_D10.0mm_H12.5mm_P5.00mm
J1, J6: Conn_01x02_Socket; JWT_A3963_1x02_P3.96mm_Vertical
J2, J3, J4, J5: Conn_02x32_Counter_Clockwise; IDC-Header_2x32_P2.54mm_Vertical
U1, U2, U3, U4, U5, U6, U7, U8: Conn_RC_Female_100

Connections:
A0: J3.5, J5.5, U1.38 (A0), U2.38 (A0), U3.38 (A0), U4.38 (A0), U5.38 (A0), U6.38 (A0), U7.38 (A0), U8.38 (A0)
A1: J3.6, J5.6, U1.39 (A1), U2.39 (A1), U3.39 (A1), U4.39 (A1), U5.39 (A1), U6.39 (A1), U7.39 (A1), U8.39 (A1)
A2: J3.7, J5.7, U1.40 (A2), U2.40 (A2), U3.40 (A2), U4.40 (A2), U5.40 (A2), U6.40 (A2), U7.40 (A2), U8.40 (A2)
A3: J3.8, J5.8, U1.41 (A3), U2.41 (A3), U3.41 (A3), U4.41 (A3), U5.41 (A3), U6.41 (A3), U7.41 (A3), U8.41 (A3)
A4: J3.9, J5.9, U1.42 (A4), U2.42 (A4), U3.42 (A4), U4.42 (A4), U5.42 (A4), U6.42 (A4), U7.42 (A4), U8.42 (A4)
A5: J3.10, J5.10, U1.43 (A5), U2.43 (A5), U3.43 (A5), U4.43 (A5), U5.43 (A5), U6.43 (A5), U7.43 (A5), U8.43 (A5)
A6: J3.11, J5.11, U1.44 (A6), U2.44 (A6), U3.44 (A6), U4.44 (A6), U5.44 (A6), U6.44 (A6), U7.44 (A6), U8.44 (A6)
A7: J3.12, J5.12, U1.45 (A7), U2.45 (A7), U3.45 (A7), U4.45 (A7), U5.45 (A7), U6.45 (A7), U7.45 (A7), U8.45 (A7)
A8: J3.13, J5.13, U1.46 (A8), U2.46 (A8), U3.46 (A8), U4.46 (A8), U5.46 (A8), U6.46 (A8), U7.46 (A8), U8.46 (A8)
A9: J3.14, J5.14, U1.47 (A9), U2.47 (A9), U3.47 (A9), U4.47 (A9), U5.47 (A9), U6.47 (A9), U7.47 (A9), U8.47 (A9)
A10: J3.15, J5.15, U1.48 (A10), U2.48 (A10), U3.48 (A10), U4.48 (A10), U5.48 (A10), U6.48 (A10), U7.48 (A10), U8.48 (A10)
A11: J3.16, J5.16, U1.49 (A11), U2.49 (A11), U3.49 (A11), U4.49 (A11), U5.49 (A11), U6.49 (A11), U7.49 (A11), U8.49 (A11)
A12: J3.17, J5.17, U1.50 (A12), U2.50 (A12), U3.50 (A12), U4.50 (A12), U5.50 (A12), U6.50 (A12), U7.50 (A12), U8.50 (A12)
A13: J2.64, J4.64, U1.52 (A13), U2.52 (A13), U3.52 (A13), U4.52 (A13), U5.52 (A13), U6.52 (A13), U7.52 (A13), U8.52 (A13)
A14: J2.63, J4.63, U1.53 (A14), U2.53 (A14), U3.53 (A14), U4.53 (A14), U5.53 (A14), U6.53 (A14), U7.53 (A14), U8.53 (A14)
A15: J2.62, J4.62, U1.54 (A15), U2.54 (A15), U3.54 (A15), U4.54 (A15), U5.54 (A15), U6.54 (A15), U7.54 (A15), U8.54 (A15)
ALD: J2.18, J4.18, U1.19 (ALD), U2.19 (ALD), U3.19 (ALD), U4.19 (ALD), U5.19 (ALD), U6.19 (ALD), U7.19 (ALD), U8.19 (ALD)
ASL: J2.22, J4.22, U1.23 (ASL), U2.23 (ASL), U3.23 (ASL), U4.23 (ASL), U5.23 (ASL), U6.23 (ASL), U7.23 (ASL), U8.23 (ASL)
BLD: J2.42, J4.42, U1.74 (BLD), U2.74 (BLD), U3.74 (BLD), U4.74 (BLD), U5.74 (BLD), U6.74 (BLD), U7.74 (BLD), U8.74 (BLD)
BSL: J2.44, J4.44, U1.72 (BSL), U2.72 (BSL), U3.72 (BSL), U4.72 (BSL), U5.72 (BSL), U6.72 (BSL), U7.72 (BSL), U8.72 (BSL)
CCRegLD: J2.35, J4.35, U1.81 (CCRegLD), U2.81 (CCRegLD), U3.81 (CCRegLD), U4.81 (CCRegLD), U5.81 (CCRegLD), U6.81 (CCRegLD), U7.81 (CCRegLD), U8.81 (CCRegLD)
CCRegSL: J2.34, J4.34, U1.82 (CCRegSL), U2.82 (CCRegSL), U3.82 (CCRegSL), U4.82 (CCRegSL), U5.82 (CCRegSL), U6.82 (CCRegSL), U7.82 (CCRegSL), U8.82 (CCRegSL)
CLD: J2.41, J4.41, U1.75 (CLD), U2.75 (CLD), U3.75 (CLD), U4.75 (CLD), U5.75 (CLD), U6.75 (CLD), U7.75 (CLD), U8.75 (CLD)
CSL: J2.43, J4.43, U1.73 (CSL), U2.73 (CSL), U3.73 (CSL), U4.73 (CSL), U5.73 (CSL), U6.73 (CSL), U7.73 (CSL), U8.73 (CSL)
Carry: J3.2, J5.2, U1.35 (Carry), U2.35 (Carry), U3.35 (Carry), U4.35 (Carry), U5.35 (Carry), U6.35 (Carry), U7.35 (Carry), U8.35 (Carry)
D0: J2.1, J4.1, U1.2 (D0), U2.2 (D0), U3.2 (D0), U4.2 (D0), U5.2 (D0), U6.2 (D0), U7.2 (D0), U8.2 (D0)
D1: J2.2, J4.2, U1.3 (D1), U2.3 (D1), U3.3 (D1), U4.3 (D1), U5.3 (D1), U6.3 (D1), U7.3 (D1), U8.3 (D1)
D2: J2.3, J4.3, U1.4 (D2), U2.4 (D2), U3.4 (D2), U4.4 (D2), U5.4 (D2), U6.4 (D2), U7.4 (D2), U8.4 (D2)
D3: J2.4, J4.4, U1.5 (D3), U2.5 (D3), U3.5 (D3), U4.5 (D3), U5.5 (D3), U6.5 (D3), U7.5 (D3), U8.5 (D3)
D4: J2.5, J4.5, U1.6 (D4), U2.6 (D4), U3.6 (D4), U4.6 (D4), U5.6 (D4), U6.6 (D4), U7.6 (D4), U8.6 (D4)
D5: J2.6, J4.6, U1.7 (D5), U2.7 (D5), U3.7 (D5), U4.7 (D5), U5.7 (D5), U6.7 (D5), U7.7 (D5), U8.7 (D5)
D6: J2.7, J4.7, U1.8 (D6), U2.8 (D6), U3.8 (D6), U4.8 (D6), U5.8 (D6), U6.8 (D6), U7.8 (D6), U8.8 (D6)
D7: J2.8, J4.8, U1.9 (D7), U2.9 (D7), U3.9 (D7), U4.9 (D7), U5.9 (D7), U6.9 (D7), U7.9 (D7), U8.9 (D7)
DLD: J2.19, J4.19, U1.20 (DLD), U2.20 (DLD), U3.20 (DLD), U4.20 (DLD), U5.20 (DLD), U6.20 (DLD), U7.20 (DLD), U8.20 (DLD)
DSL: J2.23, J4.23, U1.24 (DSL), U2.24 (DSL), U3.24 (DSL), U4.24 (DSL), U5.24 (DSL), U6.24 (DSL), U7.24 (DSL), U8.24 (DSL)
F1: J2.31, J4.31, U1.32 (F1), U2.32 (F1), U3.32 (F1), U4.32 (F1), U5.32 (F1), U6.32 (F1), U7.32 (F1), U8.32 (F1)
F2: J2.32, J4.32, U1.33 (F2), U2.33 (F2), U3.33 (F2), U4.33 (F2), U5.33 (F2), U6.33 (F2), U7.33 (F2), U8.33 (F2)
F3: J3.1, J5.1, U1.34 (F3), U2.34 (F3), U3.34 (F3), U4.34 (F3), U5.34 (F3), U6.34 (F3), U7.34 (F3), U8.34 (F3)
FREEZE: J2.39, J4.39, U1.77 (FREEZE), U2.77 (FREEZE), U3.77 (FREEZE), U4.77 (FREEZE), U5.77 (FREEZE), U6.77 (FREEZE), U7.77 (FREEZE), U8.77 (FREEZE)
HALT: J3.63, J5.63, U1.85 (HALT), U2.85 (HALT), U3.85 (HALT), U4.85 (HALT), U5.85 (HALT), U6.85 (HALT), U7.85 (HALT), U8.85 (HALT)
I0: J2.47, J4.47, U1.69 (I0), U2.69 (I0), U3.69 (I0), U4.69 (I0), U5.69 (I0), U6.69 (I0), U7.69 (I0), U8.69 (I0)
I1: J2.48, J4.48, U1.68 (I1), U2.68 (I1), U3.68 (I1), U4.68 (I1), U5.68 (I1), U6.68 (I1), U7.68 (I1), U8.68 (I1)
I2: J2.49, J4.49, U1.67 (I2), U2.67 (I2), U3.67 (I2), U4.67 (I2), U5.67 (I2), U6.67 (I2), U7.67 (I2), U8.67 (I2)
I3: J2.50, J4.50, U1.66 (I3), U2.66 (I3), U3.66 (I3), U4.66 (I3), U5.66 (I3), U6.66 (I3), U7.66 (I3), U8.66 (I3)
I4: J2.51, J4.51, U1.65 (I4), U2.65 (I4), U3.65 (I4), U4.65 (I4), U5.65 (I4), U6.65 (I4), U7.65 (I4), U8.65 (I4)
I5: J2.52, J4.52, U1.64 (I5), U2.64 (I5), U3.64 (I5), U4.64 (I5), U5.64 (I5), U6.64 (I5), U7.64 (I5), U8.64 (I5)
I6: J2.53, J4.53, U1.63 (I6), U2.63 (I6), U3.63 (I6), U4.63 (I6), U5.63 (I6), U6.63 (I6), U7.63 (I6), U8.63 (I6)
I7: J2.54, J4.54, U1.62 (I7), U2.62 (I7), U3.62 (I7), U4.62 (I7), U5.62 (I7), U6.62 (I7), U7.62 (I7), U8.62 (I7)
IALU: J2.59, J4.59, U1.57 (IALU), U2.57 (IALU), U3.57 (IALU), U4.57 (IALU), U5.57 (IALU), U6.57 (IALU), U7.57 (IALU), U8.57 (IALU)
IGOTO: J2.60, J4.60, U1.56 (IGOTO), U2.56 (IGOTO), U3.56 (IGOTO), U4.56 (IGOTO), U5.56 (IGOTO), U6.56 (IGOTO), U7.56 (IGOTO), U8.56 (IGOTO)
IINC: J2.58, J4.58, U1.58 (IINC), U2.58 (IINC), U3.58 (IINC), U4.58 (IINC), U5.58 (IINC), U6.58 (IINC), U7.58 (IINC), U8.58 (IINC)
ILOD: J2.57, J4.57, U1.59 (ILOD), U2.59 (ILOD), U3.59 (ILOD), U4.59 (ILOD), U5.59 (ILOD), U6.59 (ILOD), U7.59 (ILOD), U8.59 (ILOD)
IM16: J2.55, J4.55, U1.61 (IM16), U2.61 (IM16), U3.61 (IM16), U4.61 (IM16), U5.61 (IM16), U6.61 (IM16), U7.61 (IM16), U8.61 (IM16)
ISET: J2.61, J4.61, U1.55 (ISET), U2.55 (ISET), U3.55 (ISET), U4.55 (ISET), U5.55 (ISET), U6.55 (ISET), U7.55 (ISET), U8.55 (ISET)
ISTR: J2.56, J4.56, U1.60 (ISTR), U2.60 (ISTR), U3.60 (ISTR), U4.60 (ISTR), U5.60 (ISTR), U6.60 (ISTR), U7.60 (ISTR), U8.60 (ISTR)
IncLD: J2.40, J4.40, U1.76 (INCLD), U2.76 (INCLD), U3.76 (INCLD), U4.76 (INCLD), U5.76 (INCLD), U6.76 (INCLD), U7.76 (INCLD), U8.76 (INCLD)
IncSL: J2.26, J4.26, U1.27 (IncSL), U2.27 (IncSL), U3.27 (IncSL), U4.27 (IncSL), U5.27 (IncSL), U6.27 (IncSL), U7.27 (IncSL), U8.27 (IncSL)
InstLD: J2.36, J4.36, U1.80 (INSTLD), U2.80 (INSTLD), U3.80 (INSTLD), U4.80 (INSTLD), U5.80 (INSTLD), U6.80 (INSTLD), U7.80 (INSTLD), U8.80 (INSTLD)
InstSL: J2.24, J4.24, U1.25 (InstSL), U2.25 (InstSL), U3.25 (InstSL), U4.25 (InstSL), U5.25 (InstSL), U6.25 (InstSL), U7.25 (InstSL), U8.25 (InstSL)
J1LD: J2.15, J4.15, U1.16 (J1LD), U2.16 (J1LD), U3.16 (J1LD), U4.16 (J1LD), U5.16 (J1LD), U6.16 (J1LD), U7.16 (J1LD), U8.16 (J1LD)
J2LD: J2.16, J4.16, U1.17 (J2LD), U2.17 (J2LD), U3.17 (J2LD), U4.17 (J2LD), U5.17 (J2LD), U6.17 (J2LD), U7.17 (J2LD), U8.17 (J2LD)
JSL: J2.17, J4.17, U1.18 (JSL), U2.18 (JSL), U3.18 (JSL), U4.18 (JSL), U5.18 (JSL), U6.18 (JSL), U7.18 (JSL), U8.18 (JSL)
MEMCS: J3.64, J5.64, U1.84 (MEMSL), U2.84 (MEMSL), U3.84 (MEMSL), U4.84 (MEMSL), U5.84 (MEMSL), U6.84 (MEMSL), U7.84 (MEMSL), U8.84 (MEMSL)
MEMWRITE: J2.33, J4.33, U1.83 (MEMWRITE), U2.83 (MEMWRITE), U3.83 (MEMWRITE), U4.83 (MEMWRITE), U5.83 (MEMWRITE), U6.83 (MEMWRITE), U7.83 (MEMWRITE), U8.83 (MEMWRITE)
MHiLD: J2.12, J4.12, U1.13 (MHiLD), U2.13 (MHiLD), U3.13 (MHiLD), U4.13 (MHiLD), U5.13 (MHiLD), U6.13 (MHiLD), U7.13 (MHiLD), U8.13 (MHiLD)
MHiLoLD: J2.14, J4.14, U1.15 (MHiLoLD), U2.15 (MHiLoLD), U3.15 (MHiLoLD), U4.15 (MHiLoLD), U5.15 (MHiLoLD), U6.15 (MHiLoLD), U7.15 (MHiLoLD), U8.15 (MHiLoLD)
MHiSL: J2.46, J4.46, U1.70 (MHiSL), U2.70 (MHiSL), U3.70 (MHiSL), U4.70 (MHiSL), U5.70 (MHiSL), U6.70 (MHiSL), U7.70 (MHiSL), U8.70 (MHiSL)
MLoLD: J2.13, J4.13, U1.14 (MLoLD), U2.14 (MLoLD), U3.14 (MLoLD), U4.14 (MLoLD), U5.14 (MLoLD), U6.14 (MLoLD), U7.14 (MLoLD), U8.14 (MLoLD)
MLoSL: J2.45, J4.45, U1.71 (MLoSL), U2.71 (MLoSL), U3.71 (MLoSL), U4.71 (MLoSL), U5.71 (MLoSL), U6.71 (MLoSL), U7.71 (MLoSL), U8.71 (MLoSL)
MemREAD: J2.37, J4.37, U1.79 (MEMREAD), U2.79 (MEMREAD), U3.79 (MEMREAD), U4.79 (MEMREAD), U5.79 (MEMREAD), U6.79 (MEMREAD), U7.79 (MEMREAD), U8.79 (MEMREAD)
MemSL: J2.21, J4.21, U1.22 (MemSL), U2.22 (MemSL), U3.22 (MemSL), U4.22 (MemSL), U5.22 (MemSL), U6.22 (MemSL), U7.22 (MemSL), U8.22 (MemSL)
N0: J3.62, J5.62, U1.86 (NC), U2.86 (NC), U3.86 (NC), U4.86 (NC), U5.86 (NC), U6.86 (NC), U7.86 (NC), U8.86 (NC)
N1: J3.61, J5.61, U1.87 (NC), U2.87 (NC), U3.87 (NC), U4.87 (NC), U5.87 (NC), U6.87 (NC), U7.87 (NC), U8.87 (NC)
N2: J3.60, J5.60, U1.88 (NC), U2.88 (NC), U3.88 (NC), U4.88 (NC), U5.88 (NC), U6.88 (NC), U7.88 (NC), U8.88 (NC)
N3: J3.59, J5.59, U1.89 (NC), U2.89 (NC), U3.89 (NC), U4.89 (NC), U5.89 (NC), U6.89 (NC), U7.89 (NC), U8.89 (NC)
N4: J3.58, J5.58, U1.90 (NC), U2.90 (NC), U3.90 (NC), U4.90 (NC), U5.90 (NC), U6.90 (NC), U7.90 (NC), U8.90 (NC)
N5: J3.57, J5.57, U1.91 (NC), U2.91 (NC), U3.91 (NC), U4.91 (NC), U5.91 (NC), U6.91 (NC), U7.91 (NC), U8.91 (NC)
N6: J3.56, J5.56, U1.92 (NC), U2.92 (NC), U3.92 (NC), U4.92 (NC), U5.92 (NC), U6.92 (NC), U7.92 (NC), U8.92 (NC)
N7: J3.55, J5.55, U1.93 (NC), U2.93 (NC), U3.93 (NC), U4.93 (NC), U5.93 (NC), U6.93 (NC), U7.93 (NC), U8.93 (NC)
N8: J3.54, J5.54, U1.94 (NC), U2.94 (NC), U3.94 (NC), U4.94 (NC), U5.94 (NC), U6.94 (NC), U7.94 (NC), U8.94 (NC)
N9: J3.53, J5.53, U1.95 (NC), U2.95 (NC), U3.95 (NC), U4.95 (NC), U5.95 (NC), U6.95 (NC), U7.95 (NC), U8.95 (NC)
N10: J3.52, J5.52, U1.96 (NC), U2.96 (NC), U3.96 (NC), U4.96 (NC), U5.96 (NC), U6.96 (NC), U7.96 (NC), U8.96 (NC)
N11: J3.51, J5.51, U1.97 (NC), U2.97 (NC), U3.97 (NC), U4.97 (NC), U5.97 (NC), U6.97 (NC), U7.97 (NC), U8.97 (NC)
N12: J3.50, J5.50, U1.98 (NC), U2.98 (NC), U3.98 (NC), U4.98 (NC), U5.98 (NC), U6.98 (NC), U7.98 (NC), U8.98 (NC)
N13: J3.49, J5.49, U1.99 (NC), U2.99 (NC), U3.99 (NC), U4.99 (NC), U5.99 (NC), U6.99 (NC), U7.99 (NC), U8.99 (NC)
N14: J3.48, J5.48, U1.100 (NC), U2.100 (NC), U3.100 (NC), U4.100 (NC), U5.100 (NC), U6.100 (NC), U7.100 (NC), U8.100 (NC)
unnamed: C1.1, J1.1, J6.2, U1.1 (5_Volt), U2.1 (5_Volt), U3.1 (5_Volt), U4.1 (5_Volt), U5.1 (5_Volt), U6.1 (5_Volt), U7.1 (5_Volt), U8.1 (5_Volt)
unnamed: C1.2, J1.2, J6.1, U1.51 (GND), U2.51 (GND), U3.51 (GND), U4.51 (GND), U5.51 (GND), U6.51 (GND), U7.51 (GND), U8.51 (GND)
PCLD: J2.30, J4.30, U1.31 (PCLD), U2.31 (PCLD), U3.31 (PCLD), U4.31 (PCLD), U5.31 (PCLD), U6.31 (PCLD), U7.31 (PCLD), U8.31 (PCLD)
PCSL: J2.25, J4.25, U1.26 (PCSL), U2.26 (PCSL), U3.26 (PCSL), U4.26 (PCSL), U5.26 (PCSL), U6.26 (PCSL), U7.26 (PCSL), U8.26 (PCSL)
SIGN: J3.4, J5.4, U1.37 (SIGN), U2.37 (SIGN), U3.37 (SIGN), U4.37 (SIGN), U5.37 (SIGN), U6.37 (SIGN), U7.37 (SIGN), U8.37 (SIGN)
STEP: J2.38, J4.38, U1.78 (STEP), U2.78 (STEP), U3.78 (STEP), U4.78 (STEP), U5.78 (STEP), U6.78 (STEP), U7.78 (STEP), U8.78 (STEP)
XLD: J2.9, J4.9, U1.10 (XLD), U2.10 (XLD), U3.10 (XLD), U4.10 (XLD), U5.10 (XLD), U6.10 (XLD), U7.10 (XLD), U8.10 (XLD)
XSL: J2.27, J4.27, U1.28 (XSL), U2.28 (XSL), U3.28 (XSL), U4.28 (XSL), U5.28 (XSL), U6.28 (XSL), U7.28 (XSL), U8.28 (XSL)
XYLD: J2.11, J4.11, U1.12 (XYLD), U2.12 (XYLD), U3.12 (XYLD), U4.12 (XYLD), U5.12 (XYLD), U6.12 (XYLD), U7.12 (XYLD), U8.12 (XYLD)
XYSL: J2.29, J4.29, U1.30 (XYSL), U2.30 (XYSL), U3.30 (XYSL), U4.30 (XYSL), U5.30 (XYSL), U6.30 (XYSL), U7.30 (XYSL), U8.30 (XYSL)
YLD: J2.10, J4.10, U1.11 (YLD), U2.11 (YLD), U3.11 (YLD), U4.11 (YLD), U5.11 (YLD), U6.11 (YLD), U7.11 (YLD), U8.11 (YLD)
YSL: J2.28, J4.28, U1.29 (YSL), U2.29 (YSL), U3.29 (YSL), U4.29 (YSL), U5.29 (YSL), U6.29 (YSL), U7.29 (YSL), U8.29 (YSL)
Zero: J3.3, J5.3, U1.36 (Zero), U2.36 (Zero), U3.36 (Zero), U4.36 (Zero), U5.36 (Zero), U6.36 (Zero), U7.36 (Zero), U8.36 (Zero)

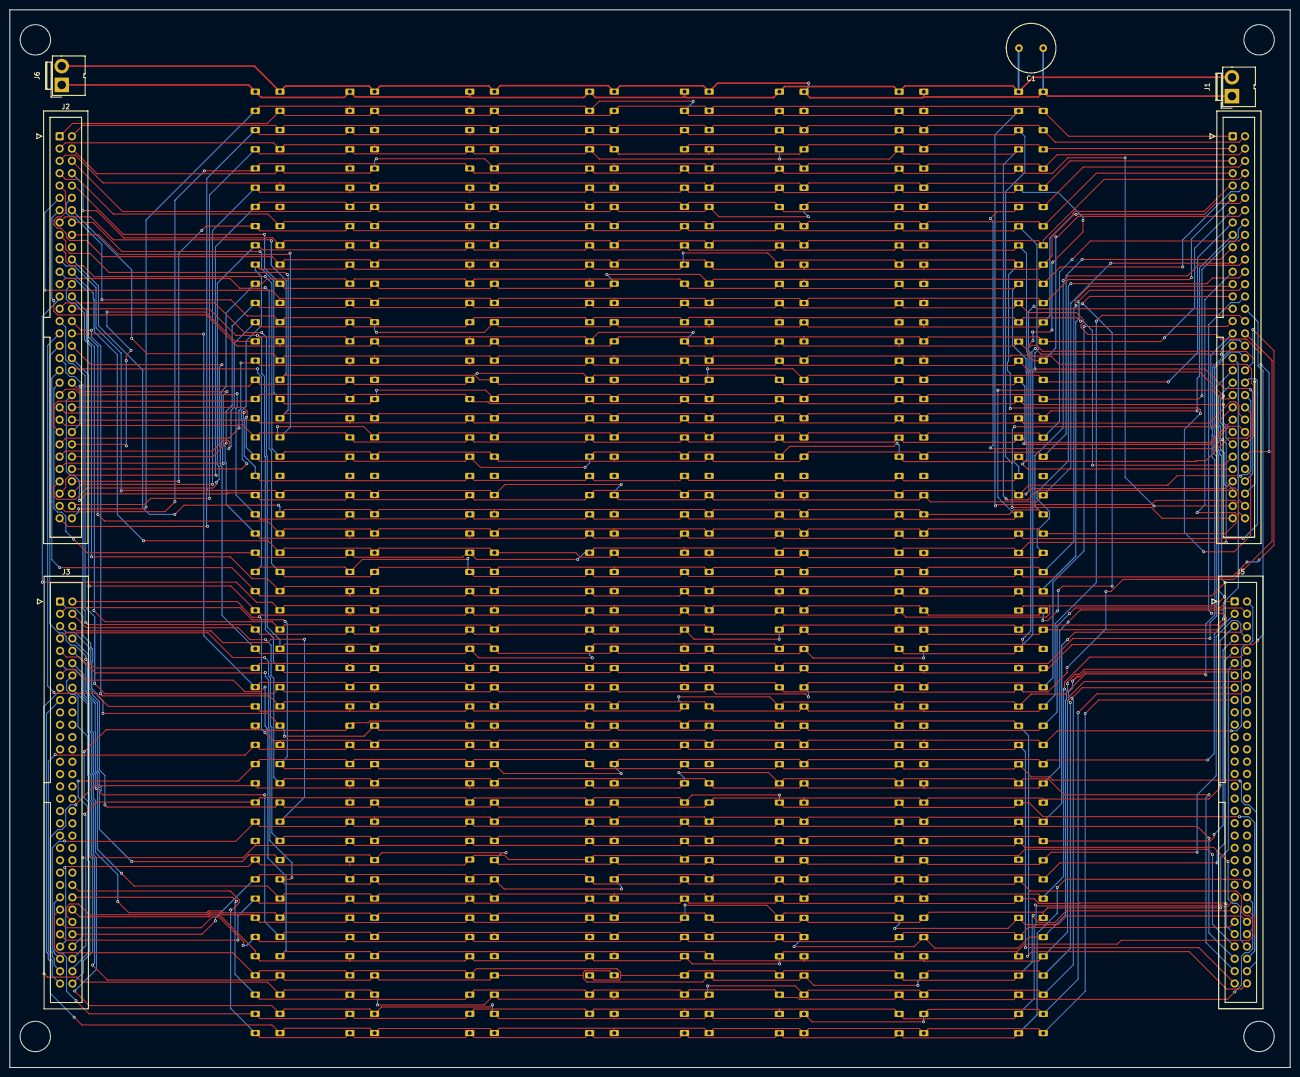
[picture p60: board Bridge.kicad_pcb from above]

Board: 2 copper layers, 263.9 x 218.0 mm, 15 parts (0 on the bottom side), 99 nets.
