Syntaxer04/RC1Computer/Version 0.1/ALU/ALU.kicad_pcb

## KiCad design Version 0.1/ALU/ALU.kicad_pcb (2025-06-25, an earlier design)

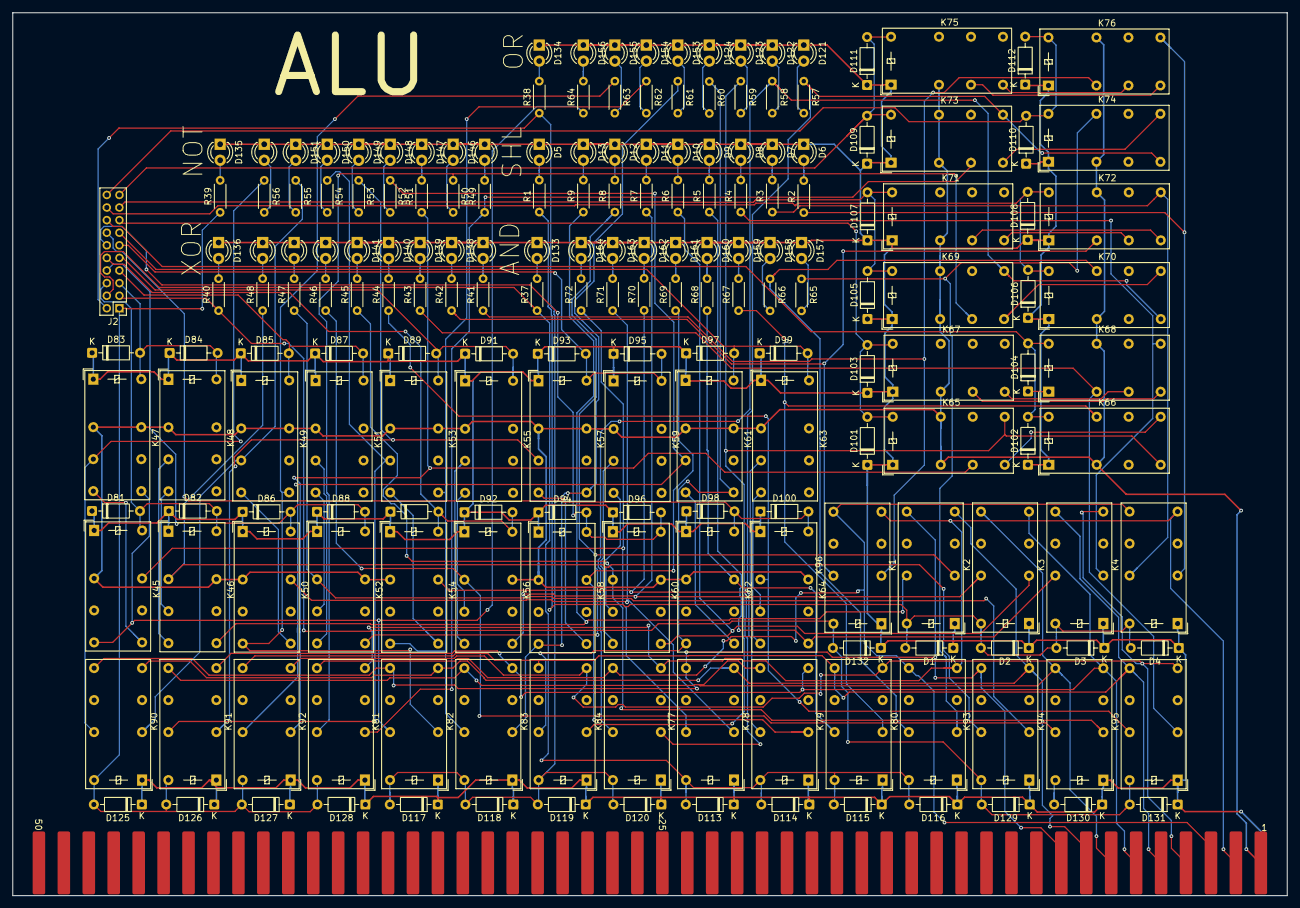
[picture p61: board ALU.kicad_pcb from above]

Board: 2 copper layers, 202.4 x 140.2 mm, 196 parts (0 on the bottom side), 142 nets.

Parts:
D1, D2, D3, D4, D81, D82, D83, D84, D85, D86, D87, D88, D89, D90, D91, D92, D93, D94, D95, D96, D97, D98, D99, D100, D101, D102, D103, D104, D105, D106, D107, D108, D109, D110, D111, D112, D113, D114, D115, D116, D117, D118, D119, D120, D125, D126, D127, D128, D129, D130, D131, D132: 1N914; D_DO-35_SOD27_P7.62mm_Horizontal
D5, D6, D7, D8, D9, D10, D11, D12, D13, D121, D122, D123, D124, D133, D134, D135, D136, D137, D138, D139, D140, D141, D142, D143, D144, D145, D146, D147, D148, D149, D150, D151, D152, D153, D154, D155, D156, D157, D158, D159, D160, D161, D162, D163, D164: LED; LED_D3.0mm
J2: Conn_02x10_Odd_Even; PinHeader_2x10_P2.00mm_Vertical
K1, K2, K3, K4, K45, K46, K47, K48, K49, K50, K51, K52, K53, K54, K55, K56, K57, K58, K59, K60, K61, K62, K63, K64, K65, K66, K67, K68, K69, K70, K71, K72, K73, K74, K75, K76, K77, K78, K79, K80, K81, K82, K83, K84, K89, K90, K91, K92, K93, K94, K95, K96: HK19F-DCxxV-SHC; Relay_DPDT_Finder_30.22
R1, R2, R3, R4, R5, R6, R7, R8, R9, R37, R38, R39, R40, R41, R42, R43, R44, R45, R46, R47, R48, R49, R50, R51, R52, R53, R54, R55, R56, R57, R58, R59, R60, R61, R62, R63, R64, R65, R66, R67, R68, R69, R70, R71, R72: R; R_Axial_DIN0204_L3.6mm_D1.6mm_P5.08mm_Horizontal
U1: Conn_RC_Male_100

Connections:
unnamed: D1.2 (A), D2.2 (A), D3.2 (A), D4.2 (A), K1.A2, K2.A2, K3.A2, K4.A2, R1.1
unnamed: D1.1 (K), D2.1 (K), D3.1 (K), D4.1 (K), D5.1 (K), D6.1 (K), D7.1 (K), D8.1 (K), D9.1 (K), D10.1 (K), D11.1 (K), D12.1 (K), D13.1 (K), D81.1 (K), D82.1 (K), D83.1 (K), D84.1 (K), D85.1 (K), D86.1 (K), D87.1 (K), D88.1 (K), D89.1 (K), D90.1 (K), D91.1 (K), D92.1 (K), D93.1 (K), D94.1 (K), D95.1 (K), D96.1 (K), D97.1 (K), D98.1 (K), D99.1 (K), D100.1 (K), D101.1 (K), D102.1 (K), D103.1 (K), D105.1 (K), D106.1 (K), D107.1 (K), D108.1 (K), D109.1 (K), D110.1 (K), D111.1 (K), D112.1 (K), D113.1 (K), D114.1 (K), D115.1 (K), D116.1 (K), D117.1 (K), D118.1 (K), D119.1 (K), D120.1 (K), D121.1 (K), D122.1 (K), D123.1 (K), D124.1 (K), D125.1 (K), D126.1 (K), D127.1 (K), D128.1 (K), D129.1 (K), D130.1 (K), D131.1 (K), D132.1 (K), D133.1 (K), D134.1 (K), D135.1 (K), D136.1 (K), D137.1 (K), D138.1 (K), D139.1 (K), D140.1 (K), D141.1 (K), D142.1 (K), D143.1 (K), D144.1 (K), D145.1 (K), D146.1 (K), D147.1 (K), D148.1 (K), D149.1 (K), D150.1 (K), D151.1 (K), D152.1 (K), D153.1 (K), D154.1 (K), D155.1 (K), D156.1 (K), D157.1 (K), D158.1 (K), D159.1 (K), D160.1 (K), D161.1 (K), D162.1 (K), D163.1 (K), D164.1 (K), K1.A1, K2.A1, K3.A1, K4.A1, K45.A1, K46.A1, K47.A1, K48.A1, K49.A1, K50.A1, K51.A1, K52.A1, K53.A1, K54.A1, K55.A1, K56.A1, K57.A1, K58.A1, K59.A1, K60.A1, K61.A1, K62.A1, K63.A1, K64.A1, K65.A1, K66.A1, K67.A1, K69.A1, K70.A1, K71.A1, K72.A1, K73.A1, K74.A1, K75.A1, K76.A1, K77.A1, K78.A1, K79.A1, K80.A1, K81.A1, K82.A1, K83.A1, K84.A1, K89.A1, K90.A1, K91.A1, K92.A1, K93.A1, K94.A1, K95.A1, K96.A1, U1.51 (GND)
unnamed: D5.2 (A), R1.2
unnamed: D6.2 (A), R2.2
unnamed: D7.2 (A), R3.2
unnamed: D8.2 (A), R4.2
unnamed: D9.2 (A), R5.2
unnamed: D10.2 (A), R6.2
unnamed: D11.2 (A), R7.2
unnamed: D12.2 (A), R8.2
unnamed: D13.2 (A), R9.2
unnamed: D81.2 (A), D82.2 (A), J2.6, K45.A2, K46.A2
unnamed: D83.2 (A), D84.2 (A), J2.5, K47.A2, K48.A2
unnamed: D85.2 (A), D87.2 (A), J2.7, K49.A2, K51.A2
unnamed: D86.2 (A), D88.2 (A), J2.8, K50.A2, K52.A2
unnamed: D89.2 (A), D91.2 (A), J2.9, K53.A2, K55.A2
unnamed: D90.2 (A), D92.2 (A), J2.10, K54.A2, K56.A2
unnamed: D93.2 (A), D95.2 (A), J2.11, K57.A2, K59.A2
unnamed: D94.2 (A), D96.2 (A), J2.12, K58.A2, K60.A2
unnamed: D97.2 (A), D99.2 (A), J2.13, K61.A2, K63.A2
unnamed: D98.2 (A), D100.2 (A), J2.14, K62.A2, K64.A2
unnamed: D101.2 (A), D103.2 (A), J2.15, K65.A2, K67.A2
unnamed: D102.2 (A), D104.2 (A), J2.16, K66.A2, K68.A2
unnamed: D104.1 (K), K68.A1
unnamed: D105.2 (A), D107.2 (A), J2.17, K69.A2, K71.A2
unnamed: D106.2 (A), D108.2 (A), J2.18, K70.A2, K72.A2
unnamed: D109.2 (A), D111.2 (A), J2.19, K73.A2, K75.A2
unnamed: D110.2 (A), D112.2 (A), J2.20, K74.A2, K76.A2
unnamed: D113.2 (A), D114.2 (A), D115.2 (A), D116.2 (A), J2.4, K77.A2, K78.A2, K79.A2, K80.A2, R37.1
unnamed: D117.2 (A), D118.2 (A), D119.2 (A), D120.2 (A), J2.2, K81.A2, K82.A2, K83.A2, K84.A2, R38.1
unnamed: D121.2 (A), R57.2
unnamed: D122.2 (A), R58.2
unnamed: D123.2 (A), R59.2
unnamed: D124.2 (A), R60.2
unnamed: D125.2 (A), D126.2 (A), D127.2 (A), D128.2 (A), J2.1, K89.A2, K90.A2, K91.A2, K92.A2, R39.1
unnamed: D129.2 (A), D131.2 (A), D132.2 (A), J2.3, K93.A2, K95.A2, K96.A2, R40.1
unnamed: D130.2 (A), K94.A2
unnamed: D133.2 (A), R37.2
unnamed: D134.2 (A), R38.2
unnamed: D135.2 (A), R39.2
unnamed: D136.2 (A), R40.2
unnamed: D137.2 (A), R41.2
unnamed: D138.2 (A), R42.2
unnamed: D139.2 (A), R43.2
unnamed: D140.2 (A), R44.2
unnamed: D141.2 (A), R45.2
unnamed: D142.2 (A), R46.2
unnamed: D143.2 (A), R47.2
unnamed: D144.2 (A), R48.2
unnamed: D145.2 (A), R49.2
unnamed: D146.2 (A), R50.2
unnamed: D147.2 (A), R51.2
unnamed: D148.2 (A), R52.2
unnamed: D149.2 (A), R53.2
unnamed: D150.2 (A), R54.2
unnamed: D151.2 (A), R55.2
unnamed: D152.2 (A), R56.2
unnamed: D153.2 (A), R61.2
unnamed: D154.2 (A), R62.2
unnamed: D155.2 (A), R63.2
unnamed: D156.2 (A), R64.2
unnamed: D157.2 (A), R65.2
unnamed: D158.2 (A), R66.2
unnamed: D159.2 (A), R67.2
unnamed: D160.2 (A), R68.2
unnamed: D161.2 (A), R69.2
unnamed: D162.2 (A), R70.2
unnamed: D163.2 (A), R71.2
unnamed: D164.2 (A), R72.2
unnamed: K1.11, K52.24, R8.1
unnamed: K1.21, K46.24, R9.1
unnamed: K2.11, K60.24, R6.1
unnamed: K2.21, K56.24, R7.1
unnamed: K3.11, K68.24, R4.1
unnamed: K3.21, K64.24, R5.1
unnamed: K4.11, K76.24, R2.1
unnamed: K4.21, K72.24, R3.1
unnamed: K45.14, K47.24, K81.21, R64.1
unnamed: K45.21, K77.21, R72.1
unnamed: K45.24, K47.14
unnamed: K46.11, K93.21, R48.1
unnamed: K46.12, K48.14
unnamed: K46.14, K48.12
unnamed: K47.12, K89.21, R56.1
unnamed: K49.12, K89.11, R55.1
unnamed: K49.14, K50.24
unnamed: K49.24, K50.14, K81.11, R63.1
unnamed: K50.21, K77.11, R71.1
unnamed: K51.12, K52.14
unnamed: K51.14, K52.12
unnamed: K52.11, K93.11, R47.1
unnamed: K53.12, K90.21, R54.1
unnamed: K53.14, K54.24
unnamed: K53.24, K54.14, K82.21, R62.1
unnamed: K54.21, K78.21, R70.1
unnamed: K55.12, K56.14
unnamed: K55.14, K56.12
unnamed: K56.11, K94.21, R46.1
unnamed: K57.12, K90.11, R53.1
unnamed: K57.14, K58.24
unnamed: K57.24, K58.14, K82.11, R61.1
unnamed: K58.21, K78.11, R69.1
unnamed: K59.12, K60.14
unnamed: K59.14, K60.12
unnamed: K60.11, K94.11, R45.1
unnamed: K61.12, K91.21, R52.1
unnamed: K61.14, K62.24
unnamed: K61.24, K62.14, K83.21, R60.1
unnamed: K62.21, K79.21, R68.1
unnamed: K63.12, K64.14
unnamed: K63.14, K64.12
unnamed: K64.11, K95.21, R44.1
unnamed: K65.12, K91.11, R51.1
unnamed: K65.14, K66.24
unnamed: K65.24, K66.14, K83.11, R59.1
unnamed: K66.21, K79.11, R67.1
unnamed: K67.12, K68.14
unnamed: K67.14, K68.12
unnamed: K68.11, K95.11, R43.1
unnamed: K69.12, K92.21, R50.1
unnamed: K69.14, K70.24
unnamed: K69.24, K70.14, K84.21, R58.1
unnamed: K70.21, K80.21, R66.1
unnamed: K71.12, K72.14
unnamed: K71.14, K72.12
unnamed: K72.11, K96.21, R42.1
unnamed: K73.12, K92.11, R49.1
unnamed: K73.14, K74.24
unnamed: K73.24, K74.14, K84.11, R57.1
unnamed: K74.21, K80.11, R65.1
unnamed: K75.12, K76.14
unnamed: K75.14, K76.12
unnamed: K76.11, K96.11, R41.1
unnamed: K45.11, K46.21, K47.11, K47.21, K48.11, K49.11, K49.21, K50.11, K51.11, K52.21, K53.11, K53.21, K54.11, K55.11, K56.21, K57.11, K57.21, K58.11, K59.11, K60.21, K61.11, K61.21, K62.11, K63.11, K64.21, K65.11, K65.21, K66.11, K67.11, K68.21, K69.11, K69.21, K70.11, K71.11, K72.21, K73.11, K73.21, K74.11, K75.11, K76.21, U1.1 (5_Volt)
unnamed: K4.14, K80.14, K84.14, K92.14, K96.14, U1.2 (D0)
unnamed: K4.24, K80.24, K84.24, K92.24, K96.24, U1.3 (D1)
unnamed: K3.14, K79.14, K83.14, K91.14, K95.14, U1.4 (D2)
unnamed: K3.24, K79.24, K83.24, K91.24, K95.24, U1.5 (D3)
unnamed: K2.14, K78.14, K82.14, K90.14, K94.14, U1.6 (D4)
unnamed: K2.24, K78.24, K82.24, K90.24, K94.24, U1.7 (D5)
unnamed: K1.14, K77.14, K81.14, K89.14, K93.14, U1.8 (D6)
unnamed: K1.24, K77.24, K81.24, K89.24, K93.24, U1.9 (D7)
